seemecnc/Orion_Delta/USER_MANUAL/images/set-zero-point.jpg

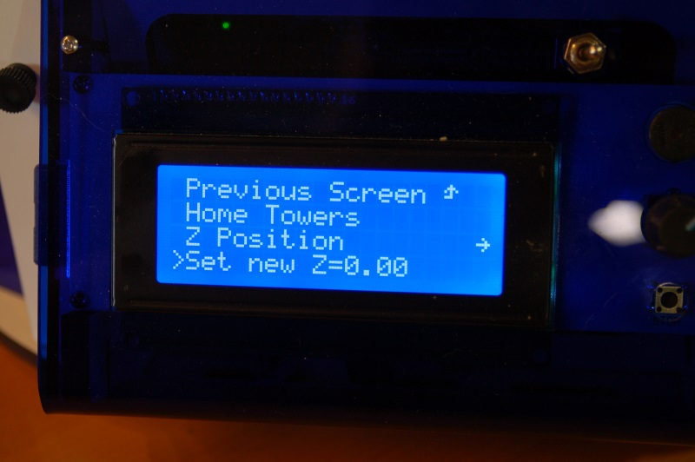
USER_MANUAL/images/set-zero-point.jpg
