seemecnc/Orion_Delta/USER_MANUAL/images/10858079405_2d53c97f4e_c.jpg

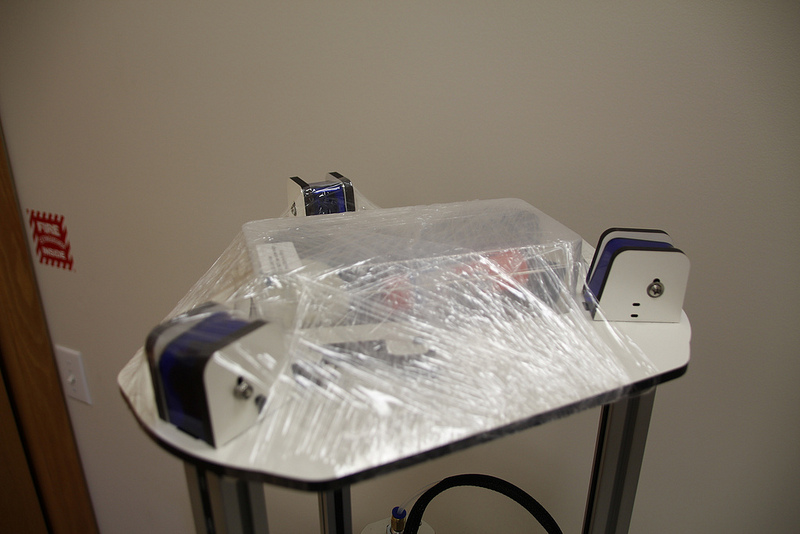
USER_MANUAL/images/10858079405_2d53c97f4e_c.jpg
