seemecnc/Orion_Delta/CAD/IGES/Switch Micro Lever.IGS

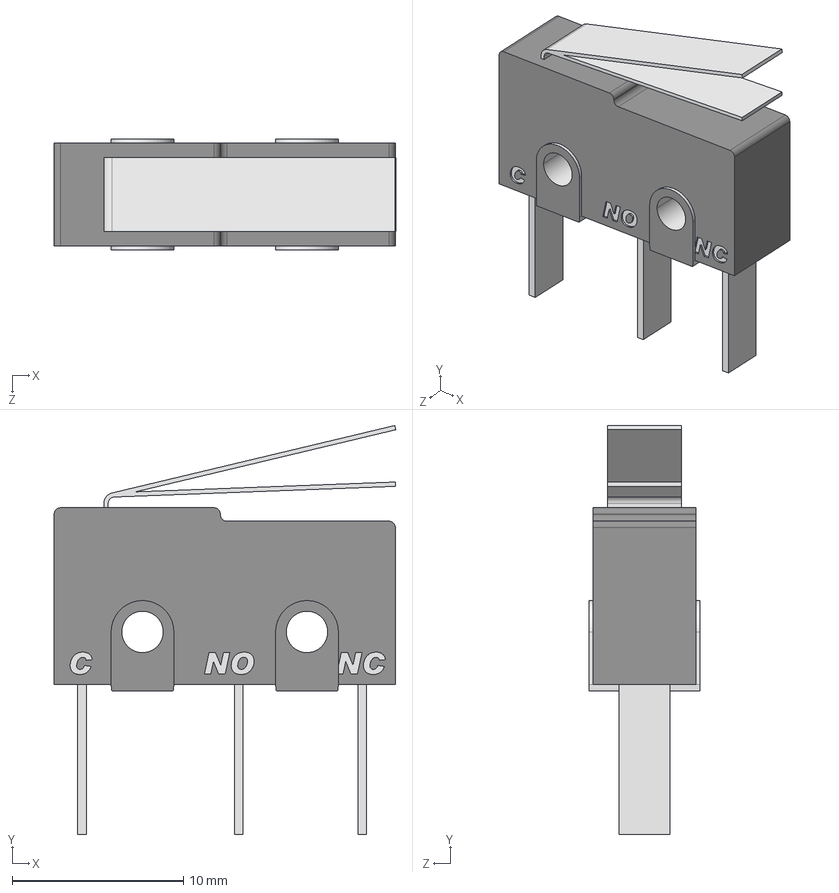
[picture p18: CAD file, 2013-10-02]
CAD/IGES/Switch Micro Lever.IGS
19.9 x 23.9 x 6.48 mm
