seemecnc/Orion_Delta/CAD/IGES/40mmFAN.IGS

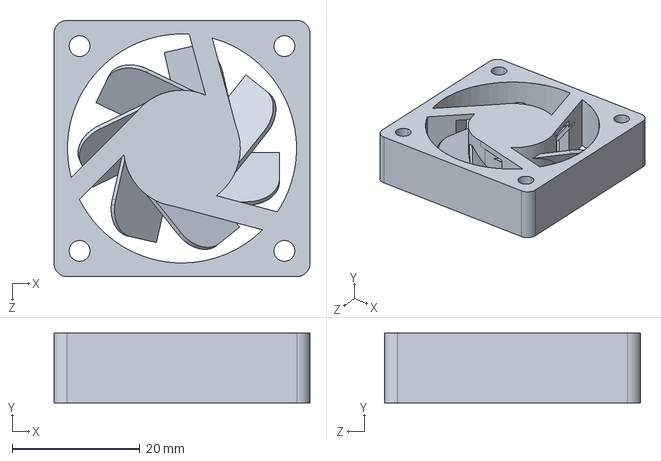
[picture p19: CAD file, 2013-10-02]
CAD/IGES/40mmFAN.IGS
40.0 x 10.9 x 40.0 mm
