seemecnc/Orion_Delta/CAD/IGES/spacer.IGS

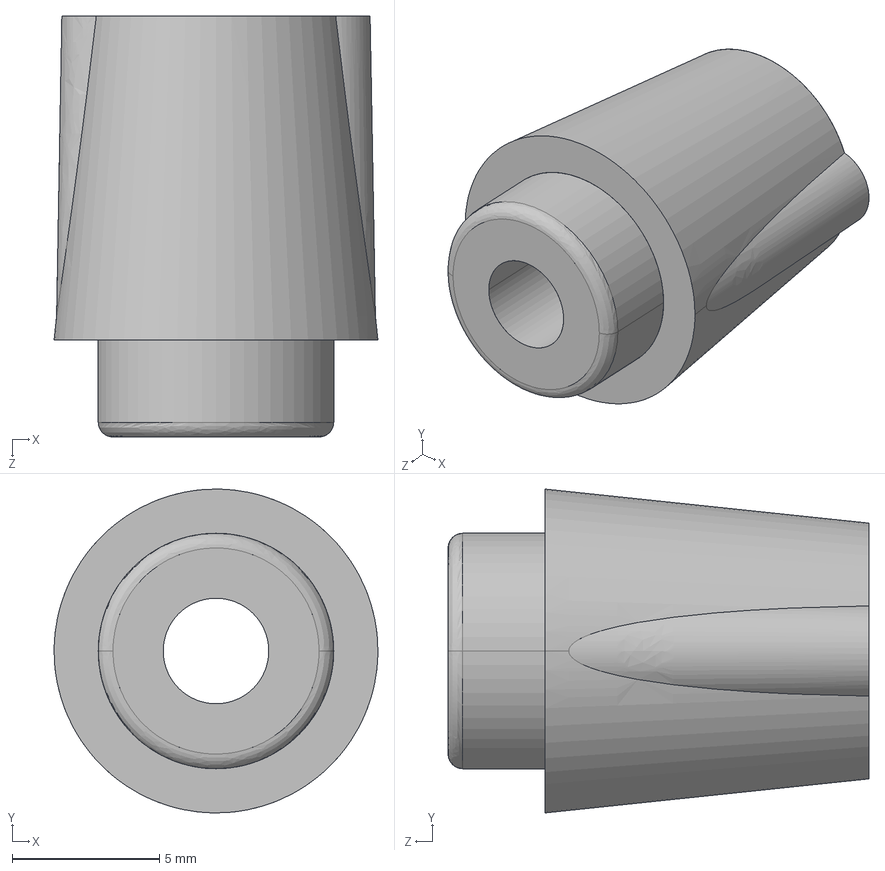
[picture p20: CAD file, 2013-10-02]
CAD/IGES/spacer.IGS
11.0 x 11.0 x 14.3 mm
