seemecnc/Orion_Delta/USER_MANUAL/images/3d-view-keychain.png

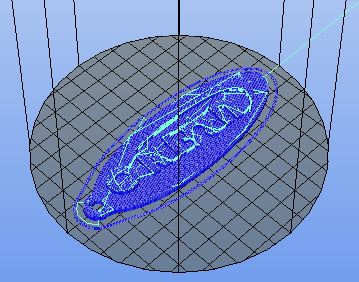
USER_MANUAL/images/3d-view-keychain.png
