seemecnc/Orion_Delta/USER_MANUAL/images/20deg.jpg

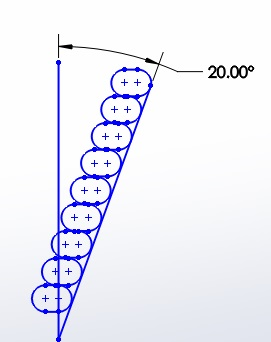
USER_MANUAL/images/20deg.jpg
