seemecnc/Orion_Delta/USER_MANUAL/images/45deg.jpg

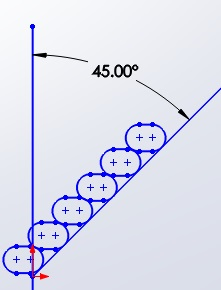
USER_MANUAL/images/45deg.jpg
