seemecnc/Orion_Delta/USER_MANUAL/images/75deg.jpg

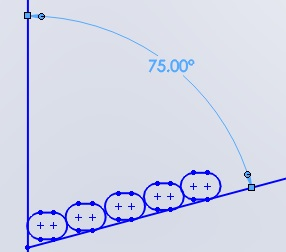
USER_MANUAL/images/75deg.jpg
