seemecnc/Orion_Delta/USER_MANUAL/images/10857993875_b573bbbdb2_c.jpg

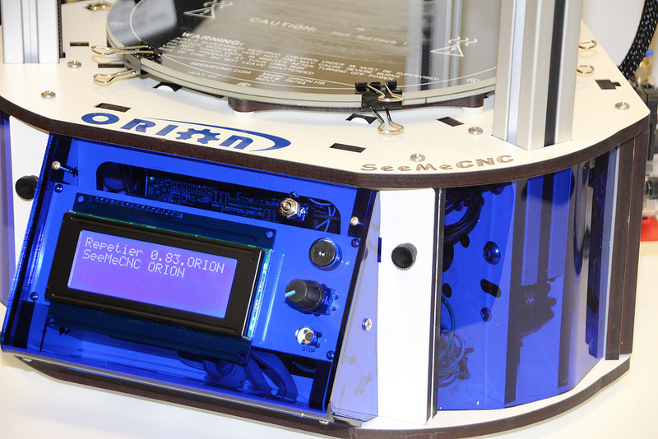
USER_MANUAL/images/10857993875_b573bbbdb2_c.jpg
