seemecnc/Orion_Delta/USER_MANUAL/images/10857997695_c42692fac6_c.jpg

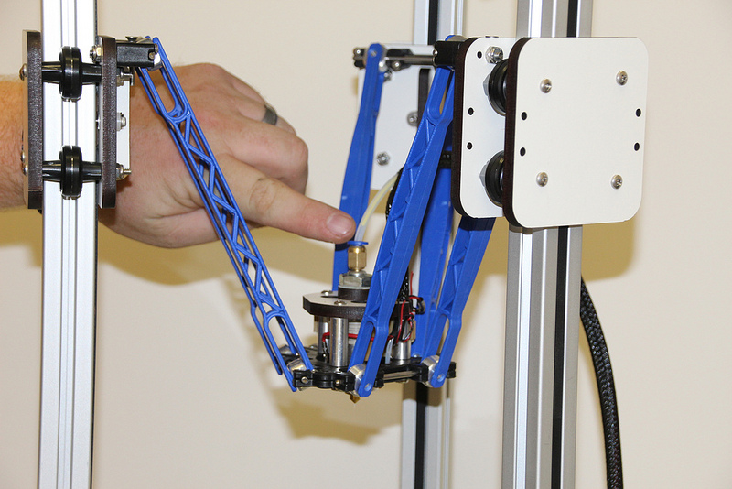
USER_MANUAL/images/10857997695_c42692fac6_c.jpg
