seemecnc/Orion_Delta/USER_MANUAL/images/10857999175_edf28102e8_c.jpg

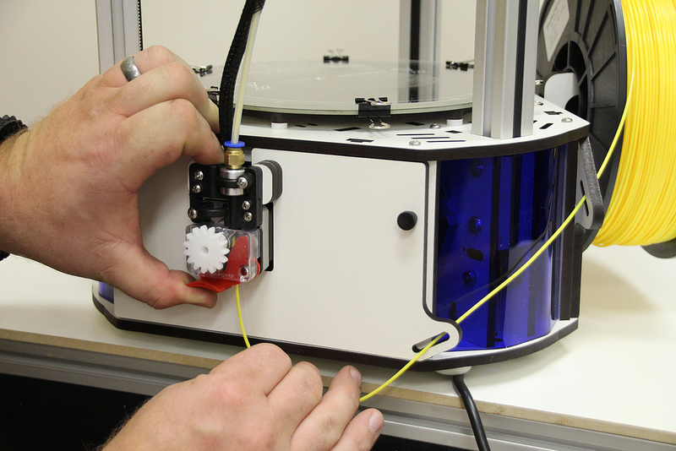
USER_MANUAL/images/10857999175_edf28102e8_c.jpg
