seemecnc/Orion_Delta/USER_MANUAL/images/10858003085_644f556bda_c.jpg

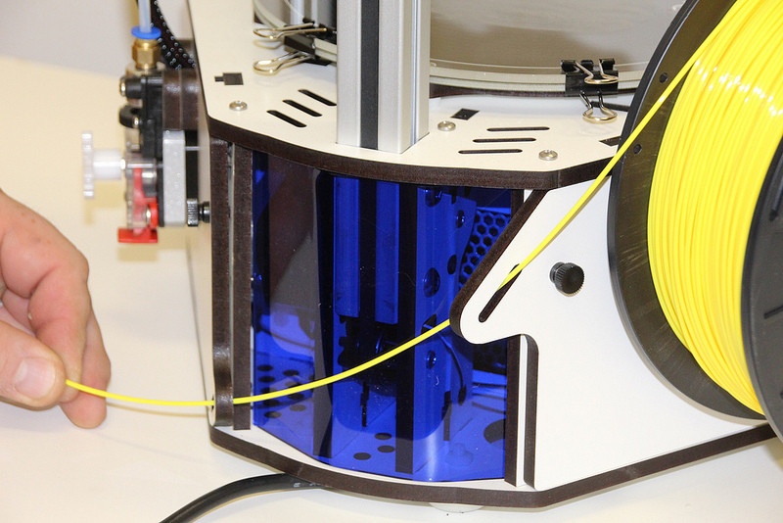
USER_MANUAL/images/10858003085_644f556bda_c.jpg
