seemecnc/Orion_Delta/USER_MANUAL/images/10858004465_a517190b95_c.jpg

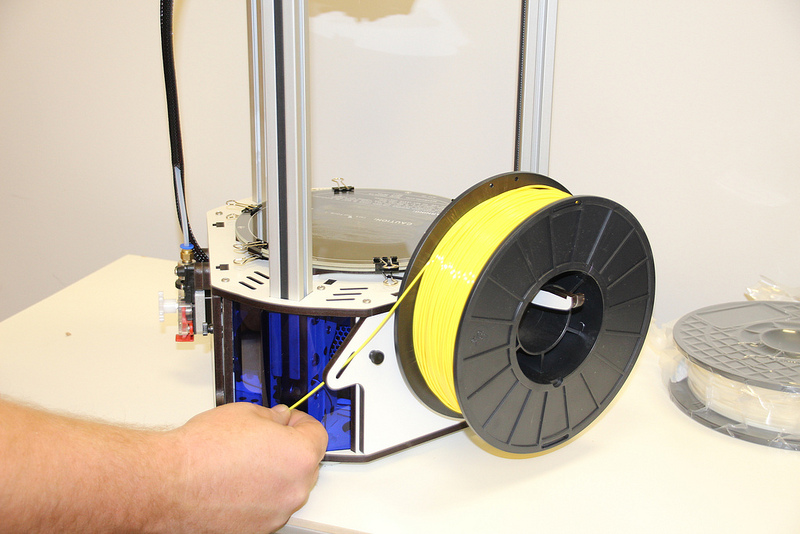
USER_MANUAL/images/10858004465_a517190b95_c.jpg
