seemecnc/Orion_Delta/USER_MANUAL/images/10858016405_97d147c111_c.jpg

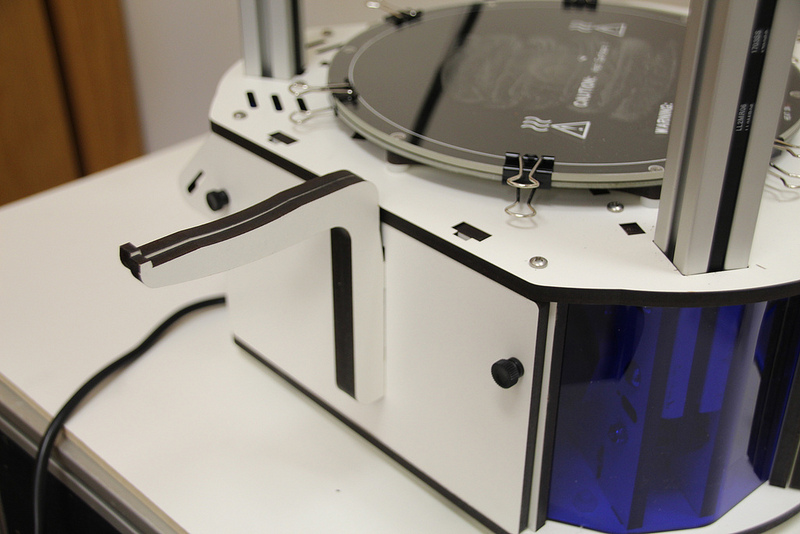
USER_MANUAL/images/10858016405_97d147c111_c.jpg
