seemecnc/Orion_Delta/USER_MANUAL/images/10858027235_418935b61d_c.jpg

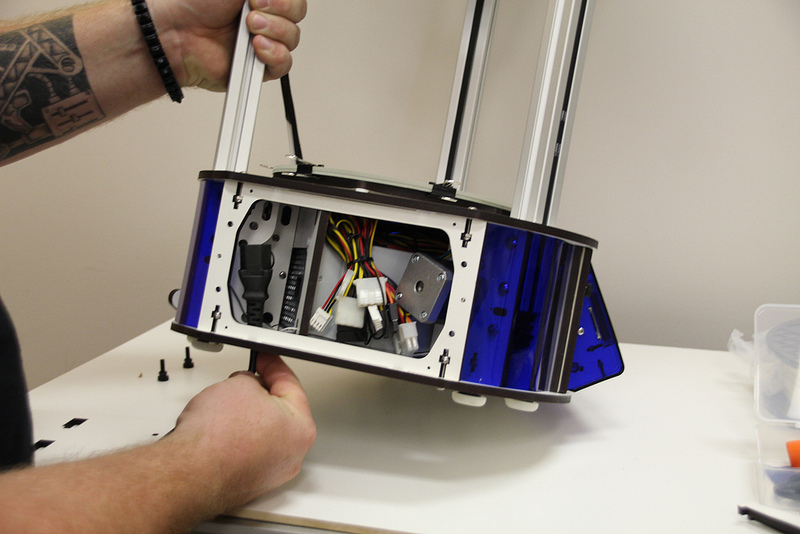
USER_MANUAL/images/10858027235_418935b61d_c.jpg
