seemecnc/Orion_Delta/USER_MANUAL/images/10858029525_48f6b91417_c.jpg

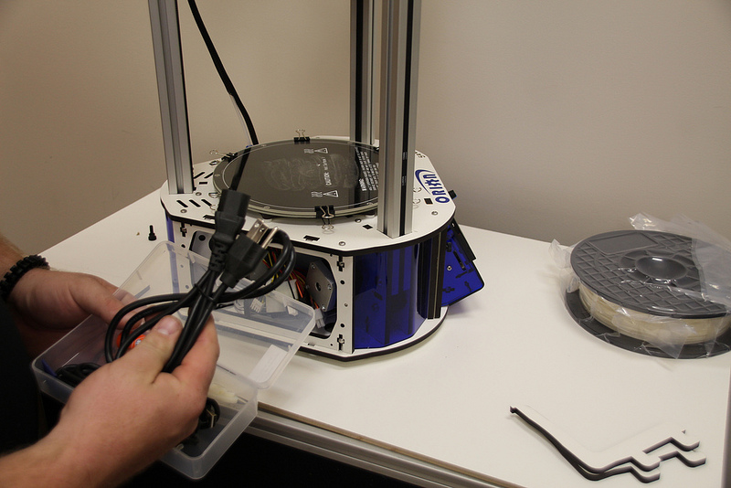
USER_MANUAL/images/10858029525_48f6b91417_c.jpg
