seemecnc/Orion_Delta/USER_MANUAL/images/10858043166_c10c539a0d_c.jpg

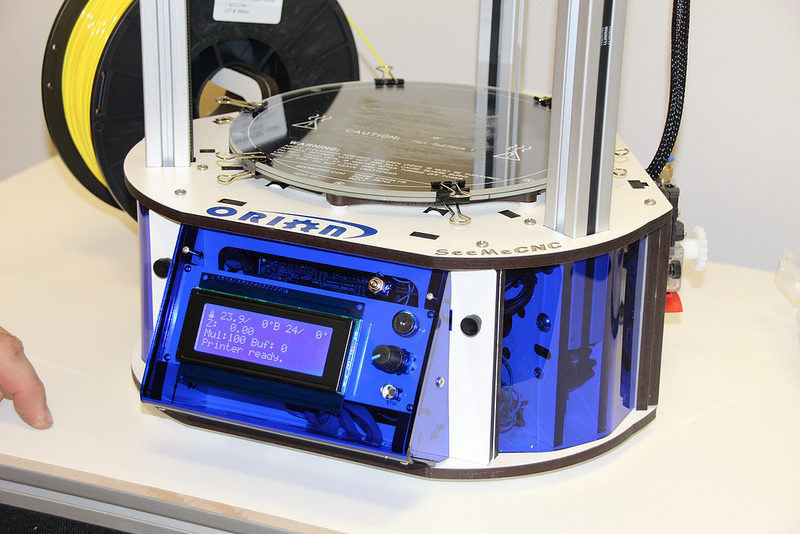
USER_MANUAL/images/10858043166_c10c539a0d_c.jpg
