seemecnc/Orion_Delta/USER_MANUAL/images/10858051416_cd726fda2a_c.jpg

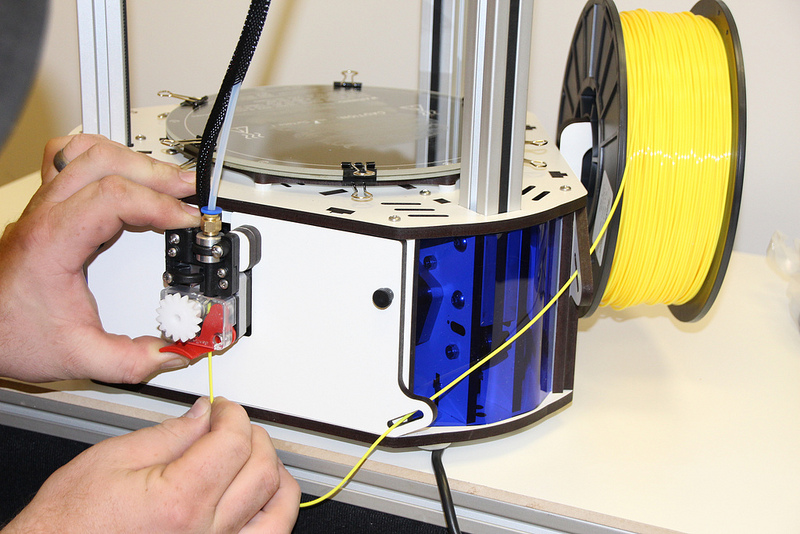
USER_MANUAL/images/10858051416_cd726fda2a_c.jpg
