seemecnc/Orion_Delta/USER_MANUAL/images/10858056896_ca6db3baf7_c.jpg

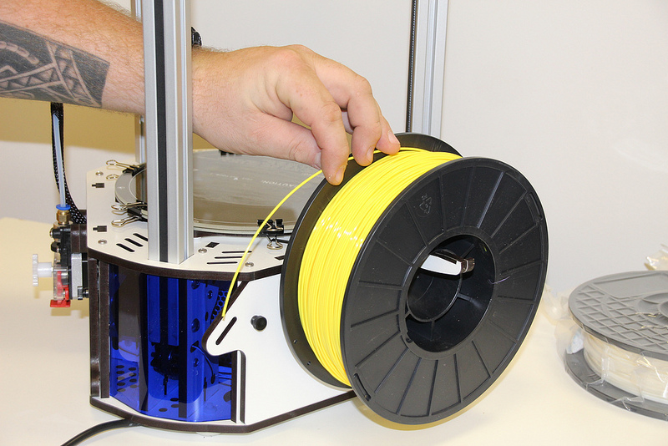
USER_MANUAL/images/10858056896_ca6db3baf7_c.jpg
