seemecnc/Orion_Delta/USER_MANUAL/images/10858063376_e0e1a32779_c.jpg

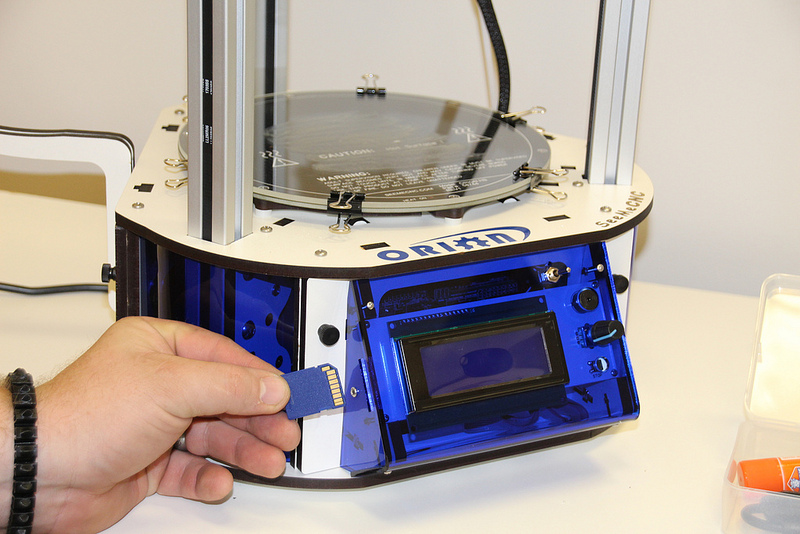
USER_MANUAL/images/10858063376_e0e1a32779_c.jpg
