seemecnc/Orion_Delta/USER_MANUAL/images/10858071566_8f59dc56c1_c.jpg

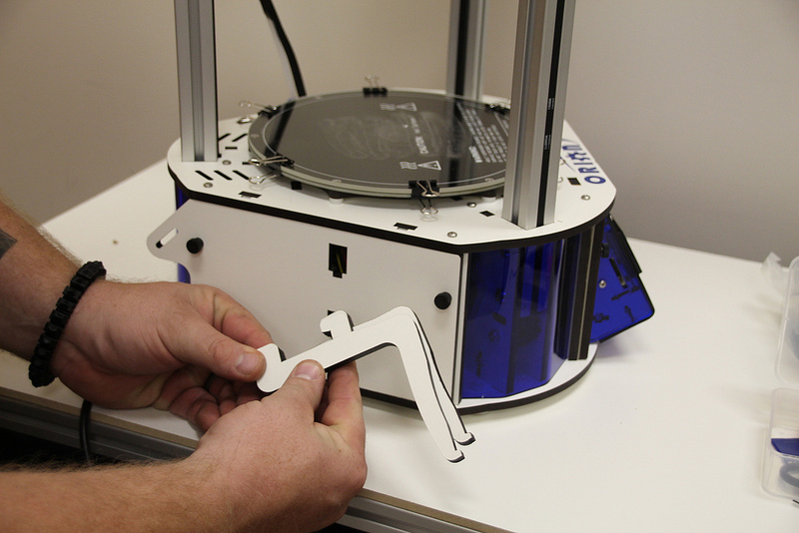
USER_MANUAL/images/10858071566_8f59dc56c1_c.jpg
