seemecnc/Orion_Delta/USER_MANUAL/images/10858087996_081414d4be_c.jpg

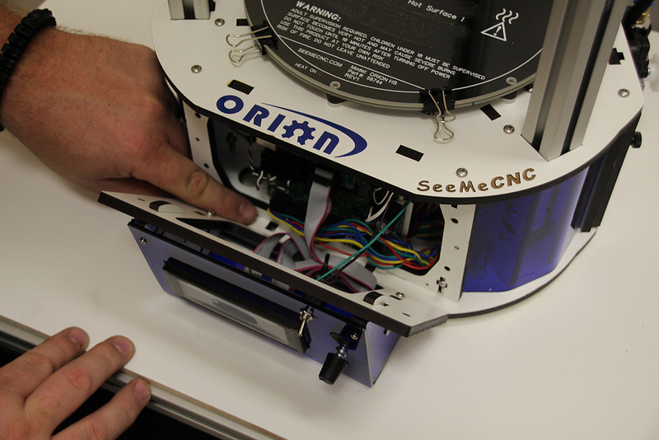
USER_MANUAL/images/10858087996_081414d4be_c.jpg
