seemecnc/Orion_Delta/USER_MANUAL/images/10858104786_4468d310ae_c.jpg

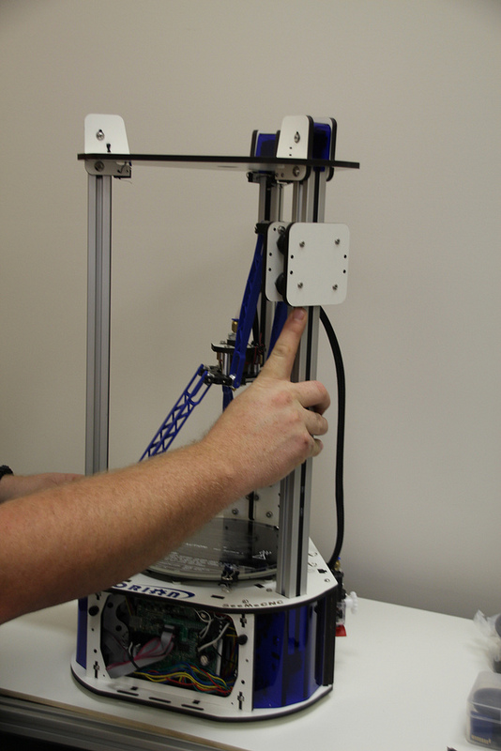
USER_MANUAL/images/10858104786_4468d310ae_c.jpg
