seemecnc/Orion_Delta/USER_MANUAL/images/10858115596_f1e3a82ac3_c.jpg

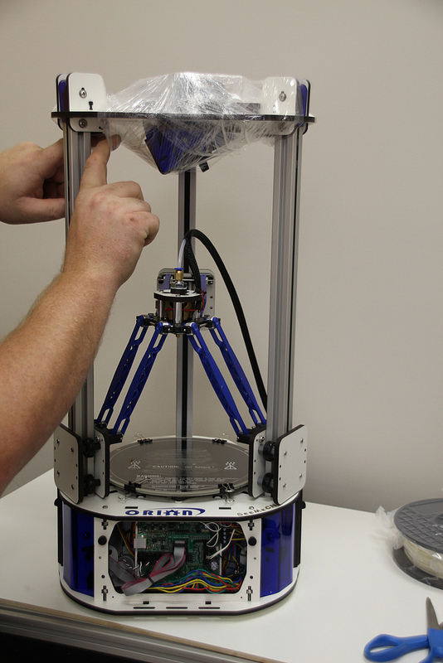
USER_MANUAL/images/10858115596_f1e3a82ac3_c.jpg
