seemecnc/Orion_Delta/USER_MANUAL/images/10858133396_417945009c_c.jpg

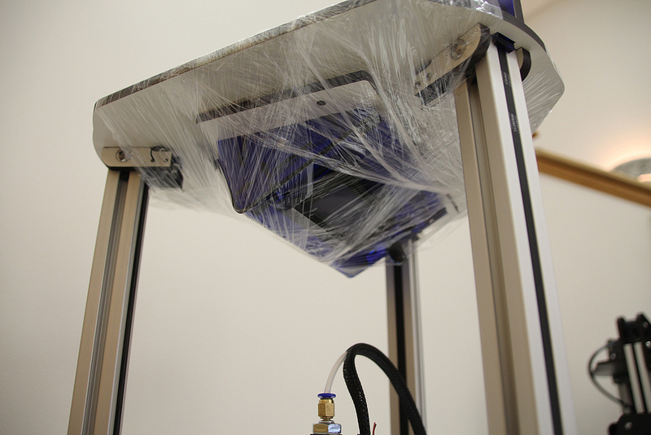
USER_MANUAL/images/10858133396_417945009c_c.jpg
