seemecnc/Orion_Delta/USER_MANUAL/images/10858134636_70626f2765_c.jpg

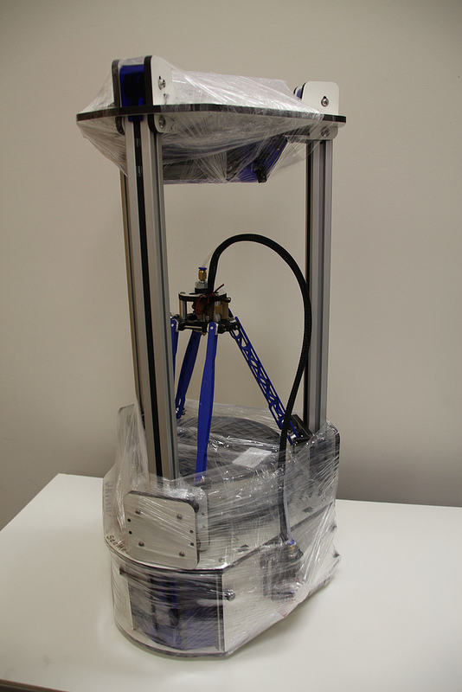
USER_MANUAL/images/10858134636_70626f2765_c.jpg
