seemecnc/Orion_Delta/USER_MANUAL/images/10858135606_6d0c017a09_c.jpg

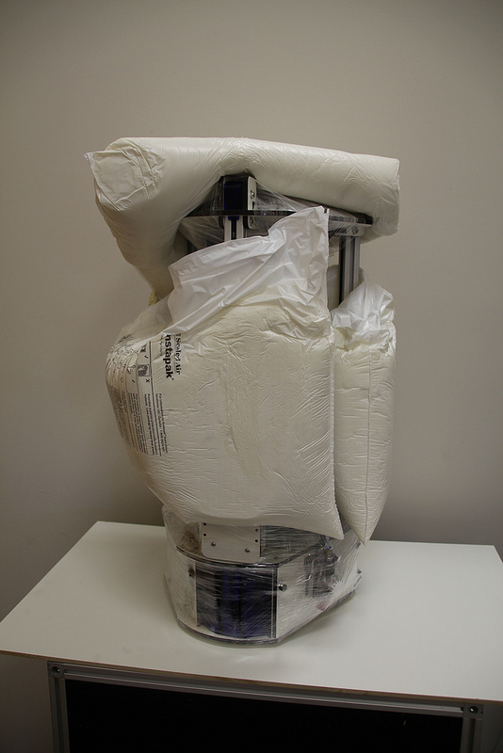
USER_MANUAL/images/10858135606_6d0c017a09_c.jpg
