seemecnc/Orion_Delta/USER_MANUAL/images/10858138586_e7d71295ff_c.jpg

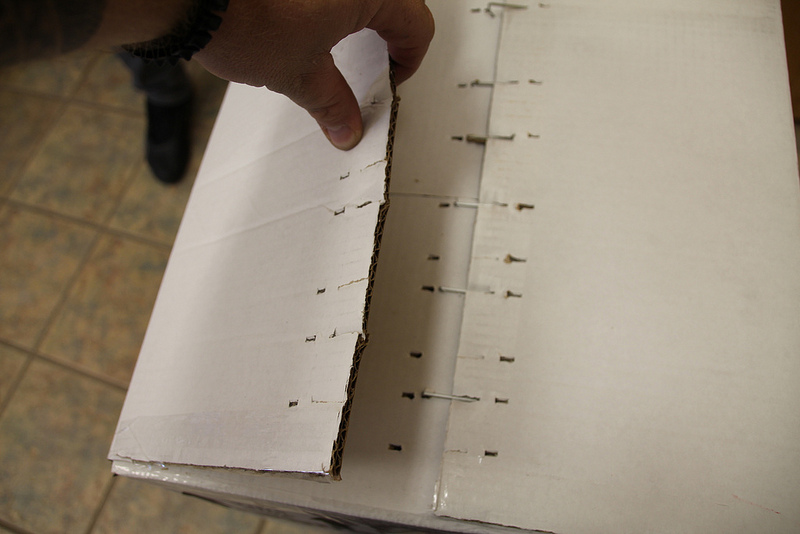
USER_MANUAL/images/10858138586_e7d71295ff_c.jpg
