seemecnc/Orion_Delta/USER_MANUAL/images/10858149814_d947ce7413_c.jpg

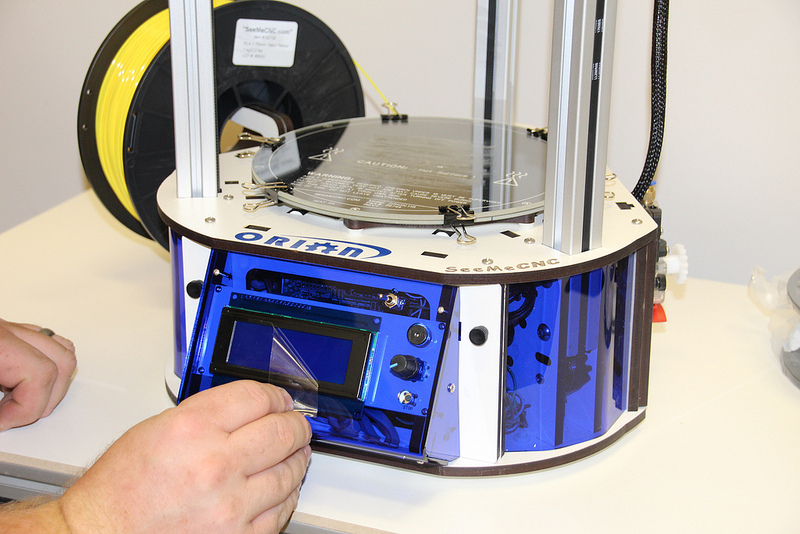
USER_MANUAL/images/10858149814_d947ce7413_c.jpg
