seemecnc/Orion_Delta/USER_MANUAL/images/10858156424_11ed93d5b6_c.jpg

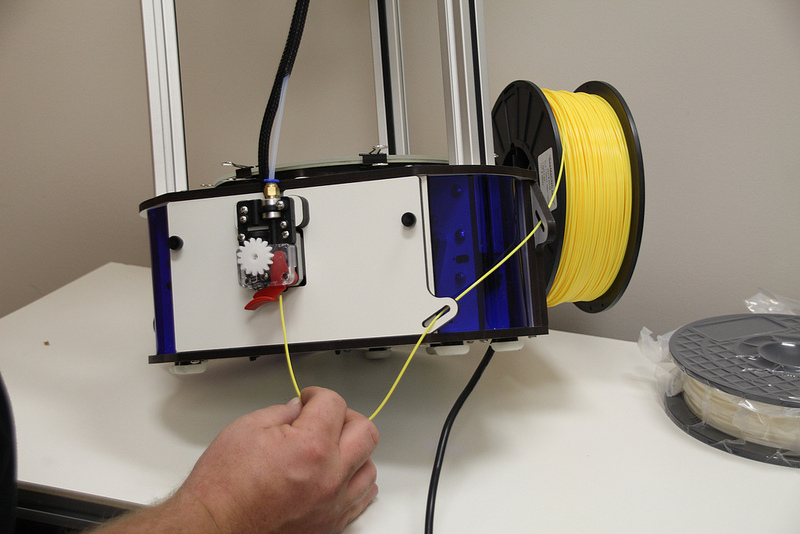
USER_MANUAL/images/10858156424_11ed93d5b6_c.jpg
