seemecnc/Orion_Delta/USER_MANUAL/images/10858165754_4ae52a8649_c.jpg

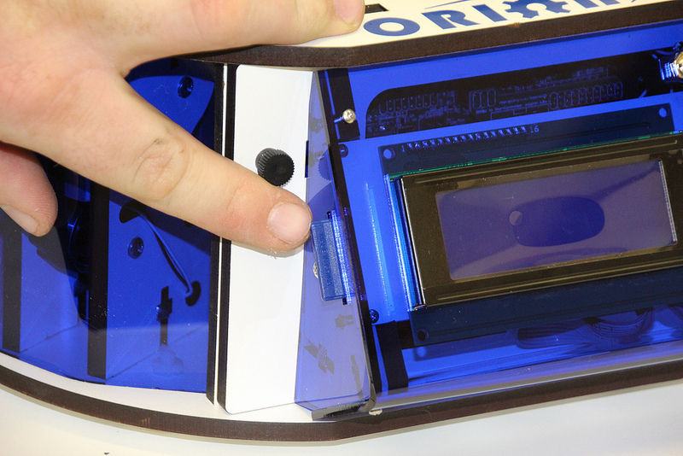
USER_MANUAL/images/10858165754_4ae52a8649_c.jpg
