seemecnc/Orion_Delta/USER_MANUAL/images/10858187334_f6d8ebac16_c.jpg

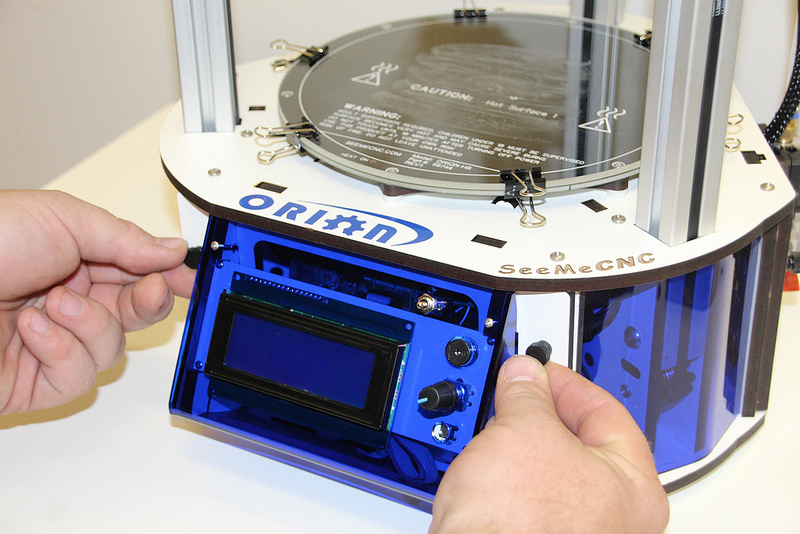
USER_MANUAL/images/10858187334_f6d8ebac16_c.jpg
