seemecnc/Orion_Delta/USER_MANUAL/images/10858193964_cc0fbacdeb_c.jpg

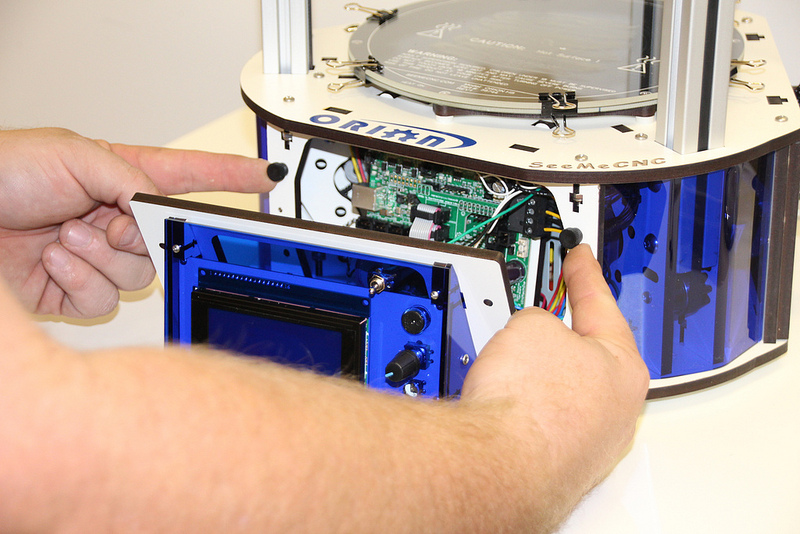
USER_MANUAL/images/10858193964_cc0fbacdeb_c.jpg
