seemecnc/Orion_Delta/USER_MANUAL/images/10858195264_8df696b53b_c.jpg

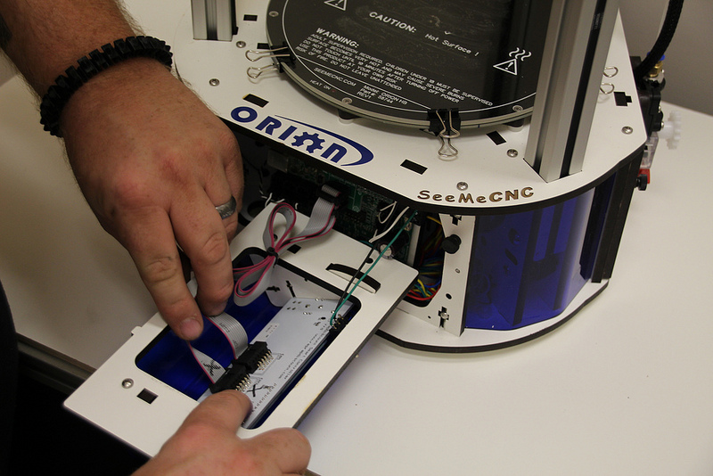
USER_MANUAL/images/10858195264_8df696b53b_c.jpg
