seemecnc/Orion_Delta/USER_MANUAL/images/10858196814_af65e72ff8_c.jpg

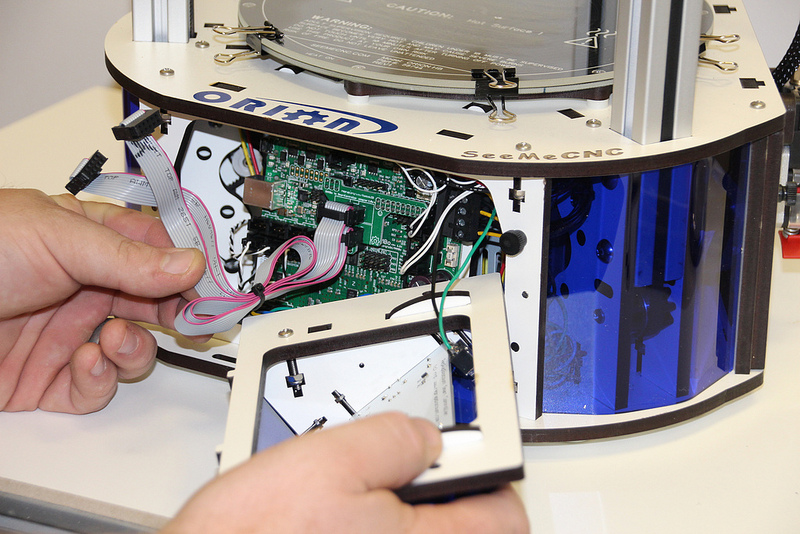
USER_MANUAL/images/10858196814_af65e72ff8_c.jpg
