seemecnc/Orion_Delta/USER_MANUAL/images/10858198144_2c69749b12_c.jpg

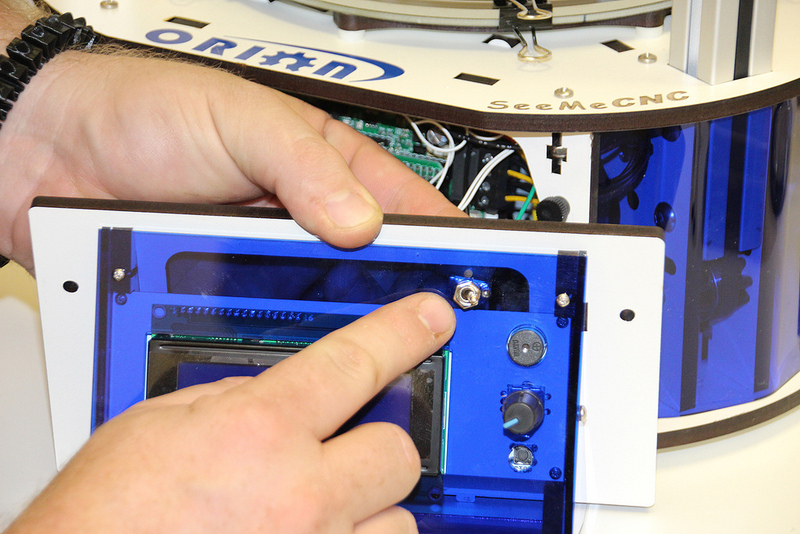
USER_MANUAL/images/10858198144_2c69749b12_c.jpg
