seemecnc/Orion_Delta/USER_MANUAL/images/10858201544_ca3241cb73_c.jpg

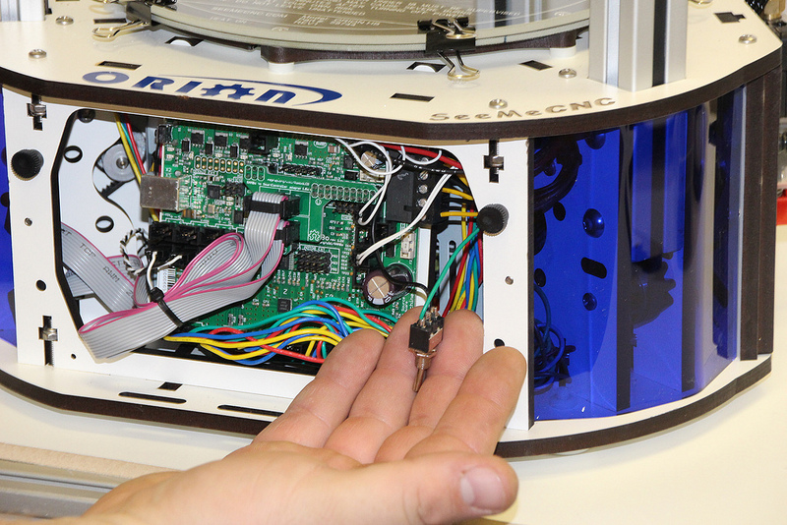
USER_MANUAL/images/10858201544_ca3241cb73_c.jpg
