seemecnc/Orion_Delta/USER_MANUAL/images/10858215504_7f9ed28df2_c.jpg

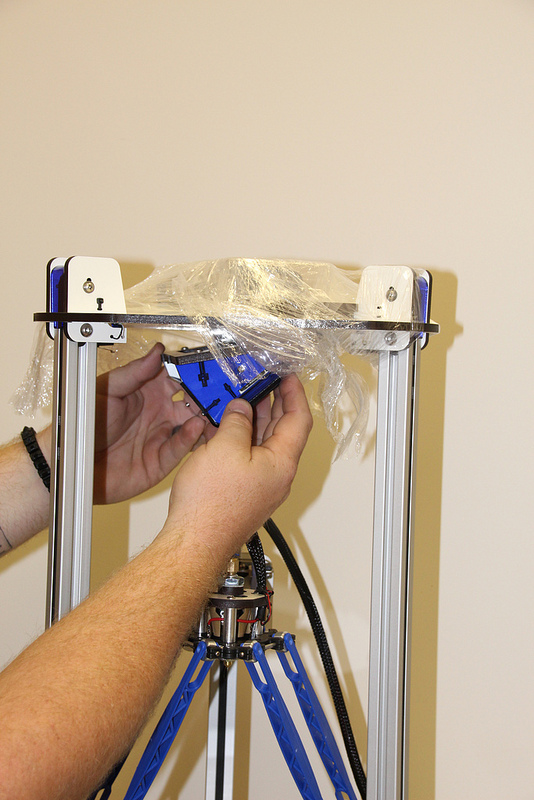
USER_MANUAL/images/10858215504_7f9ed28df2_c.jpg
