seemecnc/Orion_Delta/USER_MANUAL/images/10858355013_c423ee9d34_c.jpg

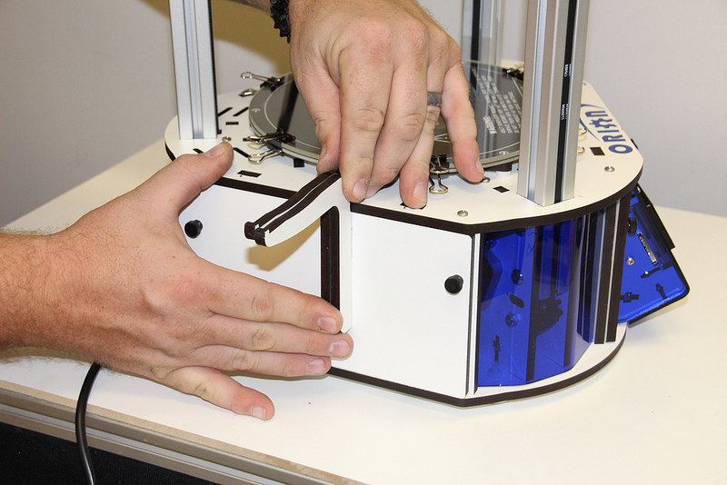
USER_MANUAL/images/10858355013_c423ee9d34_c.jpg
