seemecnc/Orion_Delta/USER_MANUAL/images/10858356373_2051489b07_c.jpg

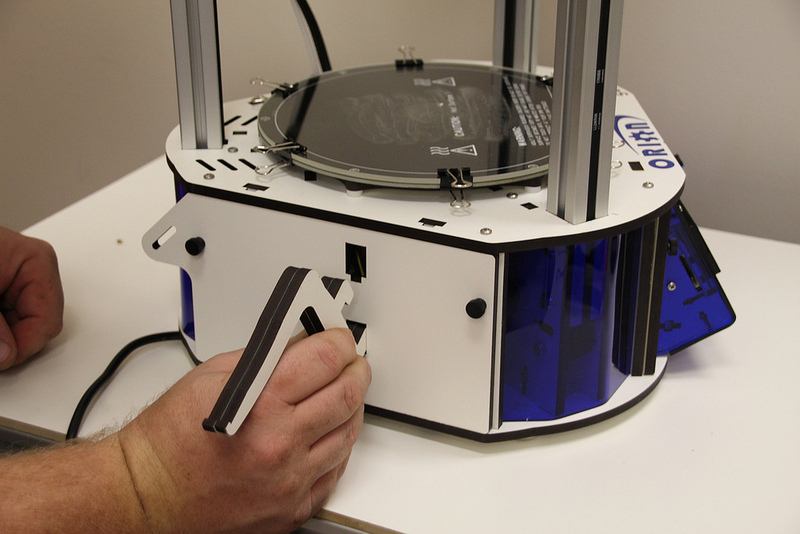
USER_MANUAL/images/10858356373_2051489b07_c.jpg
