seemecnc/Orion_Delta/USER_MANUAL/images/10858360663_d777211012_c.jpg

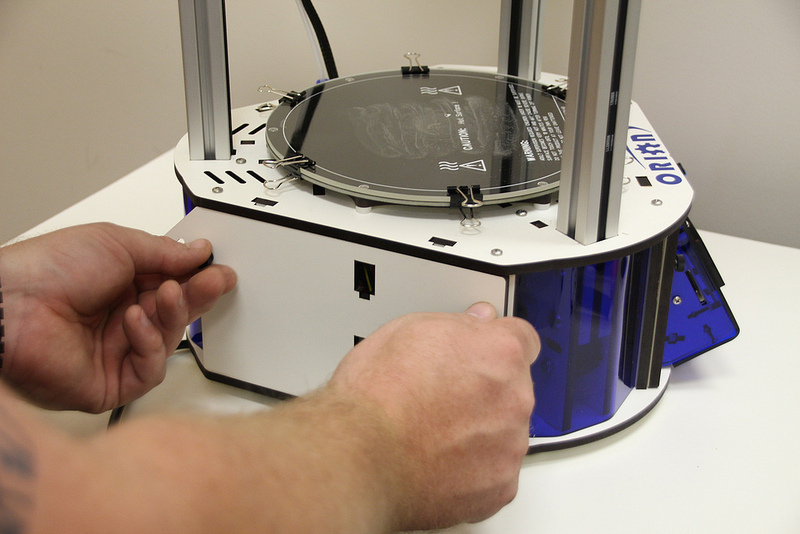
USER_MANUAL/images/10858360663_d777211012_c.jpg
