seemecnc/Orion_Delta/USER_MANUAL/images/10858363363_4431cff72f_c.jpg

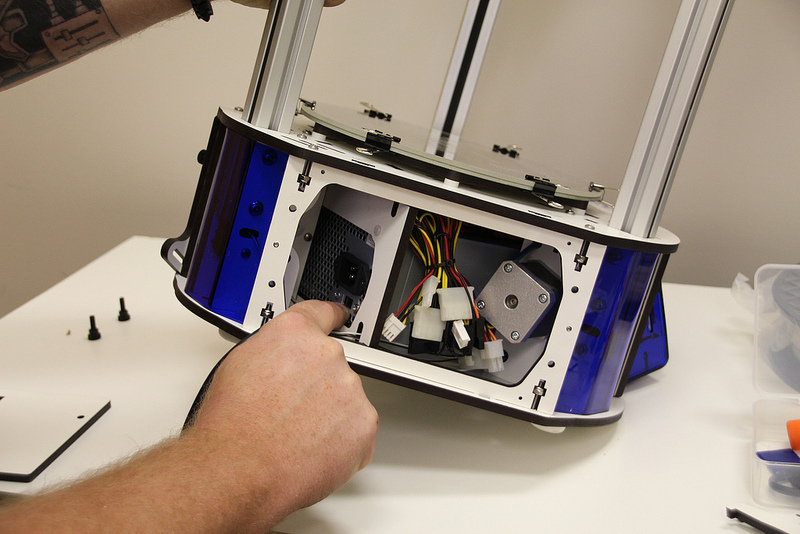
USER_MANUAL/images/10858363363_4431cff72f_c.jpg
