seemecnc/Orion_Delta/USER_MANUAL/images/10858369133_35604c40fe_c.jpg

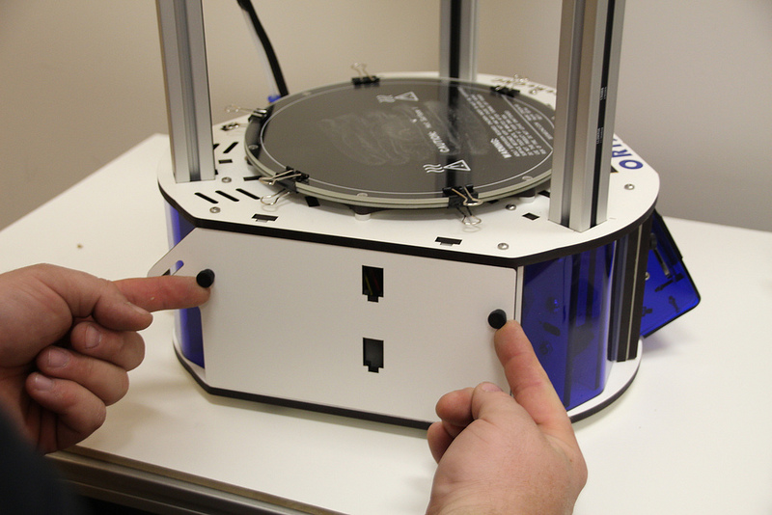
USER_MANUAL/images/10858369133_35604c40fe_c.jpg
