seemecnc/Orion_Delta/USER_MANUAL/images/10858371613_db3799a69a_c.jpg

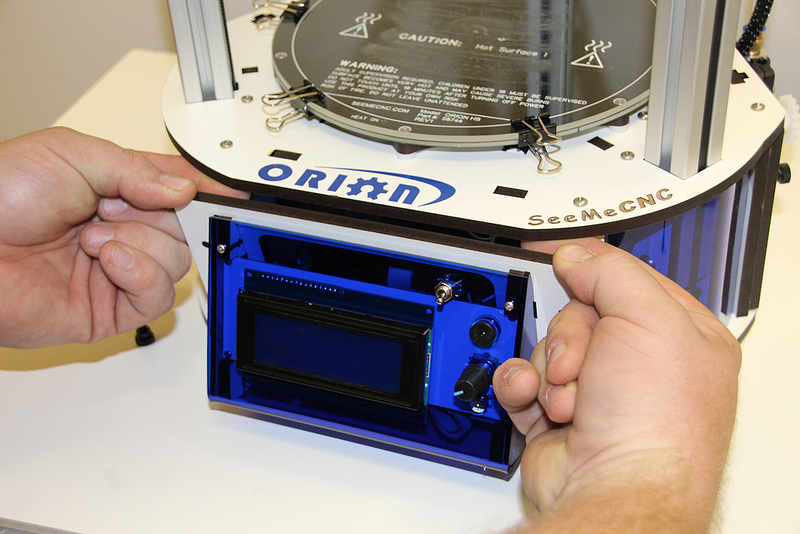
USER_MANUAL/images/10858371613_db3799a69a_c.jpg
