seemecnc/Orion_Delta/USER_MANUAL/images/10858372973_1e9f0c7b8a_c.jpg

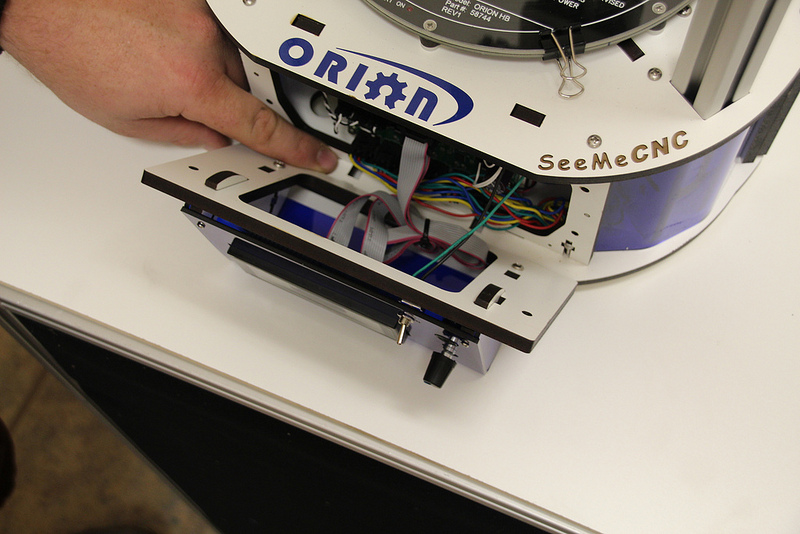
USER_MANUAL/images/10858372973_1e9f0c7b8a_c.jpg
