seemecnc/Orion_Delta/USER_MANUAL/images/10858383403_f076f69c96_c.jpg

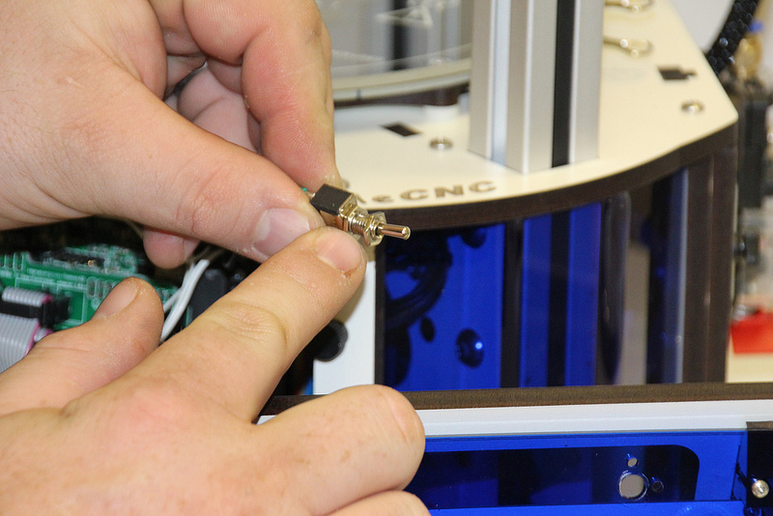
USER_MANUAL/images/10858383403_f076f69c96_c.jpg
