seemecnc/Orion_Delta/USER_MANUAL/images/10858387633_c5c9b00cb3_c.jpg

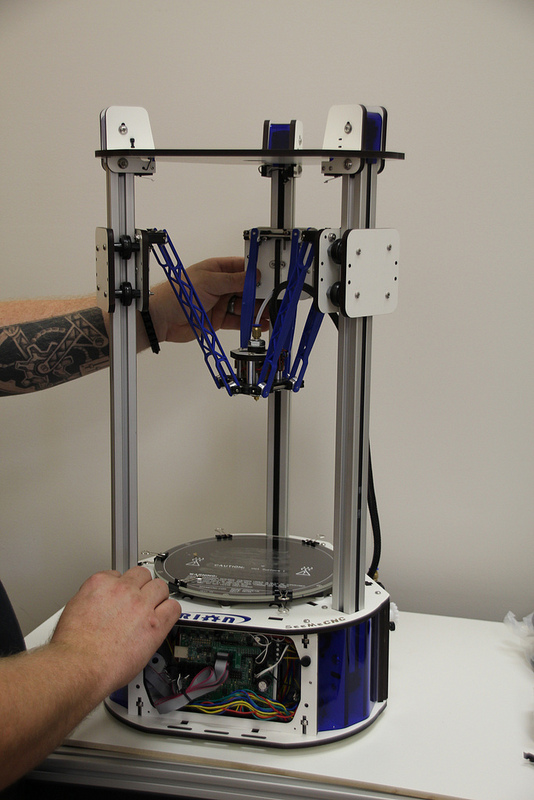
USER_MANUAL/images/10858387633_c5c9b00cb3_c.jpg
