seemecnc/Orion_Delta/USER_MANUAL/images/10858390063_a34ffba0bb_c.jpg

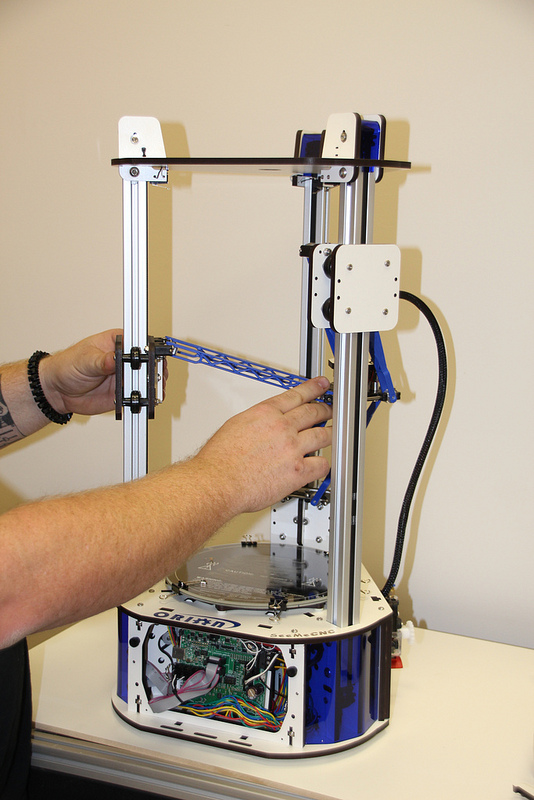
USER_MANUAL/images/10858390063_a34ffba0bb_c.jpg
