seemecnc/Orion_Delta/USER_MANUAL/images/10858397873_ab5069cfe1_c.jpg

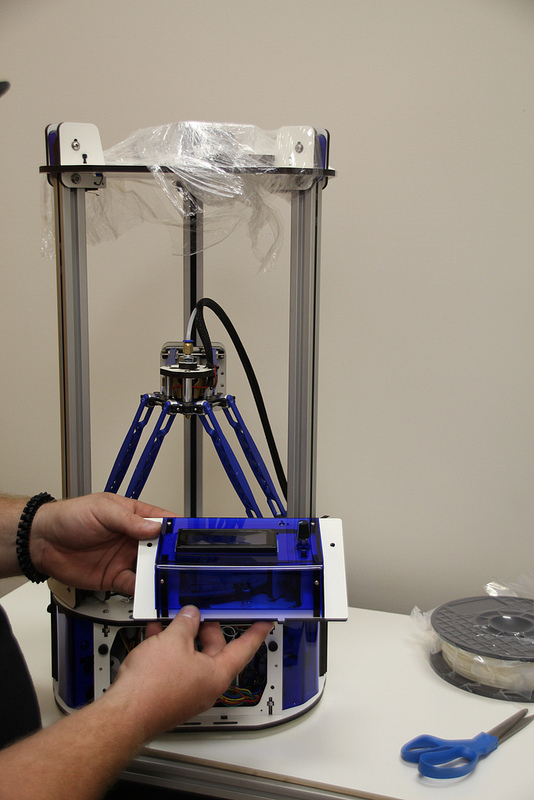
USER_MANUAL/images/10858397873_ab5069cfe1_c.jpg
