seemecnc/Orion_Delta/USER_MANUAL/images/10858415303_14522921b9_c.jpg

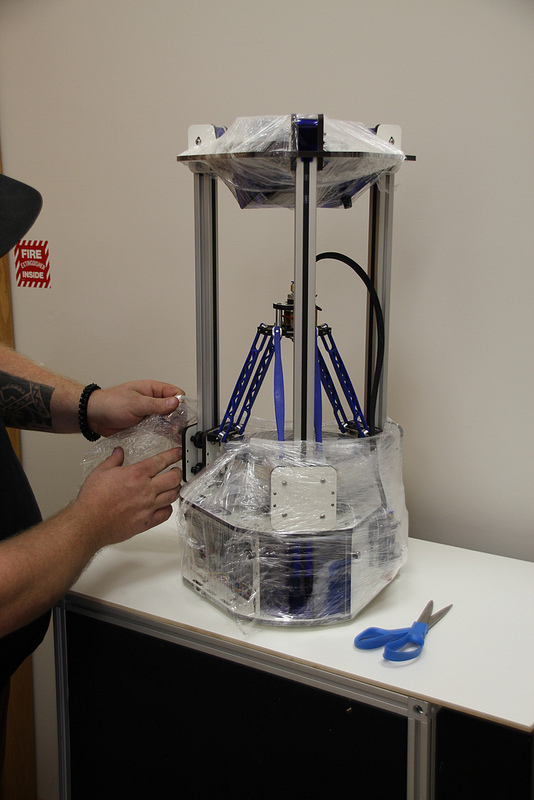
USER_MANUAL/images/10858415303_14522921b9_c.jpg
