seemecnc/Orion_Delta/USER_MANUAL/images/10858422893_585b8ddb39_c.jpg

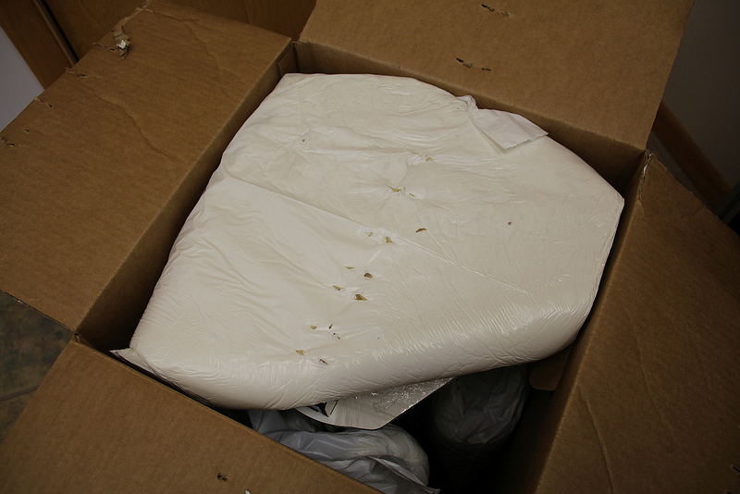
USER_MANUAL/images/10858422893_585b8ddb39_c.jpg
