seemecnc/Orion_Delta/USER_MANUAL/images/10858424663_5d82bfff20_c.jpg

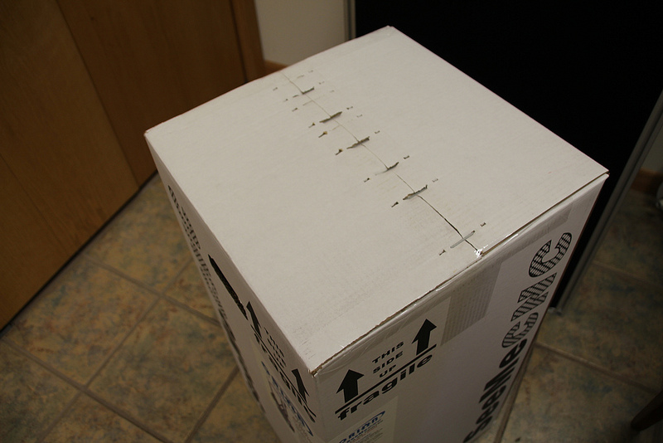
USER_MANUAL/images/10858424663_5d82bfff20_c.jpg
