seemecnc/Orion_Delta/USER_MANUAL/images/10858427153_edaa3dbe8b_c.jpg

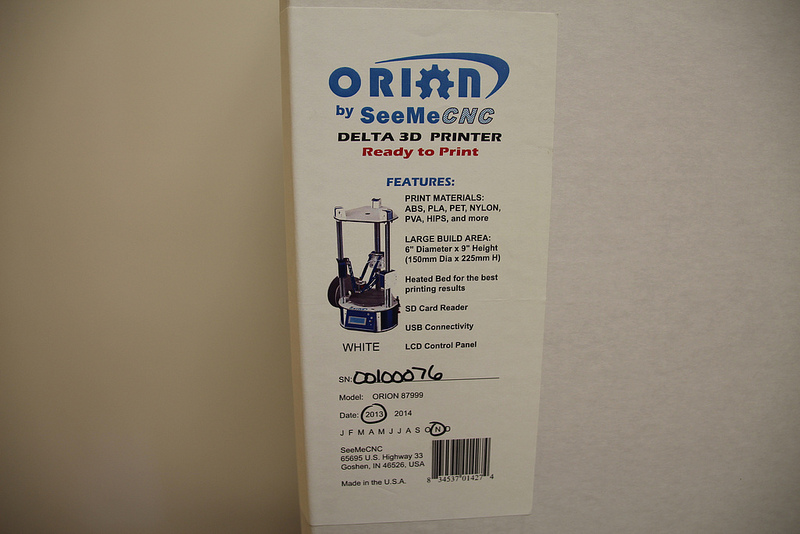
USER_MANUAL/images/10858427153_edaa3dbe8b_c.jpg
