seemecnc/Orion_Delta/USER_MANUAL/images/abs-preheat-demo.jpg

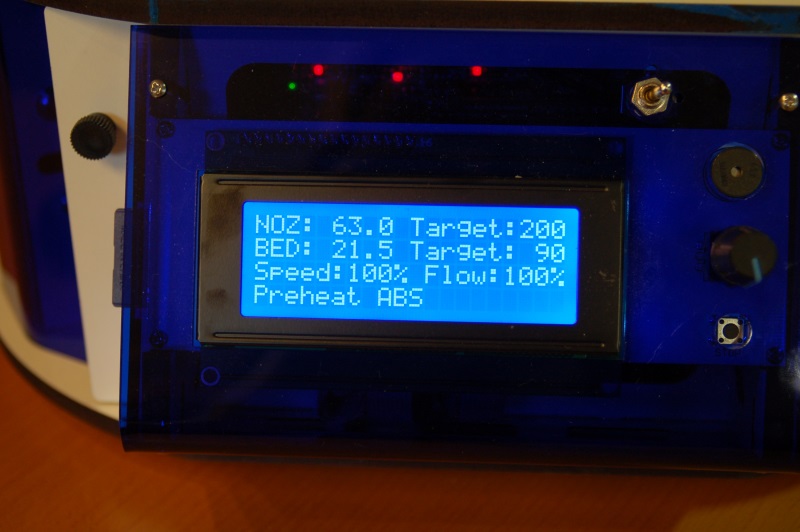
USER_MANUAL/images/abs-preheat-demo.jpg
