seemecnc/Orion_Delta/USER_MANUAL/images/adjust-temps.jpg

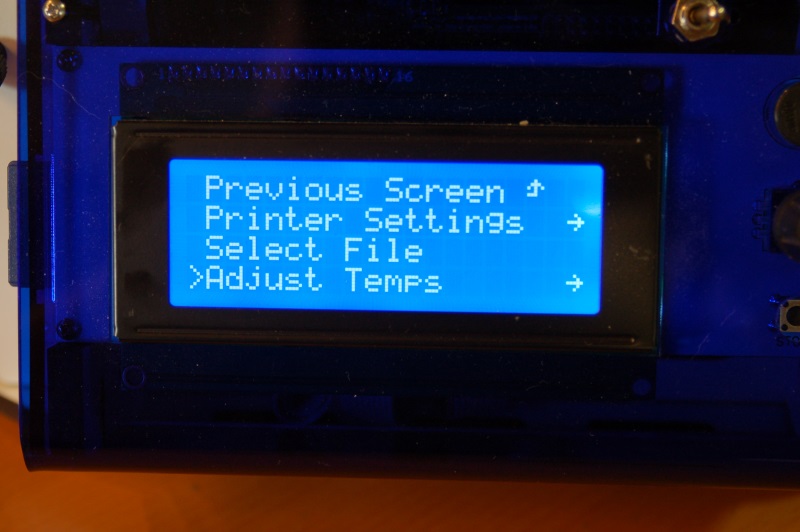
USER_MANUAL/images/adjust-temps.jpg
