seemecnc/Orion_Delta/USER_MANUAL/images/advanced-settings.jpg

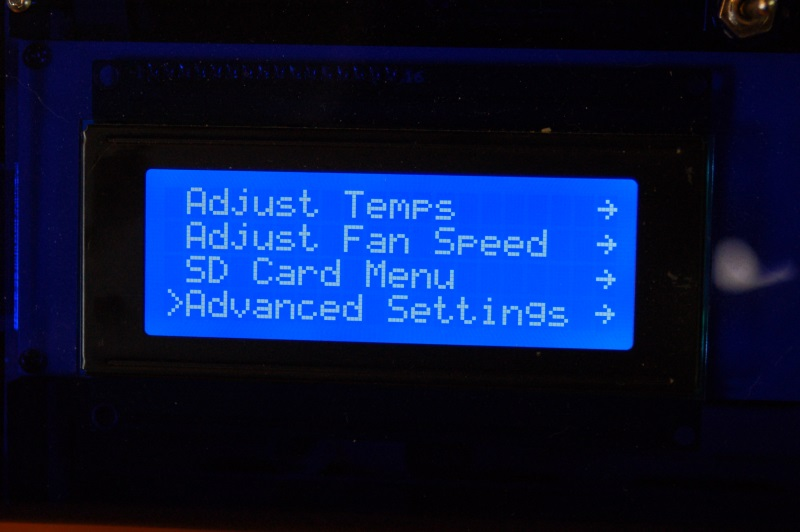
USER_MANUAL/images/advanced-settings.jpg
