seemecnc/Orion_Delta/USER_MANUAL/images/annotated-screen.jpg

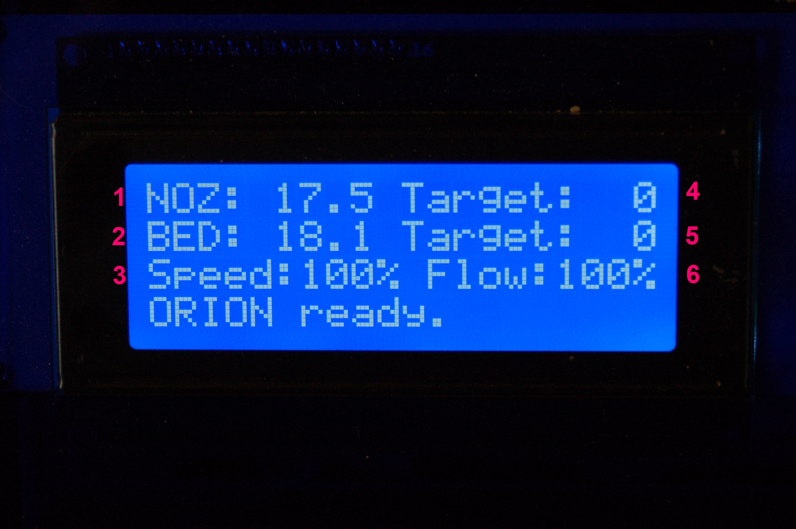
USER_MANUAL/images/annotated-screen.jpg
