seemecnc/Orion_Delta/USER_MANUAL/images/cal-dir.jpg

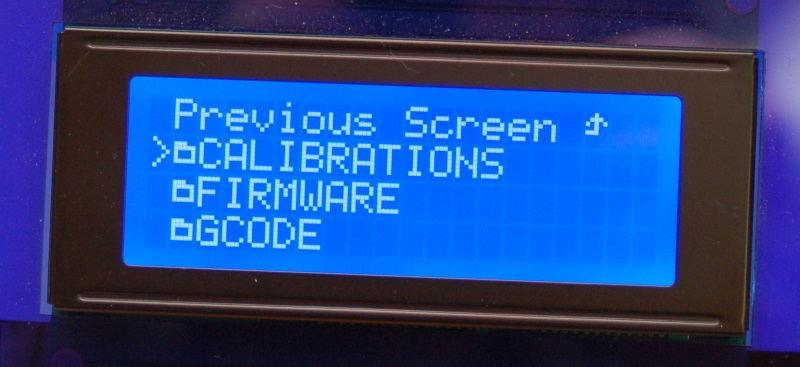
USER_MANUAL/images/cal-dir.jpg
