seemecnc/Orion_Delta/USER_MANUAL/images/cal-selected.jpg

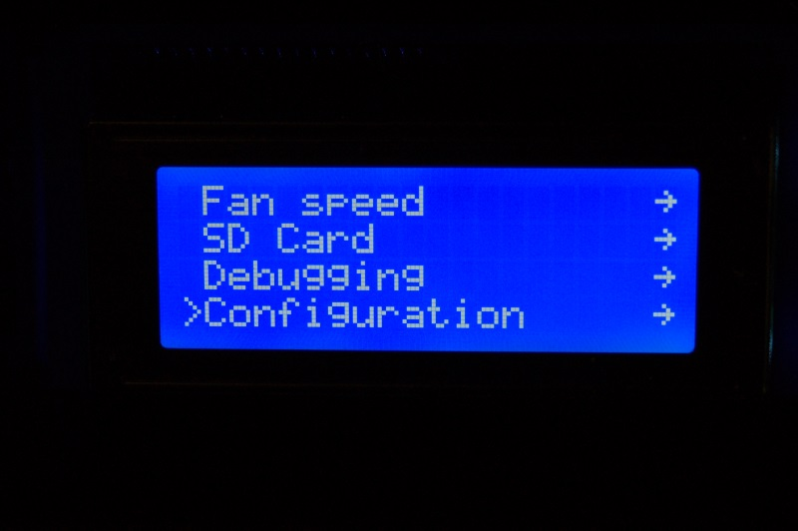
USER_MANUAL/images/cal-selected.jpg
