seemecnc/Orion_Delta/USER_MANUAL/images/cal-z-height.jpg

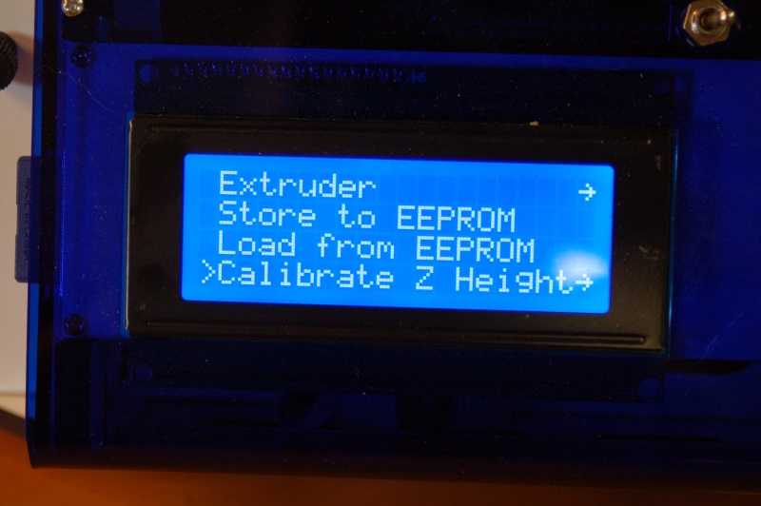
USER_MANUAL/images/cal-z-height.jpg
