seemecnc/Orion_Delta/USER_MANUAL/images/card-directory.jpg

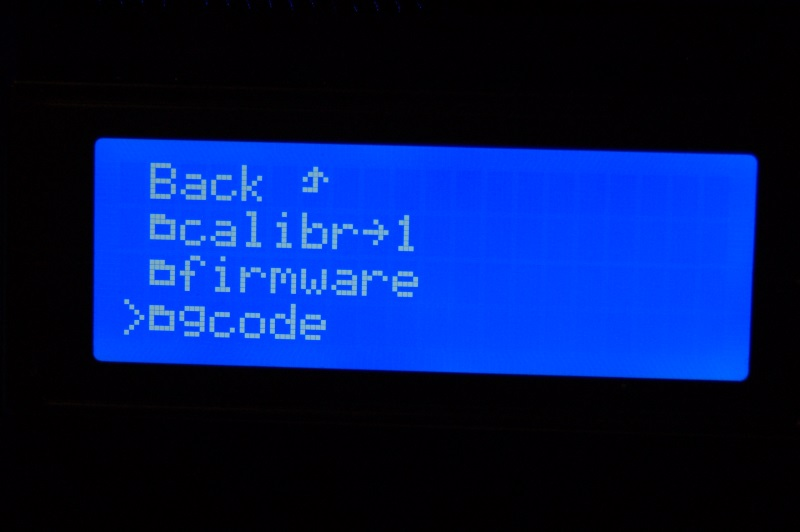
USER_MANUAL/images/card-directory.jpg
