seemecnc/Orion_Delta/USER_MANUAL/images/cut-objects.png

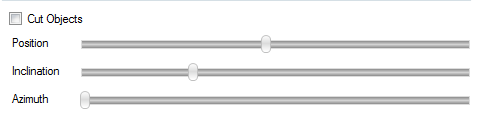
USER_MANUAL/images/cut-objects.png
