seemecnc/Orion_Delta/USER_MANUAL/images/delta-cal.jpg

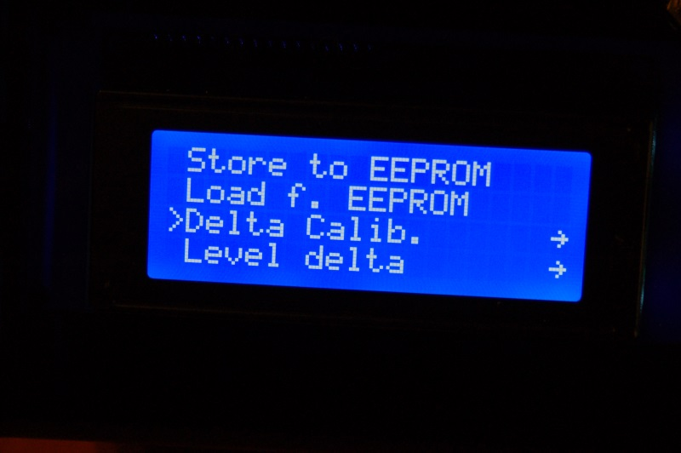
USER_MANUAL/images/delta-cal.jpg
