seemecnc/Orion_Delta/USER_MANUAL/images/disable-stepper-new.jpg

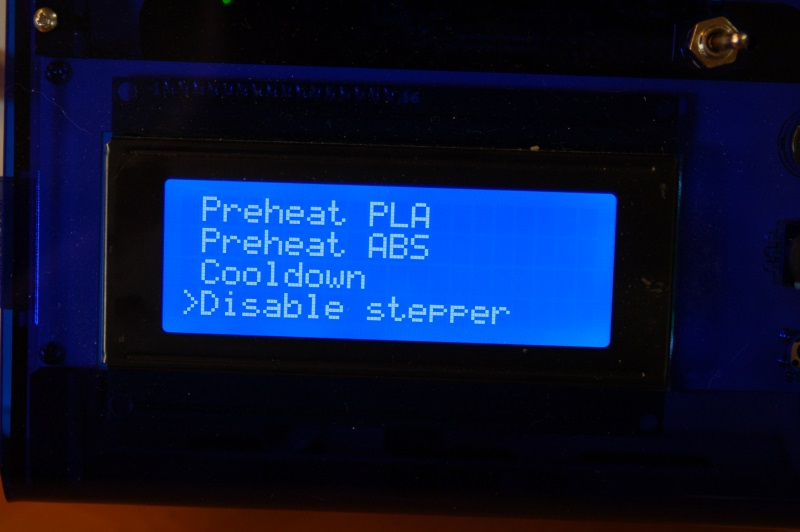
USER_MANUAL/images/disable-stepper-new.jpg
