seemecnc/Orion_Delta/USER_MANUAL/images/disable-stepper.jpg

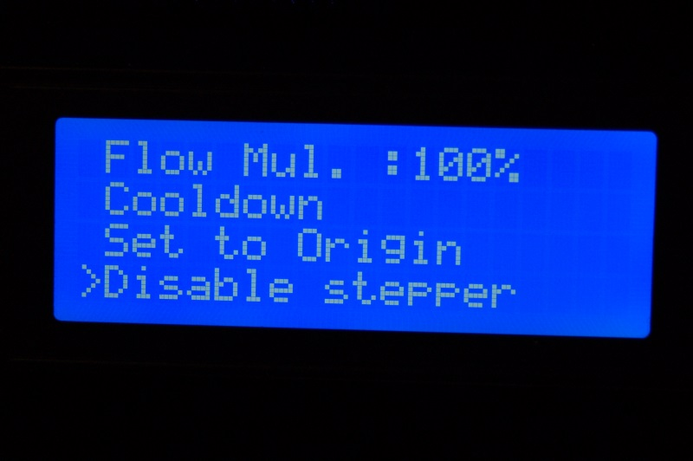
USER_MANUAL/images/disable-stepper.jpg
