seemecnc/Orion_Delta/USER_MANUAL/images/end-stop-tape.jpg

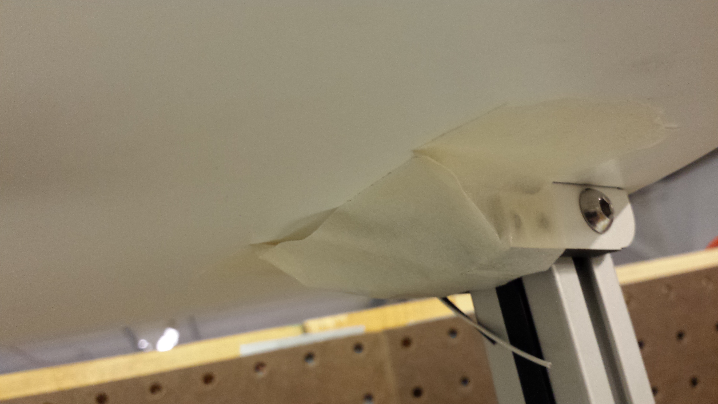
USER_MANUAL/images/end-stop-tape.jpg
