seemecnc/Orion_Delta/USER_MANUAL/images/extr-temp.jpg

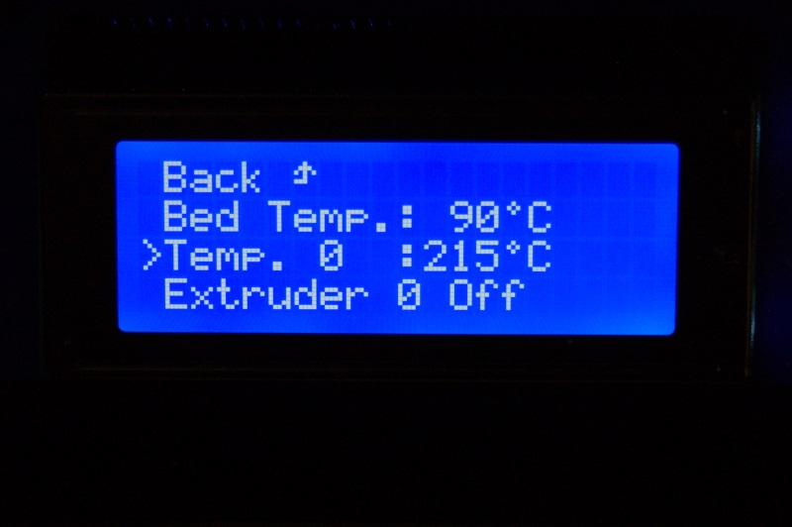
USER_MANUAL/images/extr-temp.jpg
