seemecnc/Orion_Delta/USER_MANUAL/images/extruder-panel.png

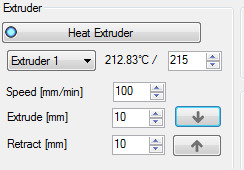
USER_MANUAL/images/extruder-panel.png
