seemecnc/Orion_Delta/USER_MANUAL/images/filament-hang.jpg

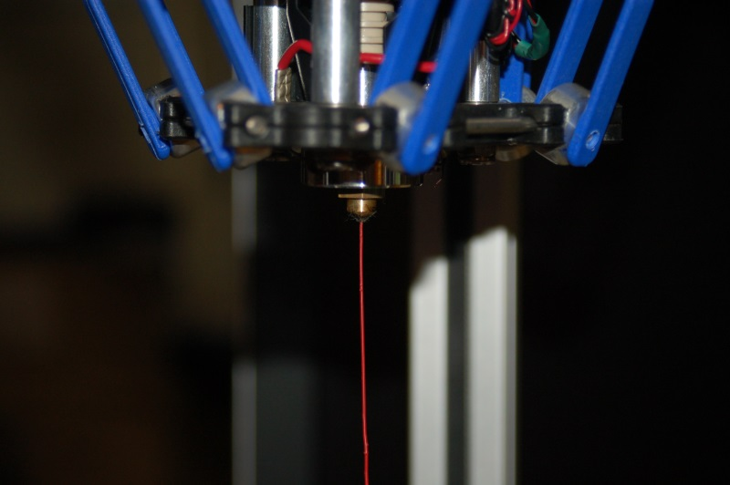
USER_MANUAL/images/filament-hang.jpg
