seemecnc/Orion_Delta/USER_MANUAL/images/five-ignites.png

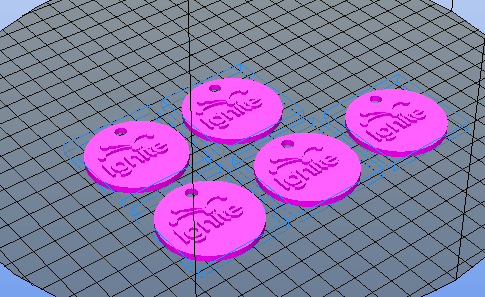
USER_MANUAL/images/five-ignites.png
