seemecnc/Orion_Delta/USER_MANUAL/images/g-code-editor.png

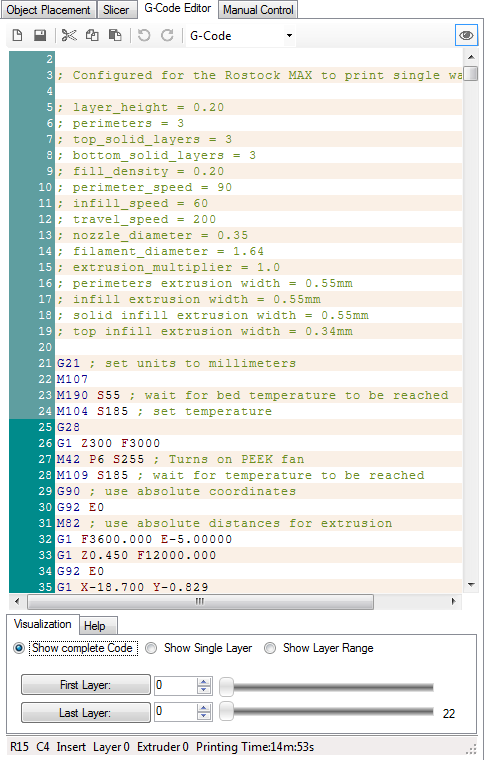
USER_MANUAL/images/g-code-editor.png
