seemecnc/Orion_Delta/USER_MANUAL/images/g-code-panel.png

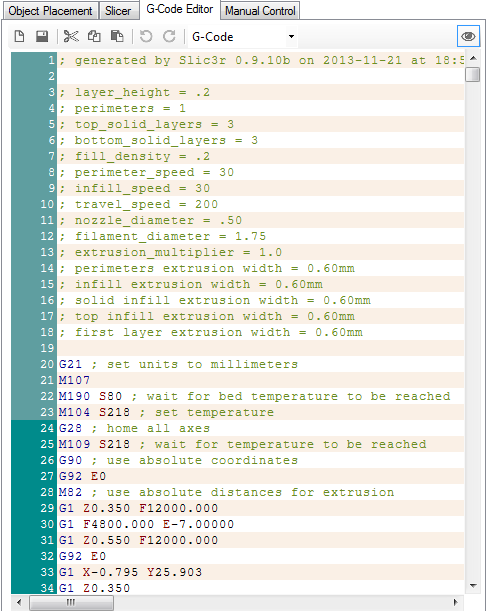
USER_MANUAL/images/g-code-panel.png
