seemecnc/Orion_Delta/USER_MANUAL/images/gcode-dir.jpg

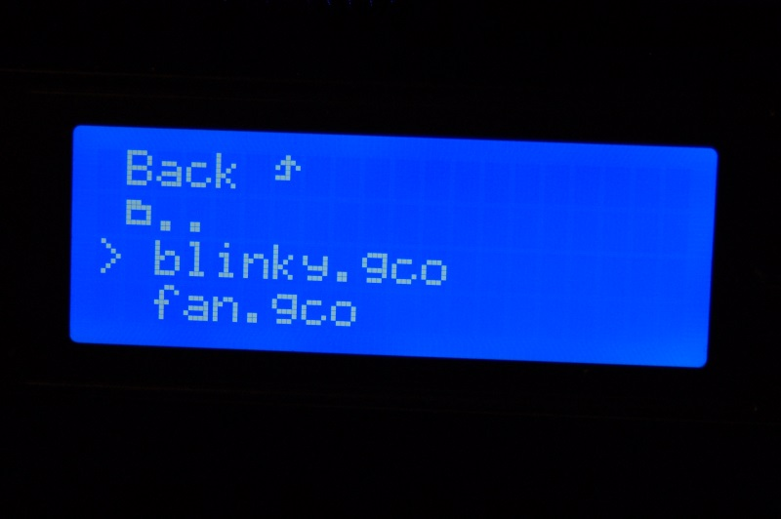
USER_MANUAL/images/gcode-dir.jpg
