seemecnc/Orion_Delta/USER_MANUAL/images/gcode-directory.jpg

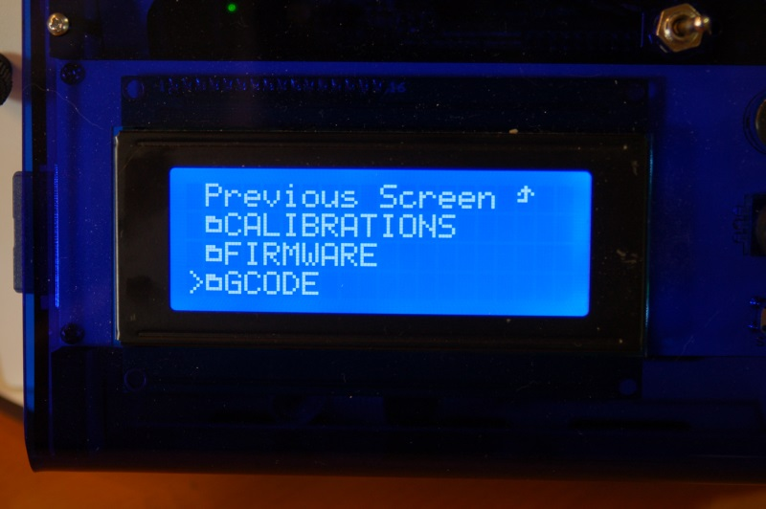
USER_MANUAL/images/gcode-directory.jpg
