seemecnc/Orion_Delta/USER_MANUAL/images/gcode-files.jpg

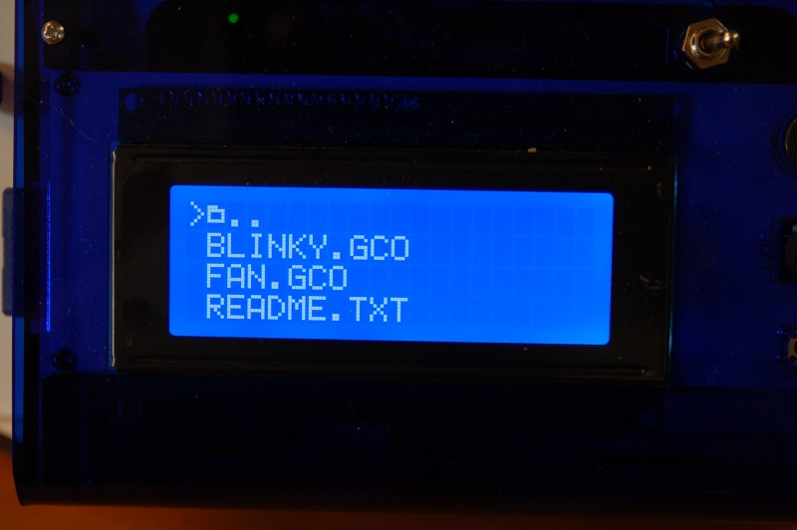
USER_MANUAL/images/gcode-files.jpg
