seemecnc/Orion_Delta/USER_MANUAL/images/heating-up.jpg

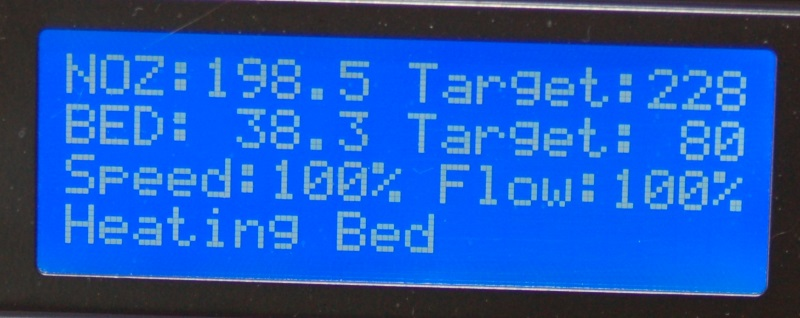
USER_MANUAL/images/heating-up.jpg
