seemecnc/Orion_Delta/USER_MANUAL/images/help-info.png

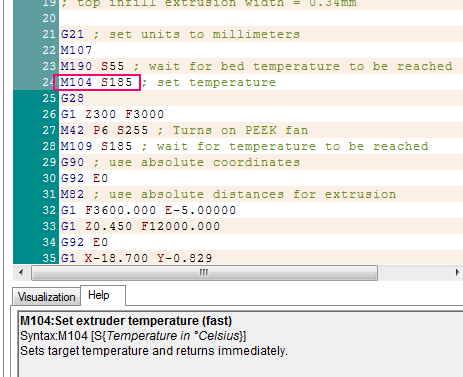
USER_MANUAL/images/help-info.png
