seemecnc/Orion_Delta/USER_MANUAL/images/home-all-sel2.jpg

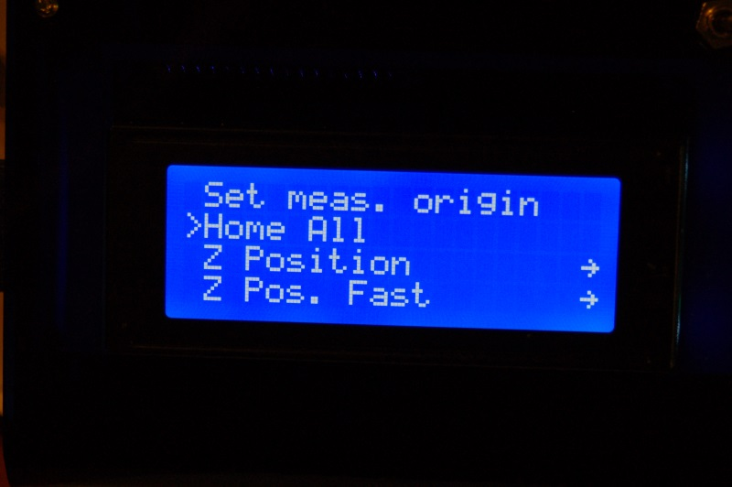
USER_MANUAL/images/home-all-sel2.jpg
