seemecnc/Orion_Delta/USER_MANUAL/images/home-all-selected.jpg

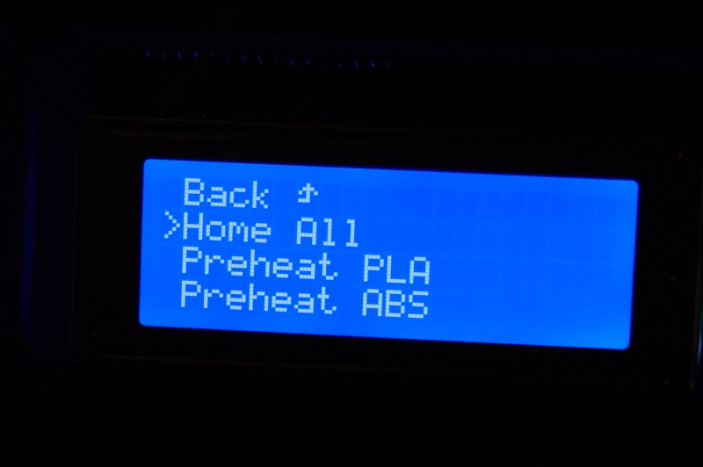
USER_MANUAL/images/home-all-selected.jpg
