seemecnc/Orion_Delta/USER_MANUAL/images/home-screen.jpg

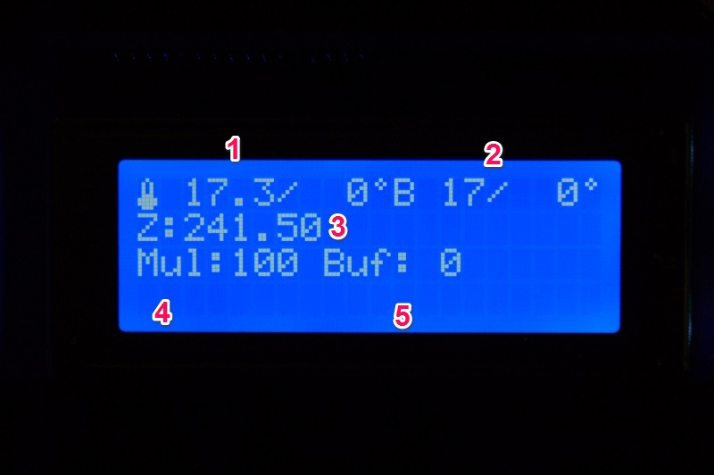
USER_MANUAL/images/home-screen.jpg
