seemecnc/Orion_Delta/USER_MANUAL/images/home-towers.jpg

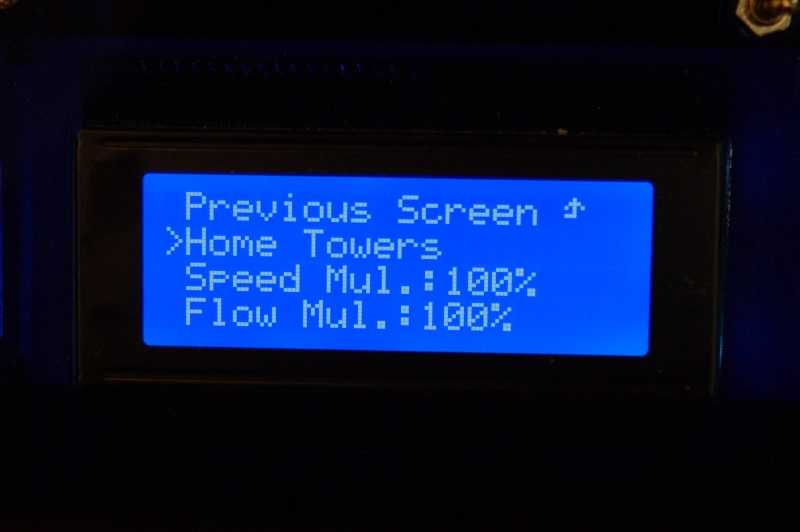
USER_MANUAL/images/home-towers.jpg
