seemecnc/Orion_Delta/USER_MANUAL/images/ignite-placement.png

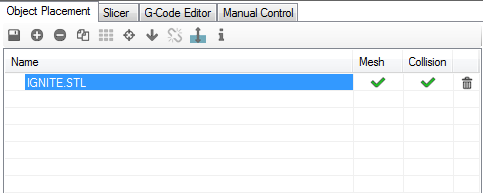
USER_MANUAL/images/ignite-placement.png
