seemecnc/Orion_Delta/USER_MANUAL/images/IMAG0268.jpg

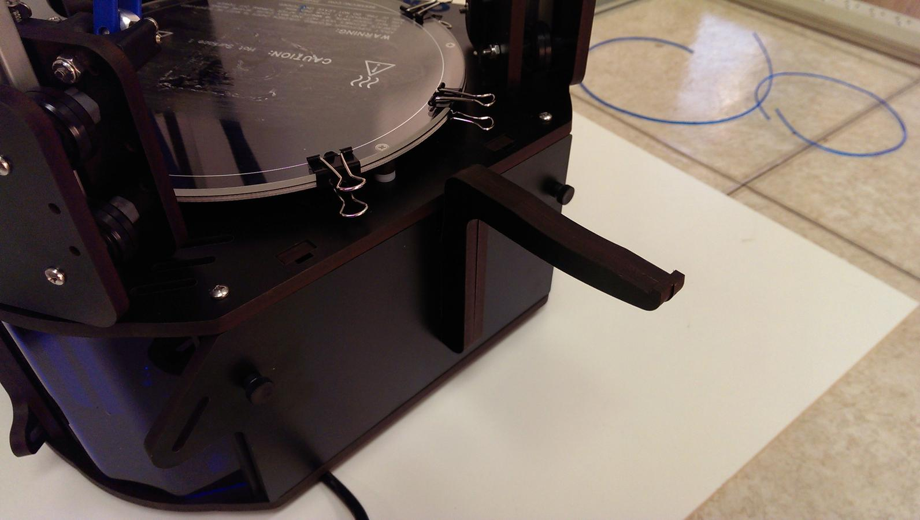
USER_MANUAL/images/IMAG0268.jpg
