seemecnc/Orion_Delta/USER_MANUAL/images/IMAG0270.jpg

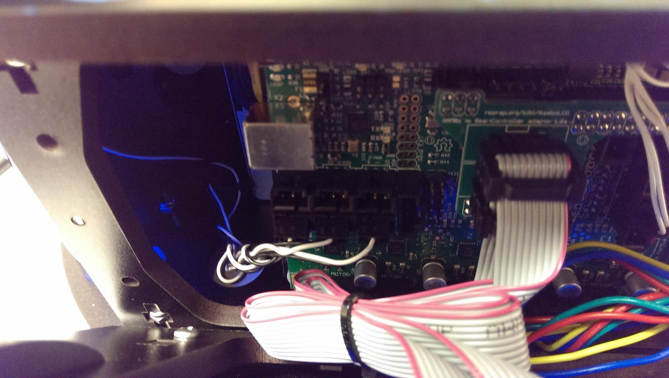
USER_MANUAL/images/IMAG0270.jpg
