seemecnc/Orion_Delta/USER_MANUAL/images/IMAG0271.jpg

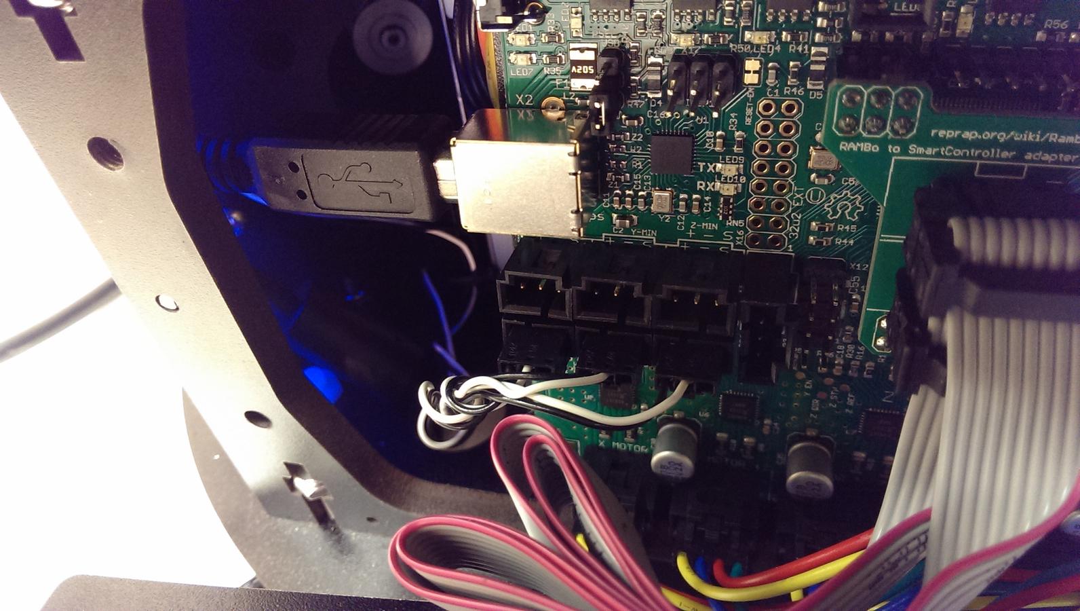
USER_MANUAL/images/IMAG0271.jpg
