seemecnc/Orion_Delta/USER_MANUAL/images/infill-example.jpg

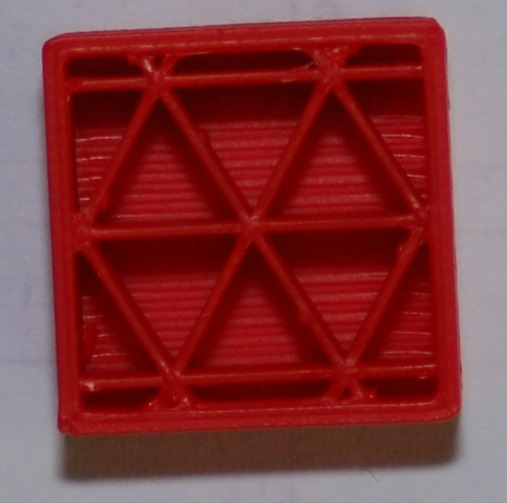
USER_MANUAL/images/infill-example.jpg
