seemecnc/Orion_Delta/USER_MANUAL/images/layer-height-examples.jpg

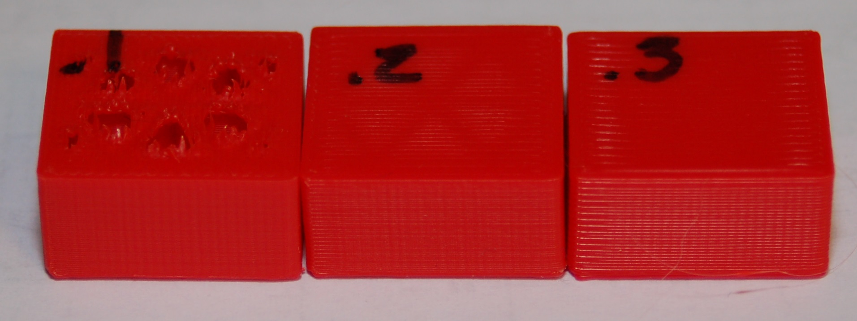
USER_MANUAL/images/layer-height-examples.jpg
