seemecnc/Orion_Delta/USER_MANUAL/images/lcd cable detail.jpg

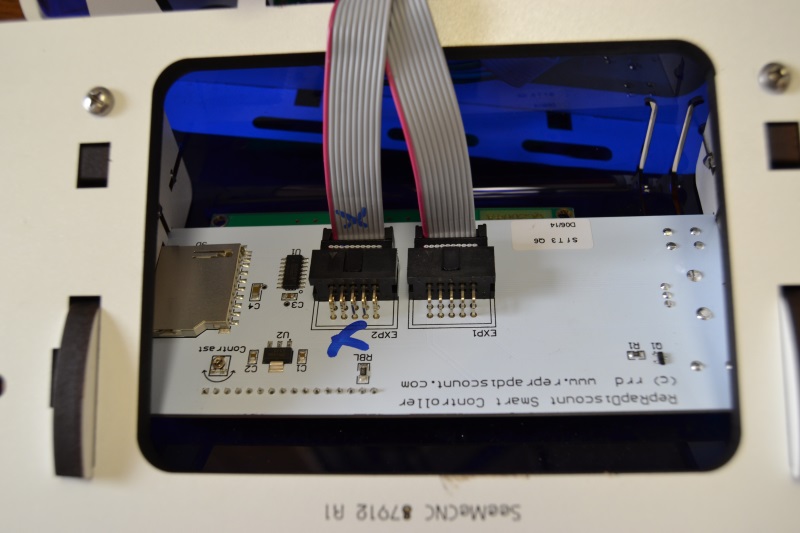
USER_MANUAL/images/lcd cable detail.jpg
