seemecnc/Orion_Delta/USER_MANUAL/images/lcd cable install.jpg

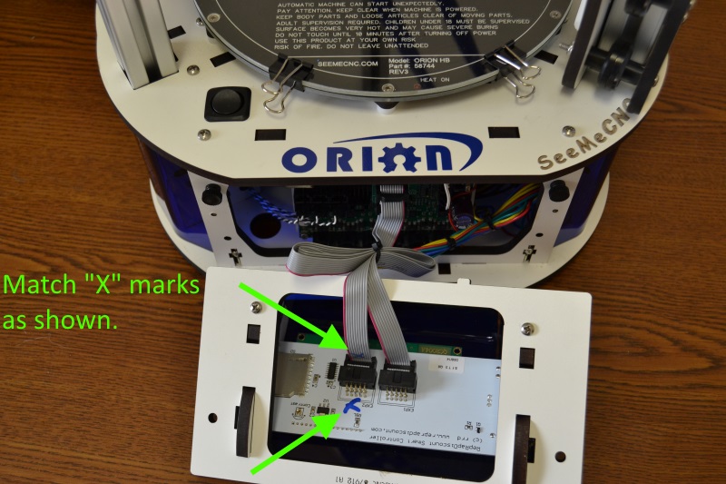
USER_MANUAL/images/lcd cable install.jpg
