seemecnc/Orion_Delta/USER_MANUAL/images/lcd cables.jpg

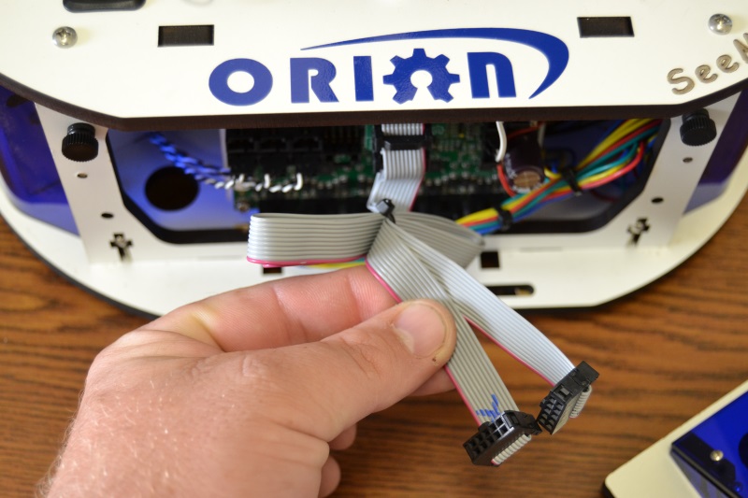
USER_MANUAL/images/lcd cables.jpg
