seemecnc/Orion_Delta/USER_MANUAL/images/lcd-menu.jpg

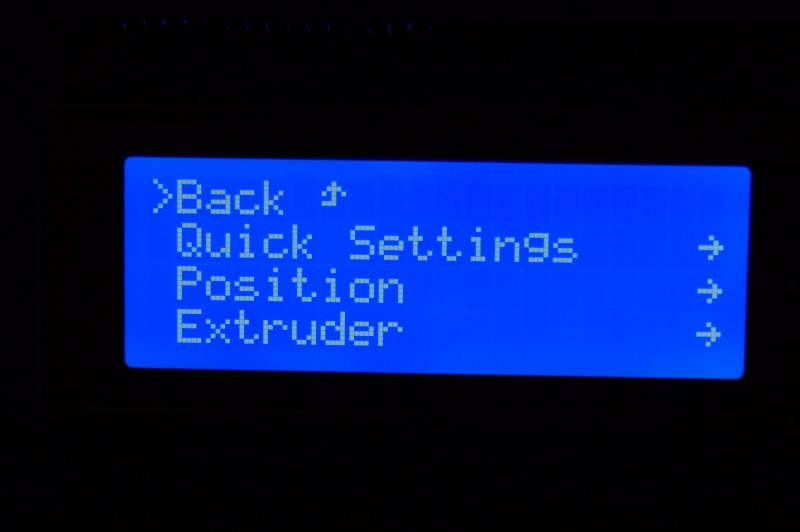
USER_MANUAL/images/lcd-menu.jpg
