seemecnc/Orion_Delta/USER_MANUAL/images/little red cube.jpg

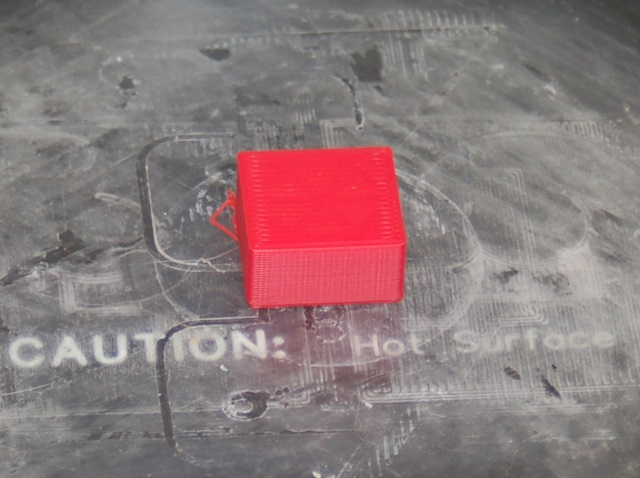
USER_MANUAL/images/little red cube.jpg
