seemecnc/Orion_Delta/USER_MANUAL/images/manual-panel-1.png

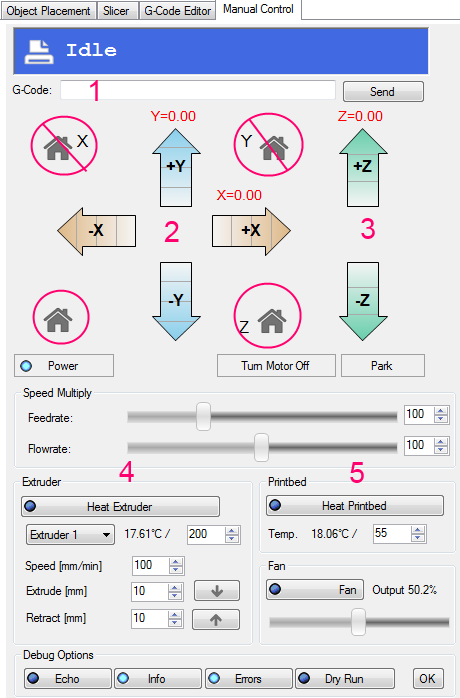
USER_MANUAL/images/manual-panel-1.png
