seemecnc/Orion_Delta/USER_MANUAL/images/mc21.jpg

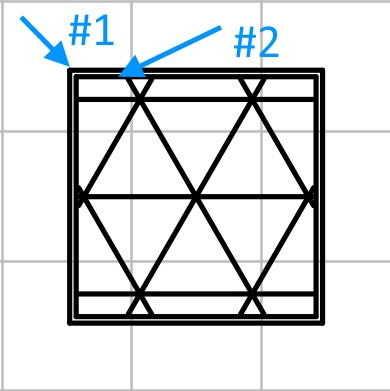
USER_MANUAL/images/mc21.jpg
