seemecnc/Orion_Delta/USER_MANUAL/images/mc-1.jpg

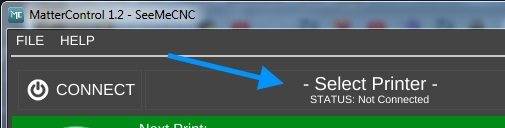
USER_MANUAL/images/mc-1.jpg
