seemecnc/Orion_Delta/USER_MANUAL/images/mc-2.jpg

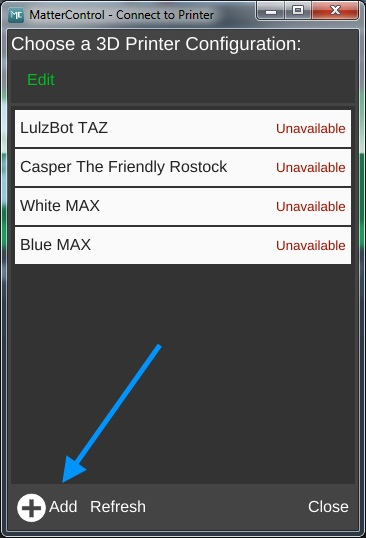
USER_MANUAL/images/mc-2.jpg
