seemecnc/Orion_Delta/USER_MANUAL/images/mc-3.jpg

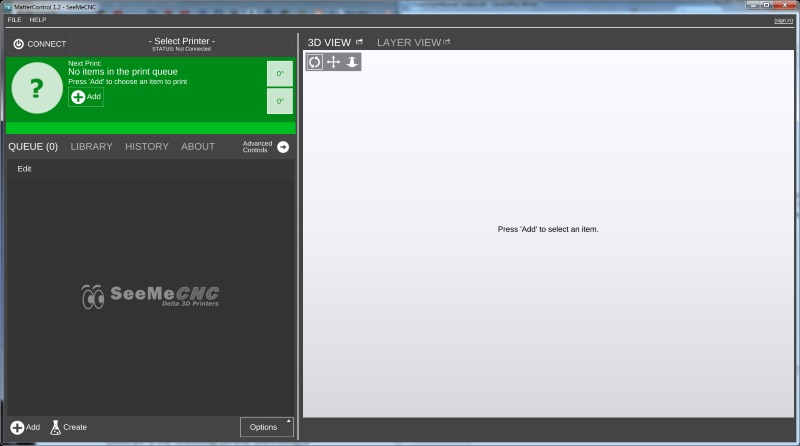
USER_MANUAL/images/mc-3.jpg
