seemecnc/Orion_Delta/USER_MANUAL/images/mc-4.jpg

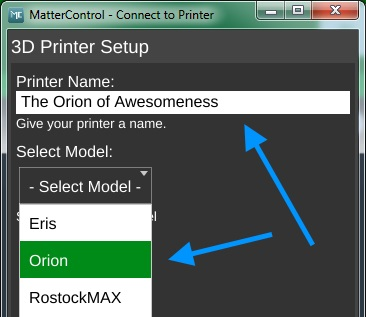
USER_MANUAL/images/mc-4.jpg
