seemecnc/Orion_Delta/USER_MANUAL/images/mc-5.jpg

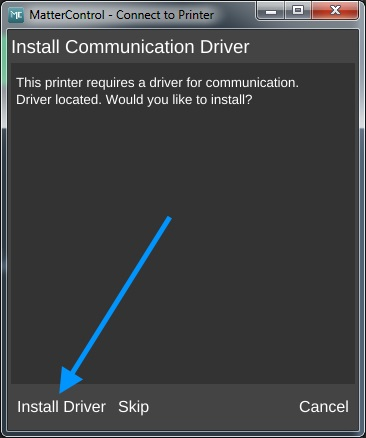
USER_MANUAL/images/mc-5.jpg
