seemecnc/Orion_Delta/USER_MANUAL/images/mc-6.jpg

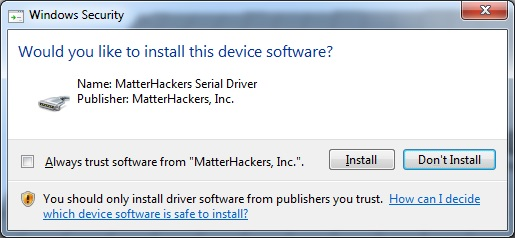
USER_MANUAL/images/mc-6.jpg
