seemecnc/Orion_Delta/USER_MANUAL/images/mc-7.jpg

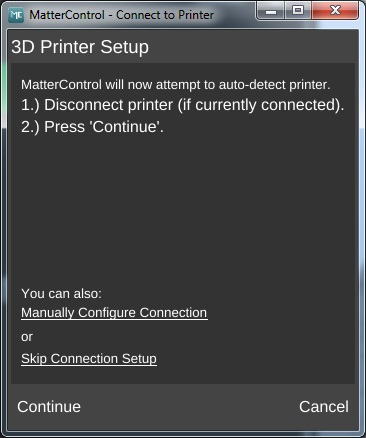
USER_MANUAL/images/mc-7.jpg
