seemecnc/Orion_Delta/USER_MANUAL/images/mc-9.jpg

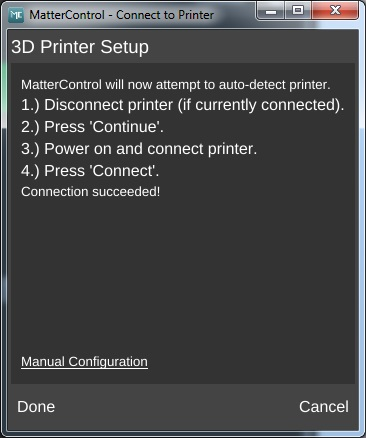
USER_MANUAL/images/mc-9.jpg
