seemecnc/Orion_Delta/USER_MANUAL/images/mc-10.jpg

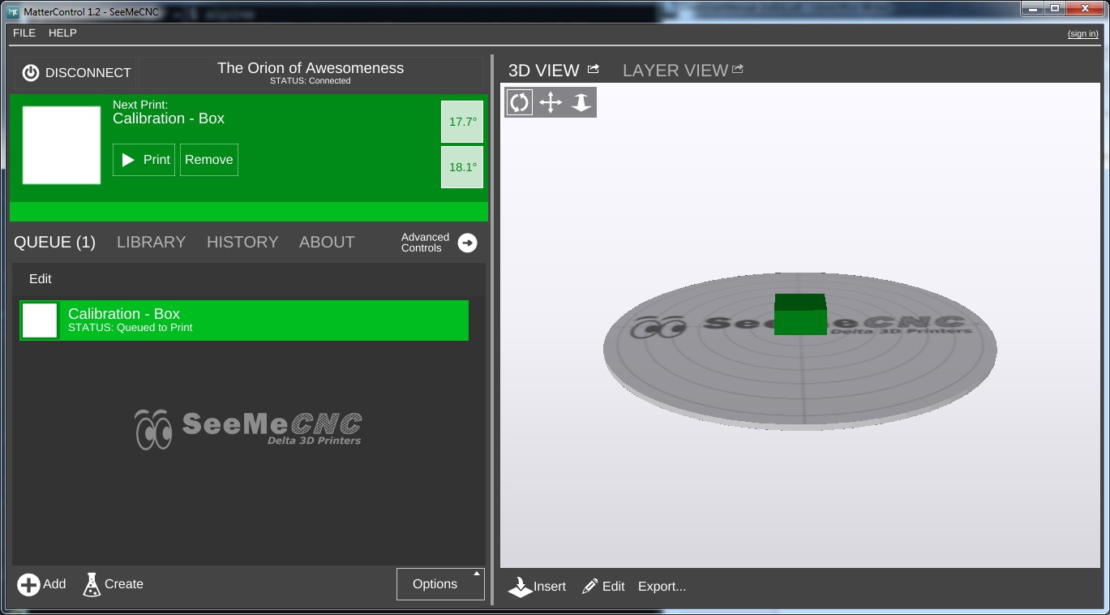
USER_MANUAL/images/mc-10.jpg
