seemecnc/Orion_Delta/USER_MANUAL/images/mc-11.jpg

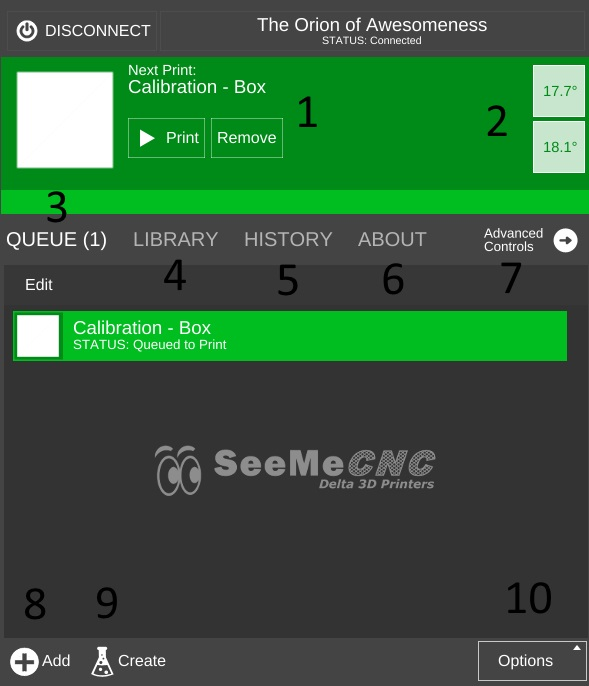
USER_MANUAL/images/mc-11.jpg
