seemecnc/Orion_Delta/USER_MANUAL/images/mc-12.jpg

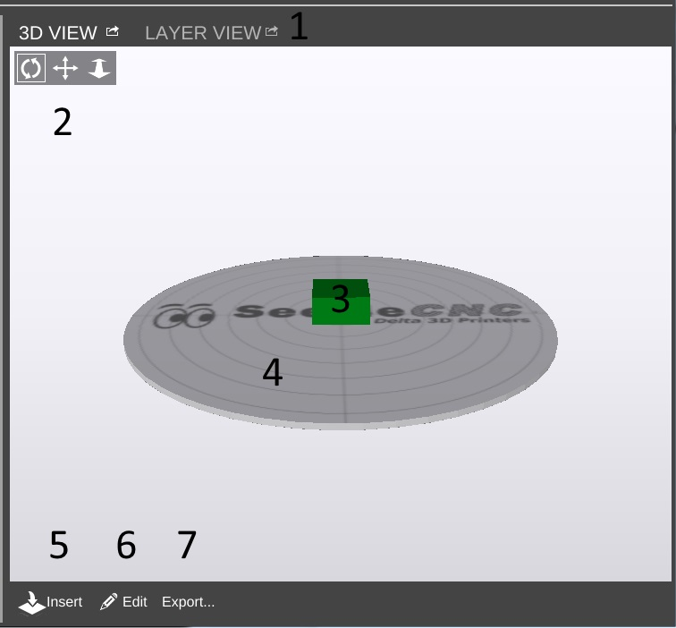
USER_MANUAL/images/mc-12.jpg
