seemecnc/Orion_Delta/USER_MANUAL/images/mc-13.jpg

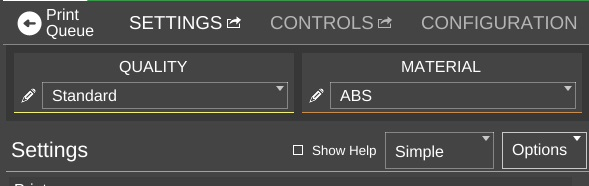
USER_MANUAL/images/mc-13.jpg
