seemecnc/Orion_Delta/USER_MANUAL/images/mc-14.jpg

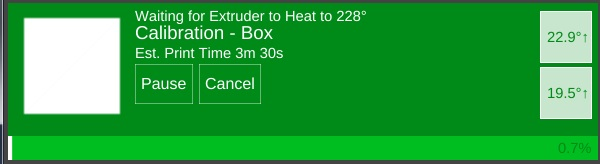
USER_MANUAL/images/mc-14.jpg
