seemecnc/Orion_Delta/USER_MANUAL/images/mc-15.jpg

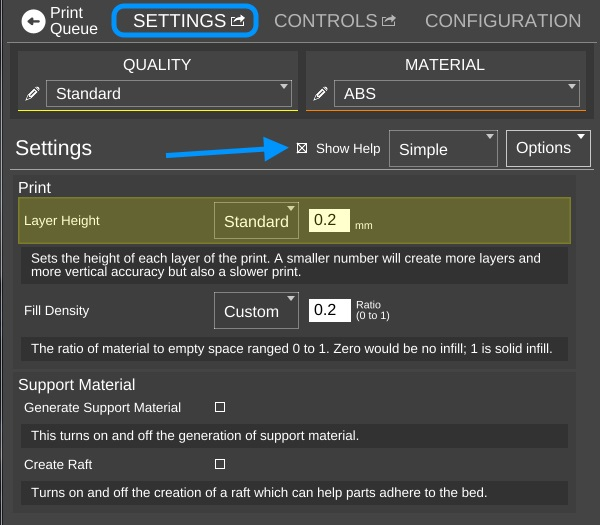
USER_MANUAL/images/mc-15.jpg
