seemecnc/Orion_Delta/USER_MANUAL/images/mc-16.jpg

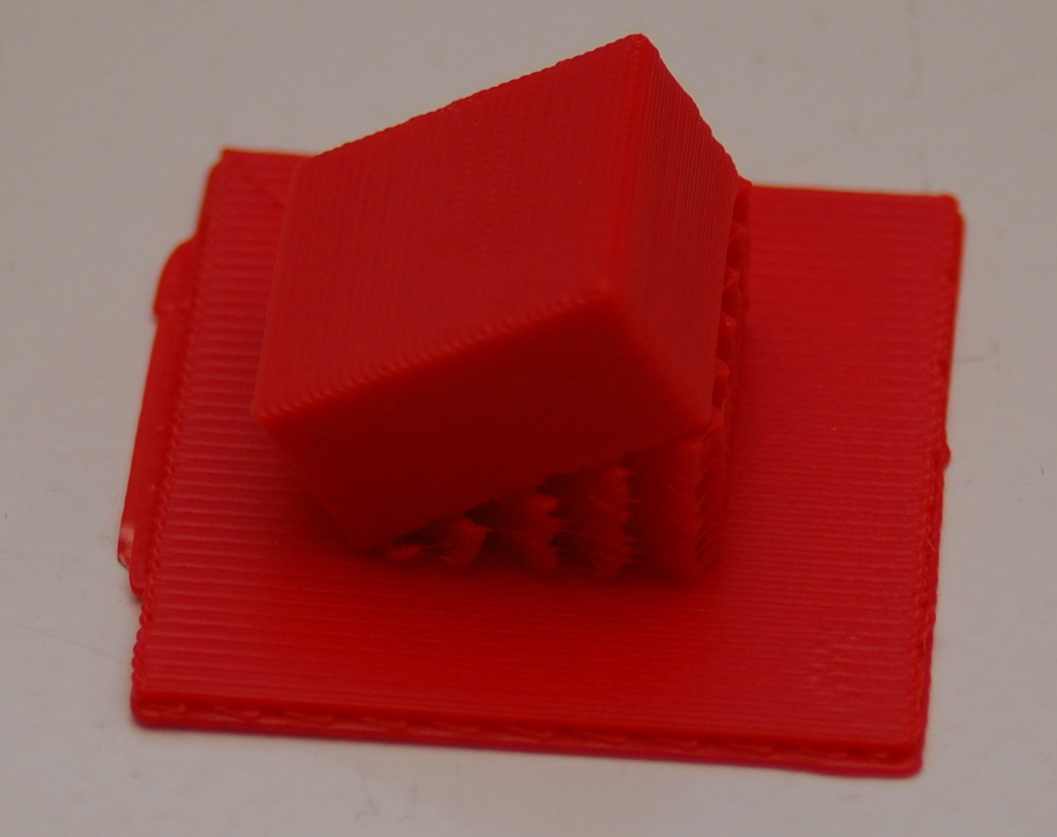
USER_MANUAL/images/mc-16.jpg
