seemecnc/Orion_Delta/USER_MANUAL/images/mc-17.jpg

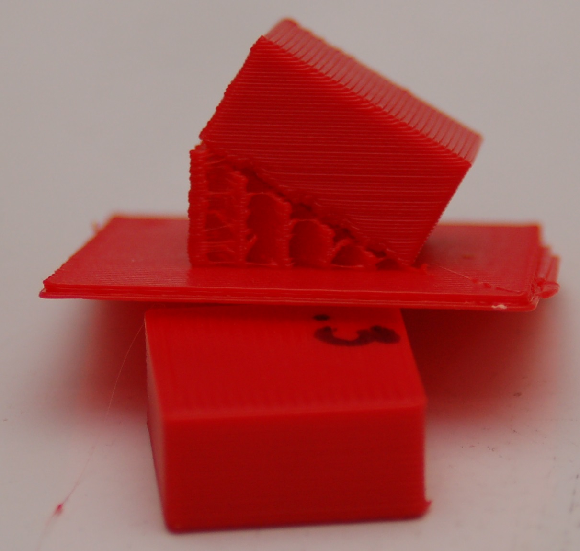
USER_MANUAL/images/mc-17.jpg
