seemecnc/Orion_Delta/USER_MANUAL/images/mc-18.jpg

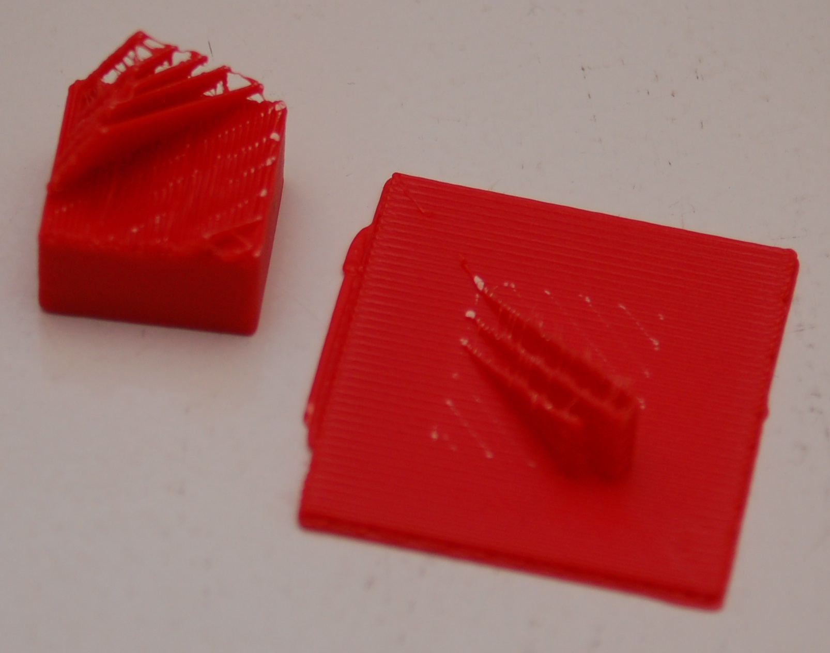
USER_MANUAL/images/mc-18.jpg
