seemecnc/Orion_Delta/USER_MANUAL/images/mc-19.jpg

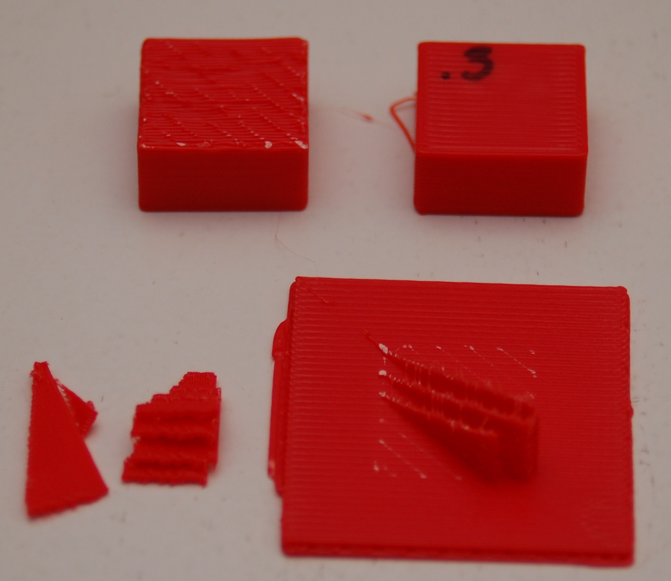
USER_MANUAL/images/mc-19.jpg
