seemecnc/Orion_Delta/USER_MANUAL/images/mc-20.jpg

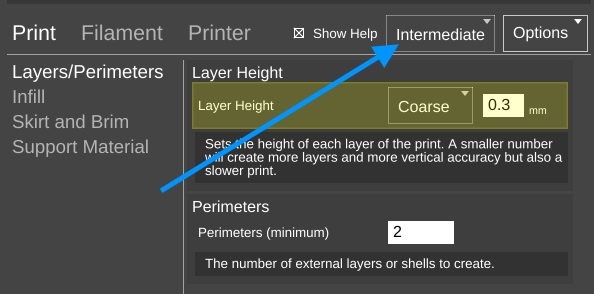
USER_MANUAL/images/mc-20.jpg
