seemecnc/Orion_Delta/USER_MANUAL/images/mc-21.jpg

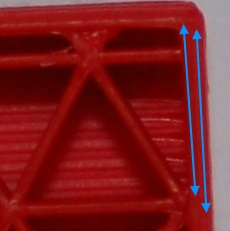
USER_MANUAL/images/mc-21.jpg
