seemecnc/Orion_Delta/USER_MANUAL/images/mc-22.jpg

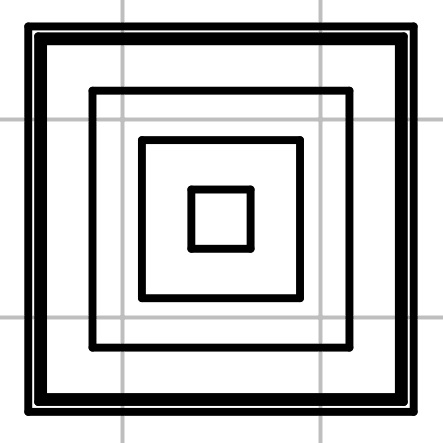
USER_MANUAL/images/mc-22.jpg
