seemecnc/Orion_Delta/USER_MANUAL/images/mc-23.jpg

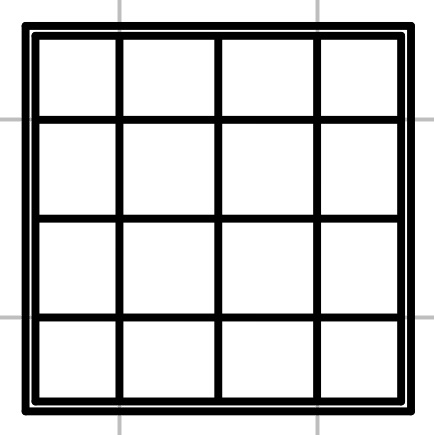
USER_MANUAL/images/mc-23.jpg
