seemecnc/Orion_Delta/USER_MANUAL/images/mc-24.jpg

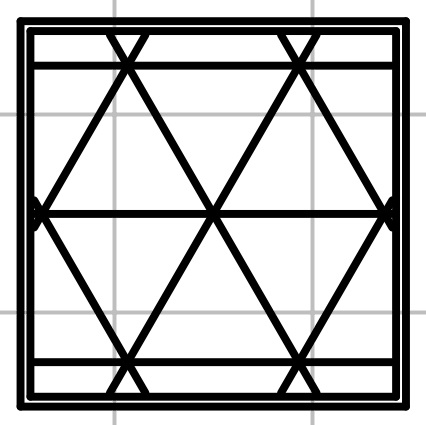
USER_MANUAL/images/mc-24.jpg
