seemecnc/Orion_Delta/USER_MANUAL/images/mc-25.jpg

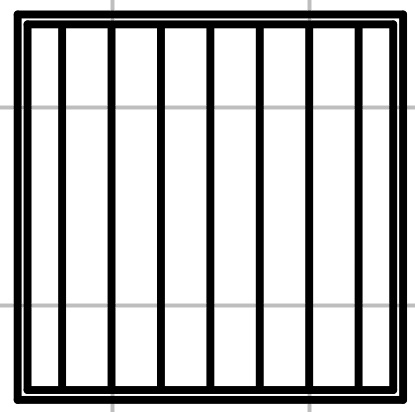
USER_MANUAL/images/mc-25.jpg
