seemecnc/Orion_Delta/USER_MANUAL/images/mc-26.jpg

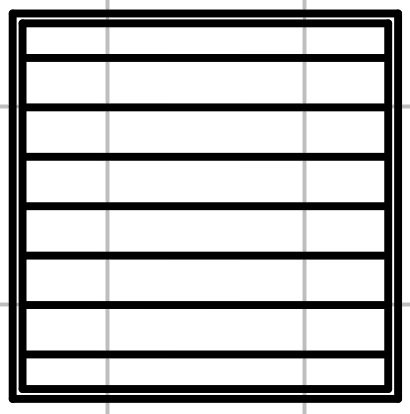
USER_MANUAL/images/mc-26.jpg
