seemecnc/Orion_Delta/USER_MANUAL/images/mc-27.jpg

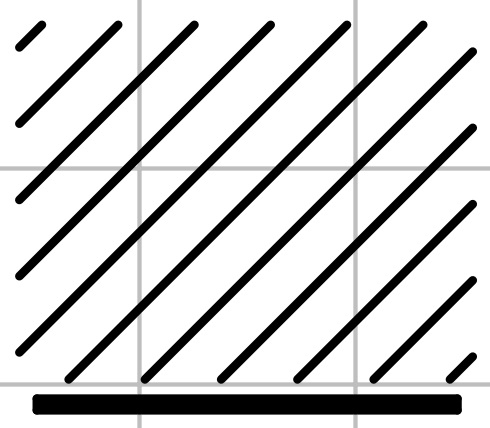
USER_MANUAL/images/mc-27.jpg
