seemecnc/Orion_Delta/USER_MANUAL/images/mc-28.jpg

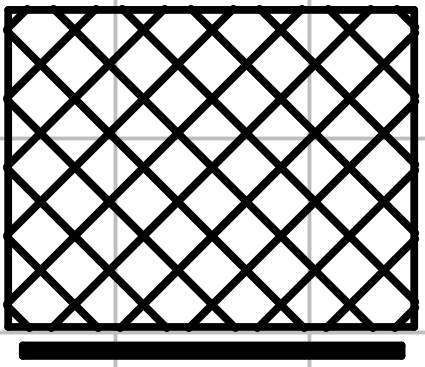
USER_MANUAL/images/mc-28.jpg
