seemecnc/Orion_Delta/USER_MANUAL/images/mc-30.jpg

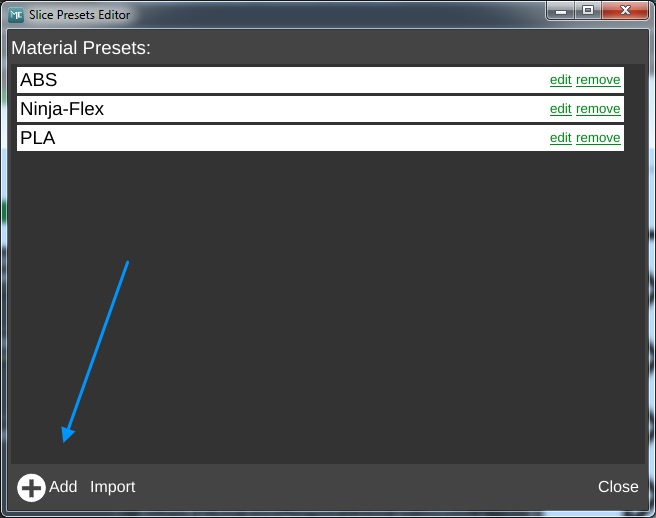
USER_MANUAL/images/mc-30.jpg
