seemecnc/Orion_Delta/USER_MANUAL/images/mc-31.jpg

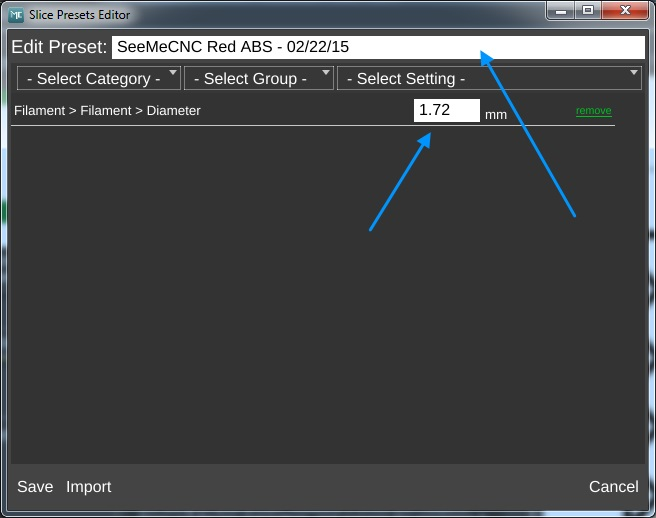
USER_MANUAL/images/mc-31.jpg
