seemecnc/Orion_Delta/USER_MANUAL/images/mc-32.jpg

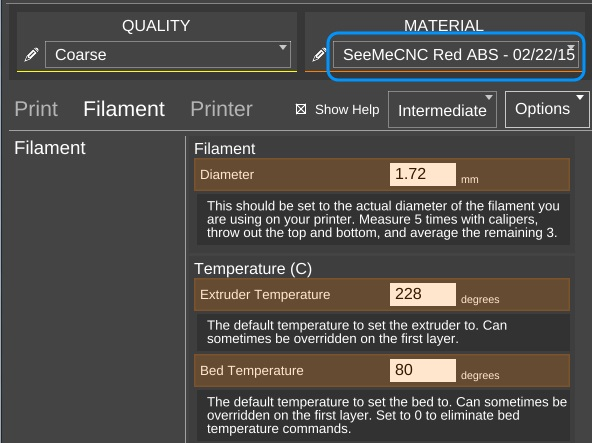
USER_MANUAL/images/mc-32.jpg
