seemecnc/Orion_Delta/USER_MANUAL/images/mc-34.jpg

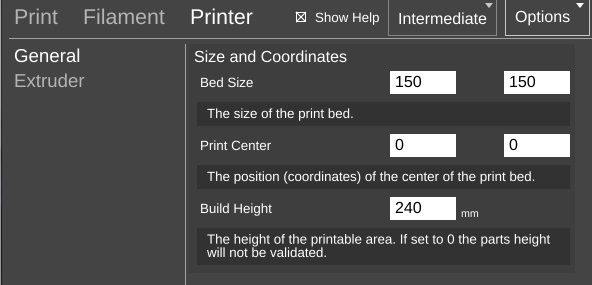
USER_MANUAL/images/mc-34.jpg
