seemecnc/Orion_Delta/USER_MANUAL/images/mc-36.jpg

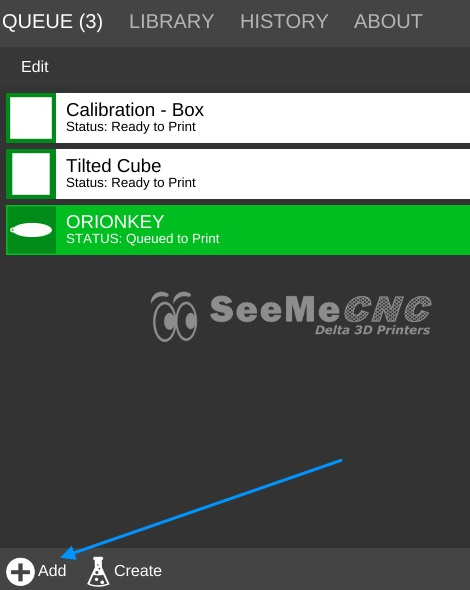
USER_MANUAL/images/mc-36.jpg
