seemecnc/Orion_Delta/USER_MANUAL/images/mc-37.jpg

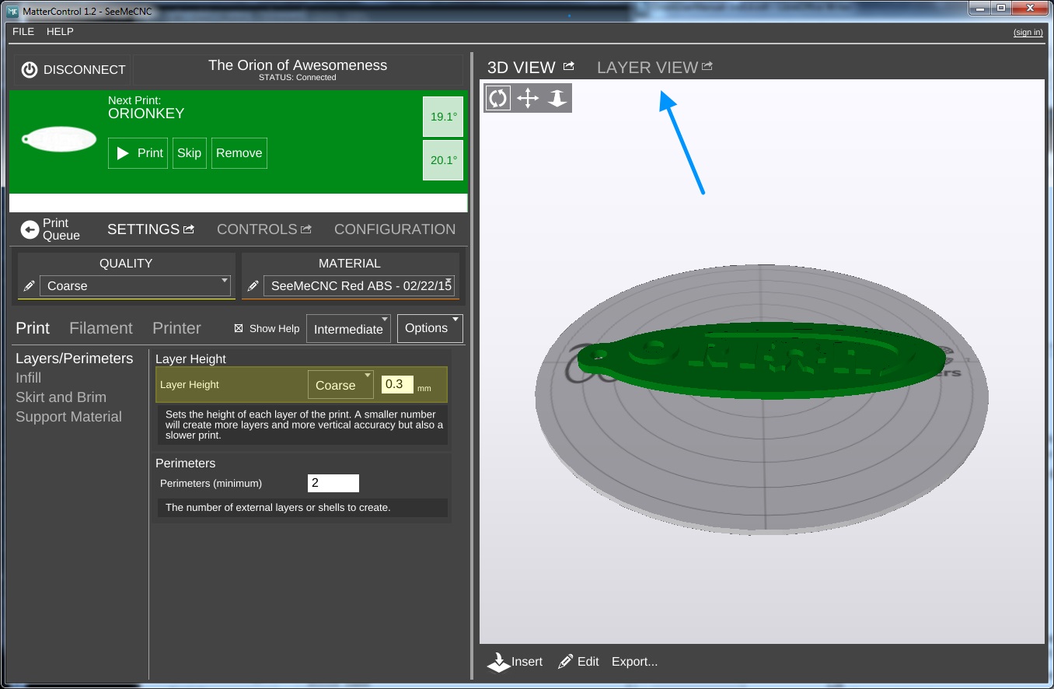
USER_MANUAL/images/mc-37.jpg
