seemecnc/Orion_Delta/USER_MANUAL/images/mc-38.jpg

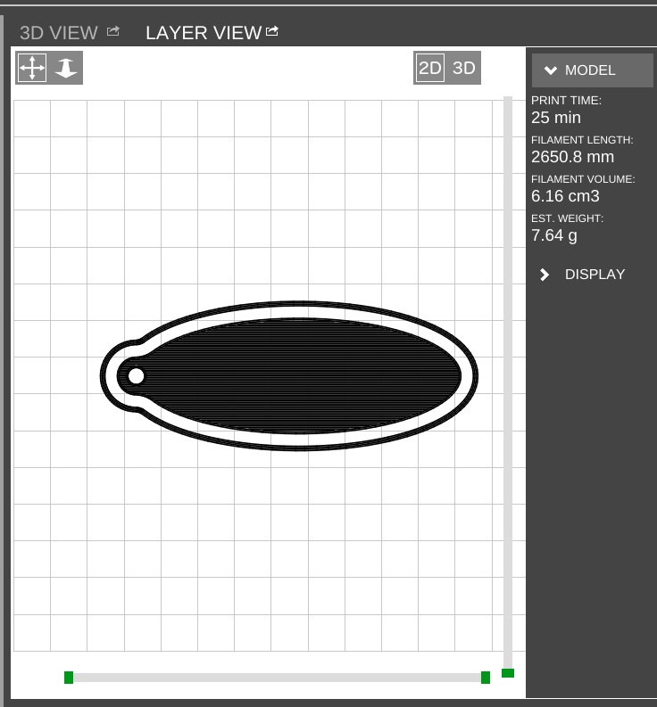
USER_MANUAL/images/mc-38.jpg
