seemecnc/Orion_Delta/USER_MANUAL/images/mc-40.jpg

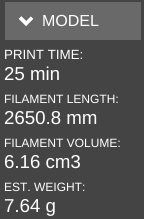
USER_MANUAL/images/mc-40.jpg
