seemecnc/Orion_Delta/USER_MANUAL/images/mc-41.jpg

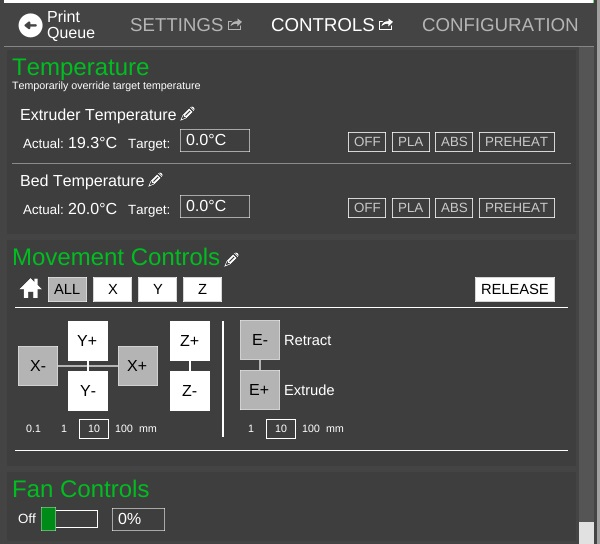
USER_MANUAL/images/mc-41.jpg
