seemecnc/Orion_Delta/USER_MANUAL/images/mc-42.jpg

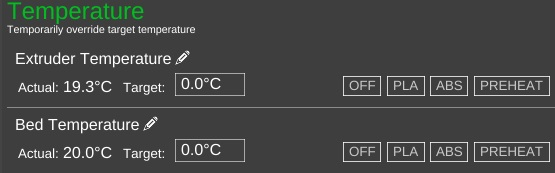
USER_MANUAL/images/mc-42.jpg
