seemecnc/Orion_Delta/USER_MANUAL/images/mc-43.jpg

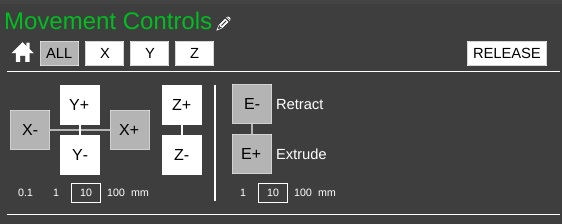
USER_MANUAL/images/mc-43.jpg
