seemecnc/Orion_Delta/USER_MANUAL/images/mc-45.jpg

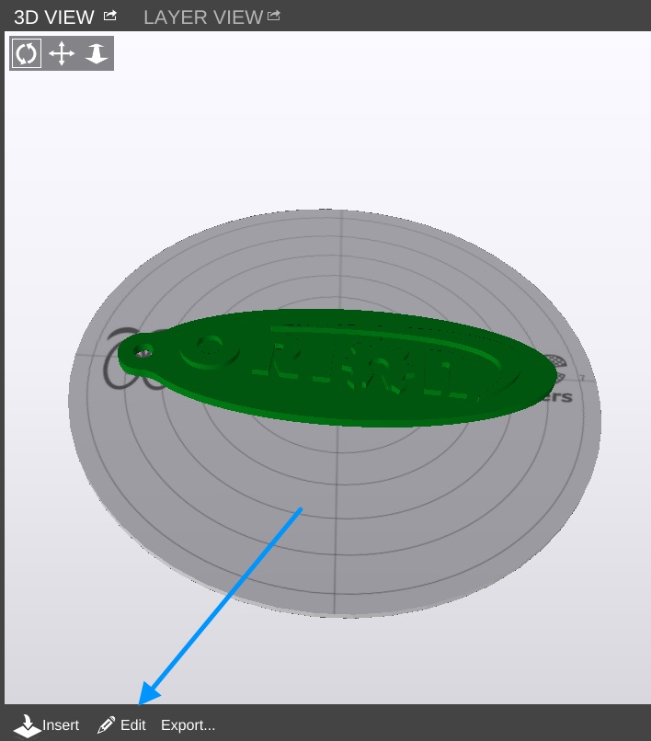
USER_MANUAL/images/mc-45.jpg
