seemecnc/Orion_Delta/USER_MANUAL/images/mc-46.jpg

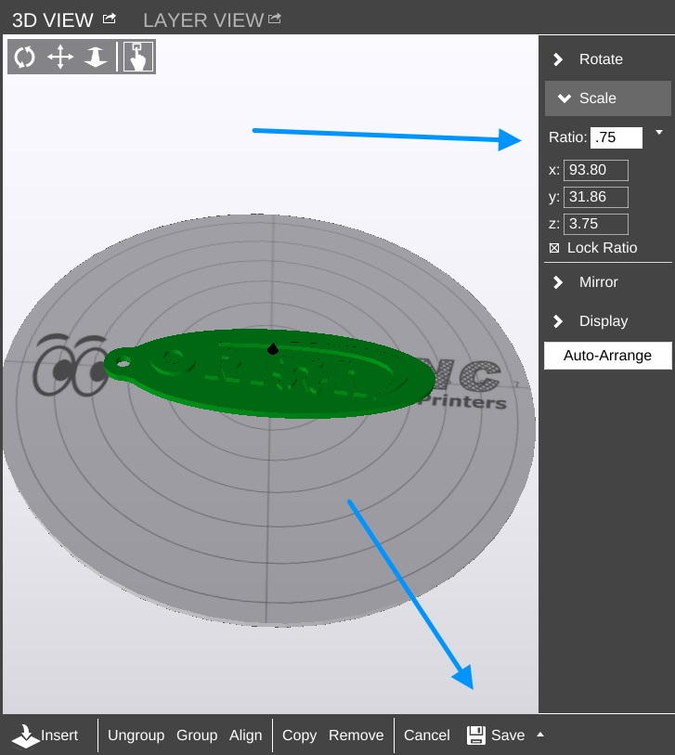
USER_MANUAL/images/mc-46.jpg
