seemecnc/Orion_Delta/USER_MANUAL/images/mc-47.jpg

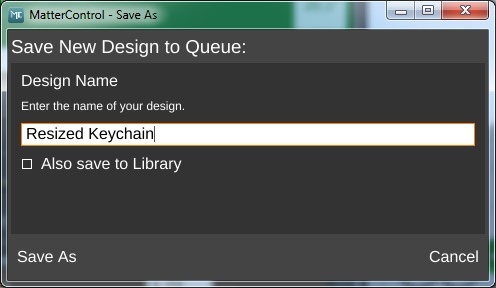
USER_MANUAL/images/mc-47.jpg
