seemecnc/Orion_Delta/USER_MANUAL/images/mc-49.jpg

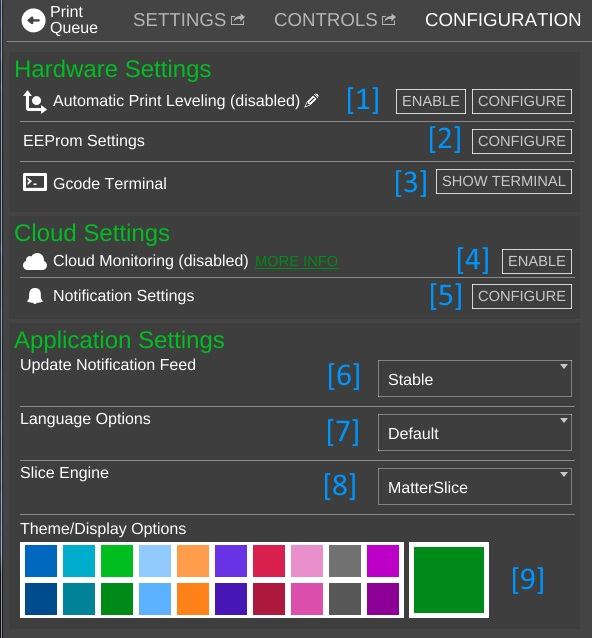
USER_MANUAL/images/mc-49.jpg
