seemecnc/Orion_Delta/USER_MANUAL/images/mc-52.jpg

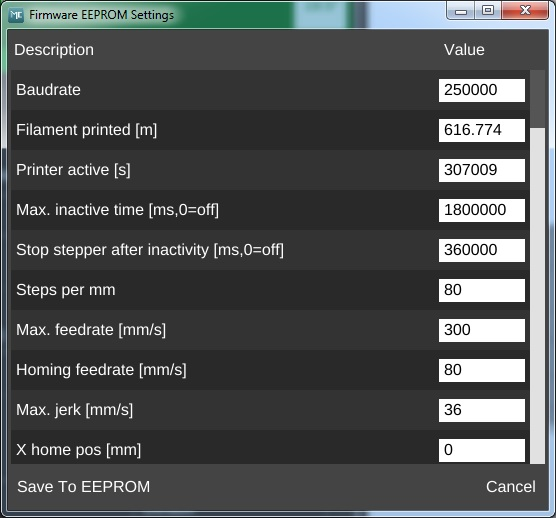
USER_MANUAL/images/mc-52.jpg
