seemecnc/Orion_Delta/USER_MANUAL/images/mc-54.jpg

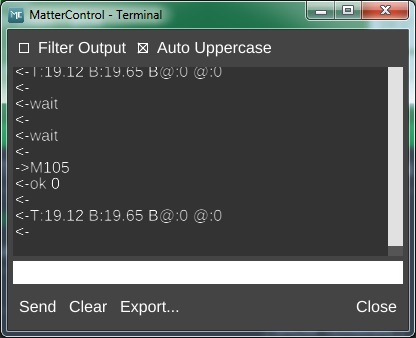
USER_MANUAL/images/mc-54.jpg
