seemecnc/Orion_Delta/USER_MANUAL/images/mc-57.jpg

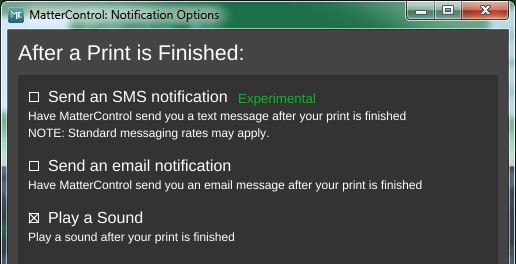
USER_MANUAL/images/mc-57.jpg
