seemecnc/Orion_Delta/USER_MANUAL/images/mc-62.jpg

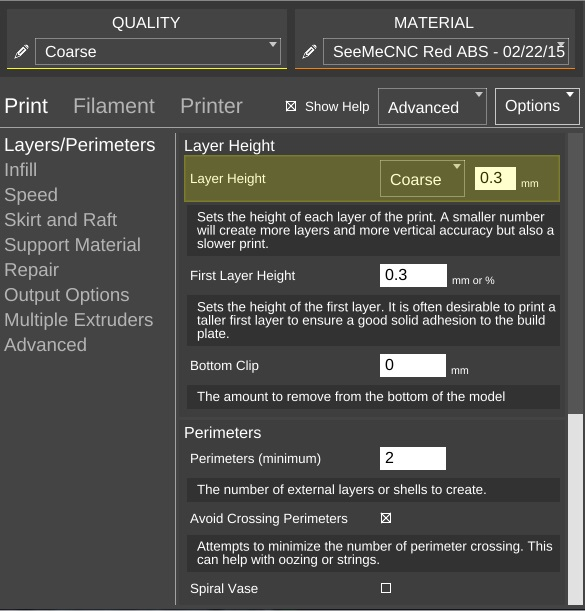
USER_MANUAL/images/mc-62.jpg
