seemecnc/Orion_Delta/USER_MANUAL/images/mc-72.jpg

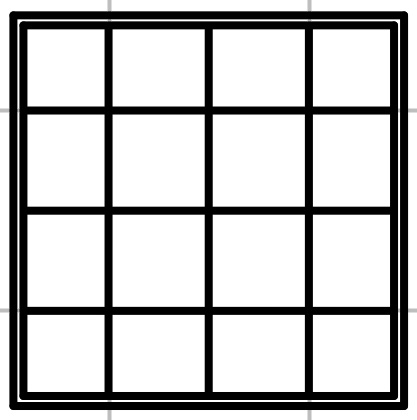
USER_MANUAL/images/mc-72.jpg
