seemecnc/Orion_Delta/USER_MANUAL/images/mc-73.jpg

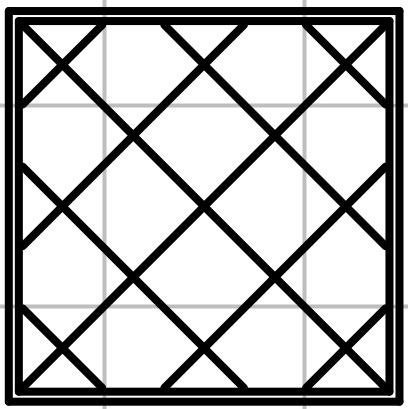
USER_MANUAL/images/mc-73.jpg
