seemecnc/Orion_Delta/USER_MANUAL/images/mc-74.jpg

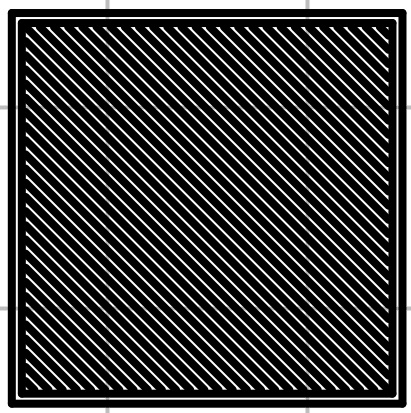
USER_MANUAL/images/mc-74.jpg
