seemecnc/Orion_Delta/USER_MANUAL/images/mc-79.jpg

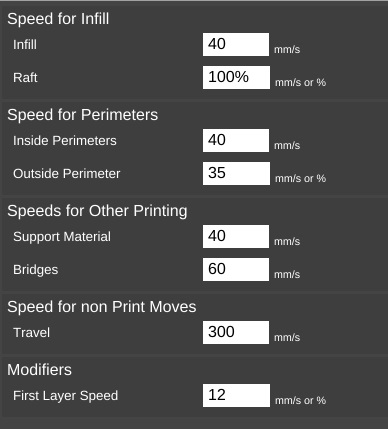
USER_MANUAL/images/mc-79.jpg
