seemecnc/Orion_Delta/USER_MANUAL/images/mc-80.jpg

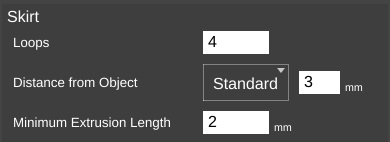
USER_MANUAL/images/mc-80.jpg
