seemecnc/Orion_Delta/USER_MANUAL/images/mc-81.jpg

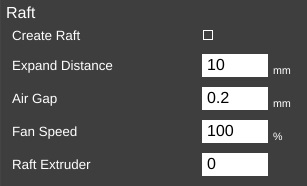
USER_MANUAL/images/mc-81.jpg
