seemecnc/Orion_Delta/USER_MANUAL/images/mc-82.jpg

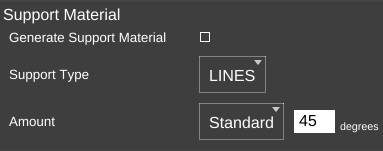
USER_MANUAL/images/mc-82.jpg
