seemecnc/Orion_Delta/USER_MANUAL/images/mc-83.jpg

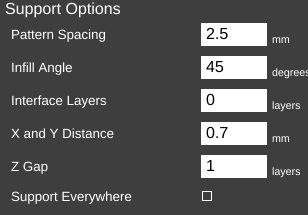
USER_MANUAL/images/mc-83.jpg
