seemecnc/Orion_Delta/USER_MANUAL/images/mc-92.jpg

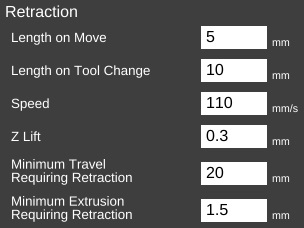
USER_MANUAL/images/mc-92.jpg
