seemecnc/Orion_Delta/USER_MANUAL/images/mc-94.jpg

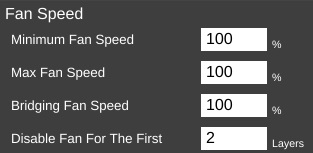
USER_MANUAL/images/mc-94.jpg
