seemecnc/Orion_Delta/USER_MANUAL/images/mc-96.jpg

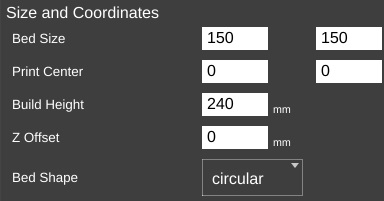
USER_MANUAL/images/mc-96.jpg
