seemecnc/Orion_Delta/USER_MANUAL/images/mc-97.jpg

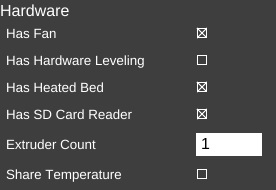
USER_MANUAL/images/mc-97.jpg
