seemecnc/Orion_Delta/USER_MANUAL/images/mc-99.jpg

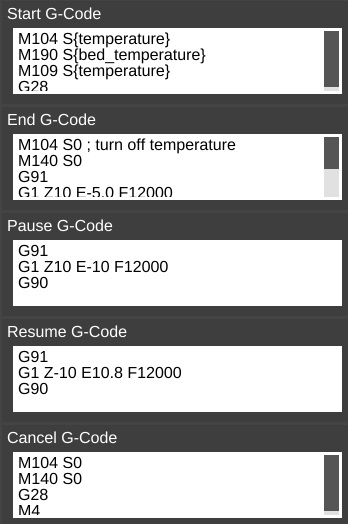
USER_MANUAL/images/mc-99.jpg
