seemecnc/Orion_Delta/USER_MANUAL/images/mc-102.jpg

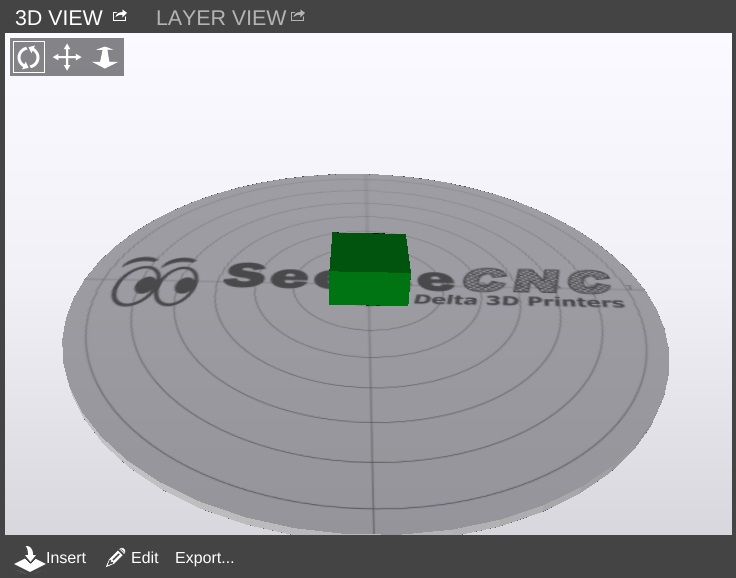
USER_MANUAL/images/mc-102.jpg
