seemecnc/Orion_Delta/USER_MANUAL/images/mc-105.jpg

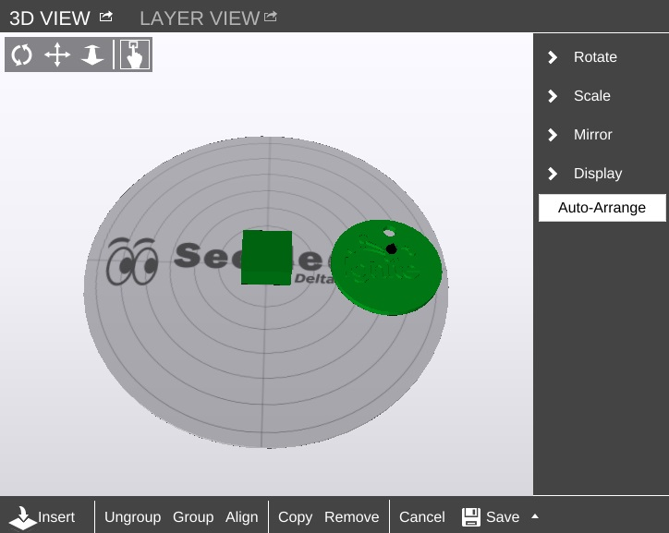
USER_MANUAL/images/mc-105.jpg
