seemecnc/Orion_Delta/USER_MANUAL/images/mc-106.jpg

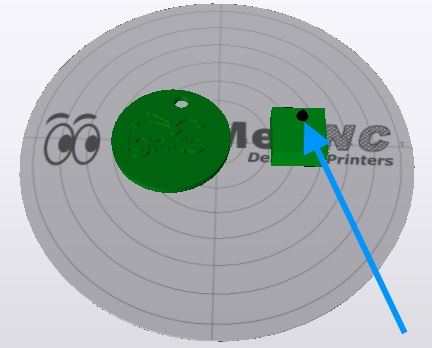
USER_MANUAL/images/mc-106.jpg
