seemecnc/Orion_Delta/USER_MANUAL/images/mc-108.jpg

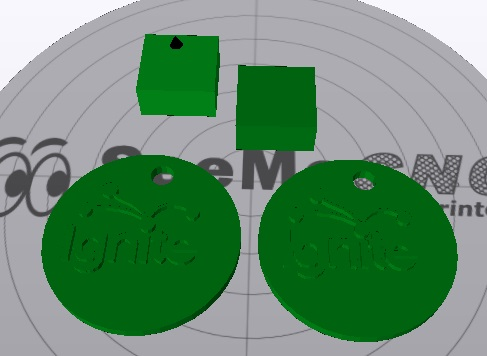
USER_MANUAL/images/mc-108.jpg
