seemecnc/Orion_Delta/USER_MANUAL/images/mc-109.jpg

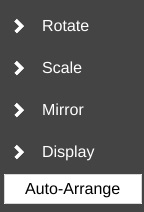
USER_MANUAL/images/mc-109.jpg
