seemecnc/Orion_Delta/USER_MANUAL/images/mc-110.jpg

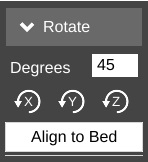
USER_MANUAL/images/mc-110.jpg
