seemecnc/Orion_Delta/USER_MANUAL/images/mc-111.jpg

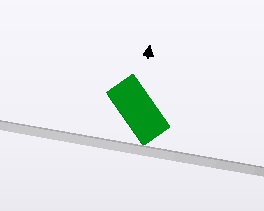
USER_MANUAL/images/mc-111.jpg
