seemecnc/Orion_Delta/USER_MANUAL/images/mc-112.jpg

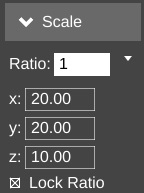
USER_MANUAL/images/mc-112.jpg
