seemecnc/Orion_Delta/USER_MANUAL/images/mc-114.jpg

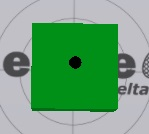
USER_MANUAL/images/mc-114.jpg
