seemecnc/Orion_Delta/USER_MANUAL/images/mc-116.jpg

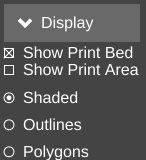
USER_MANUAL/images/mc-116.jpg
