seemecnc/Orion_Delta/USER_MANUAL/images/mc-117.jpg

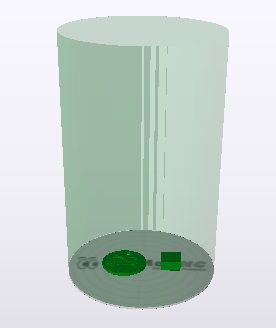
USER_MANUAL/images/mc-117.jpg
