seemecnc/Orion_Delta/USER_MANUAL/images/mc-118.jpg

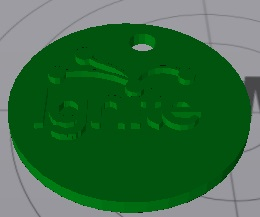
USER_MANUAL/images/mc-118.jpg
