seemecnc/Orion_Delta/USER_MANUAL/images/mc-119.jpg

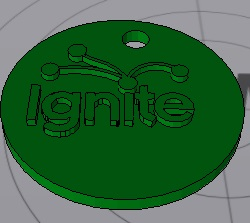
USER_MANUAL/images/mc-119.jpg
