seemecnc/Orion_Delta/USER_MANUAL/images/mc-120.jpg

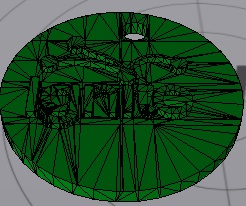
USER_MANUAL/images/mc-120.jpg
