seemecnc/Orion_Delta/USER_MANUAL/images/mc-121.jpg

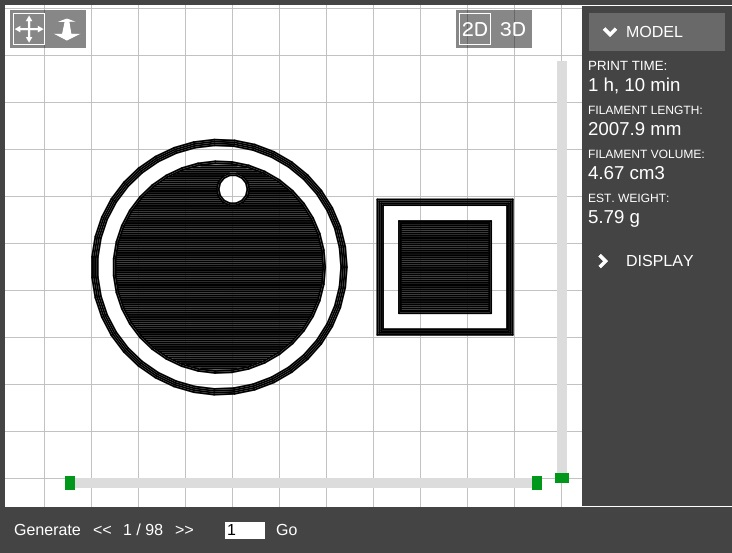
USER_MANUAL/images/mc-121.jpg
