seemecnc/Orion_Delta/USER_MANUAL/images/mc-122.jpg

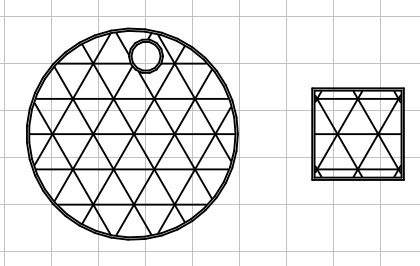
USER_MANUAL/images/mc-122.jpg
