seemecnc/Orion_Delta/USER_MANUAL/images/mc-123.jpg

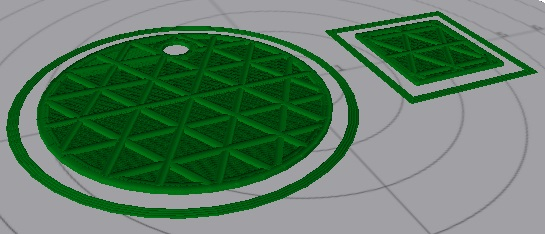
USER_MANUAL/images/mc-123.jpg
