seemecnc/Orion_Delta/USER_MANUAL/images/mc-124.jpg

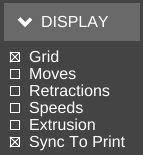
USER_MANUAL/images/mc-124.jpg
