seemecnc/Orion_Delta/USER_MANUAL/images/mc-125.jpg

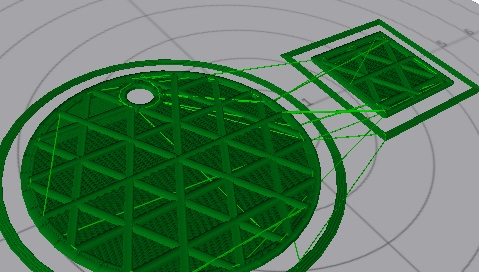
USER_MANUAL/images/mc-125.jpg
