seemecnc/Orion_Delta/USER_MANUAL/images/mc-126.jpg

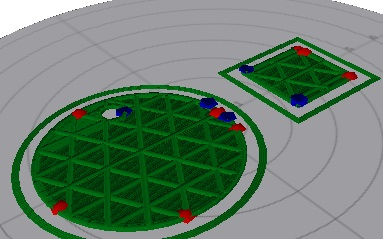
USER_MANUAL/images/mc-126.jpg
