seemecnc/Orion_Delta/USER_MANUAL/images/mc-127.jpg

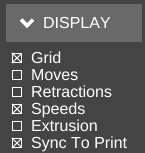
USER_MANUAL/images/mc-127.jpg
