seemecnc/Orion_Delta/USER_MANUAL/images/mc-128.jpg

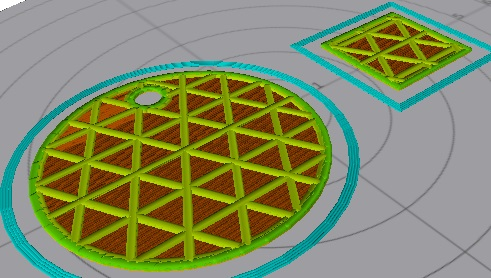
USER_MANUAL/images/mc-128.jpg
