seemecnc/Orion_Delta/USER_MANUAL/images/mc-129.jpg

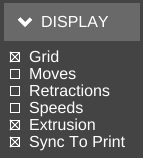
USER_MANUAL/images/mc-129.jpg
