seemecnc/Orion_Delta/USER_MANUAL/images/object-placement-panel.png

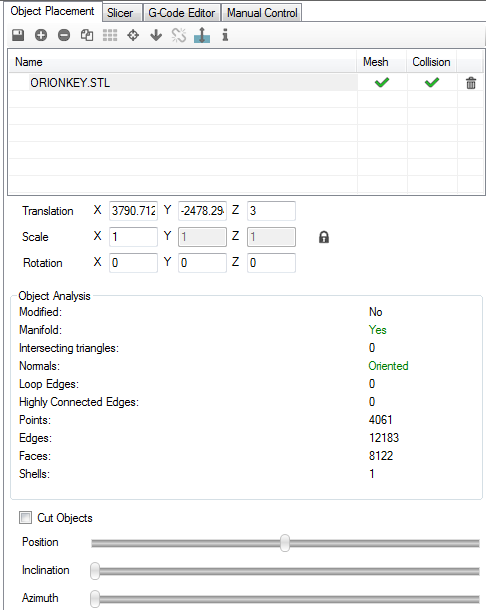
USER_MANUAL/images/object-placement-panel.png
