seemecnc/Orion_Delta/USER_MANUAL/images/on-printer-settings.jpg

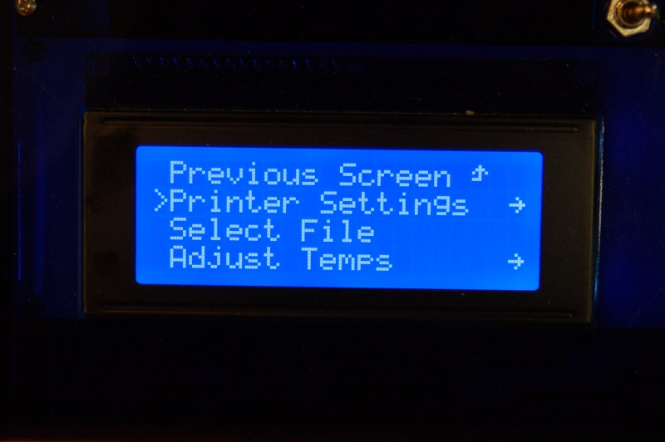
USER_MANUAL/images/on-printer-settings.jpg
