seemecnc/Orion_Delta/USER_MANUAL/images/oops2.jpg

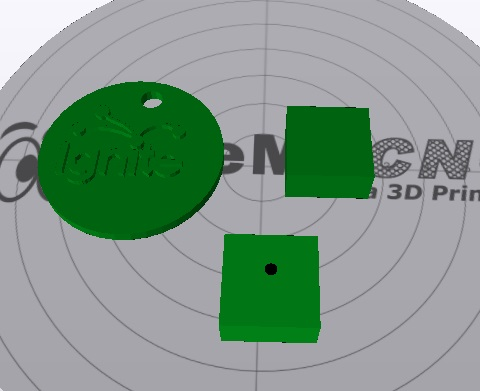
USER_MANUAL/images/oops2.jpg
