seemecnc/Orion_Delta/USER_MANUAL/images/oops3.jpg

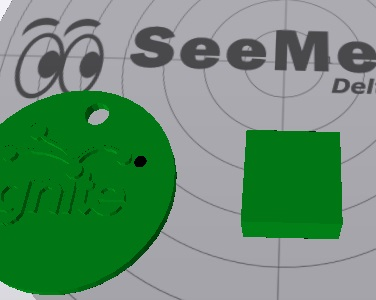
USER_MANUAL/images/oops3.jpg
