seemecnc/Orion_Delta/USER_MANUAL/images/oops.jpg

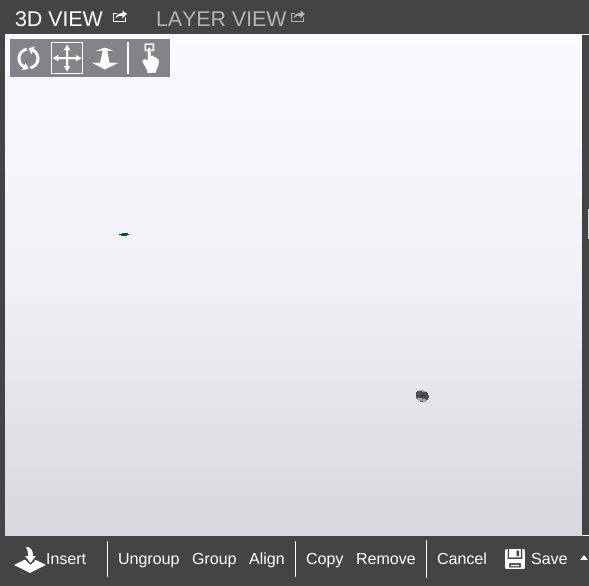
USER_MANUAL/images/oops.jpg
