seemecnc/Orion_Delta/USER_MANUAL/images/orion-heating.jpg

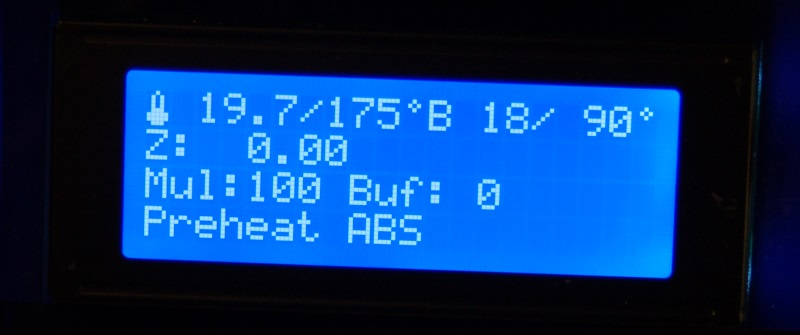
USER_MANUAL/images/orion-heating.jpg
