seemecnc/Orion_Delta/USER_MANUAL/images/orion-idle.jpg

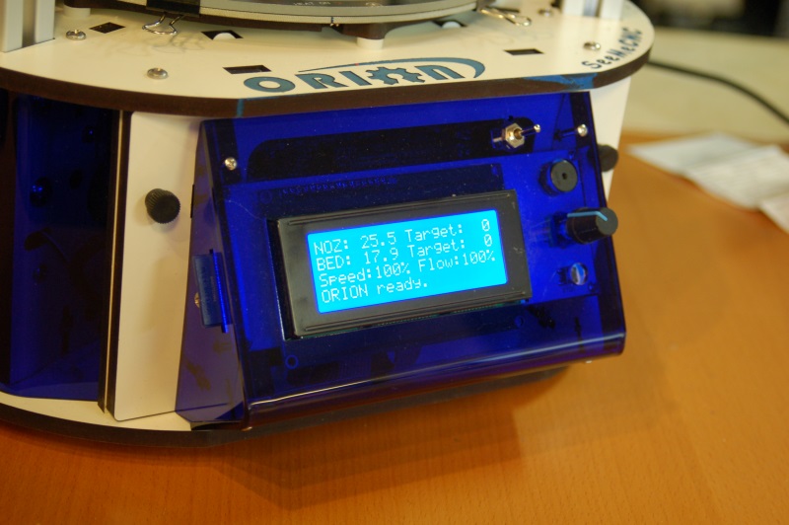
USER_MANUAL/images/orion-idle.jpg
