seemecnc/Orion_Delta/USER_MANUAL/images/orion-keychain.jpg

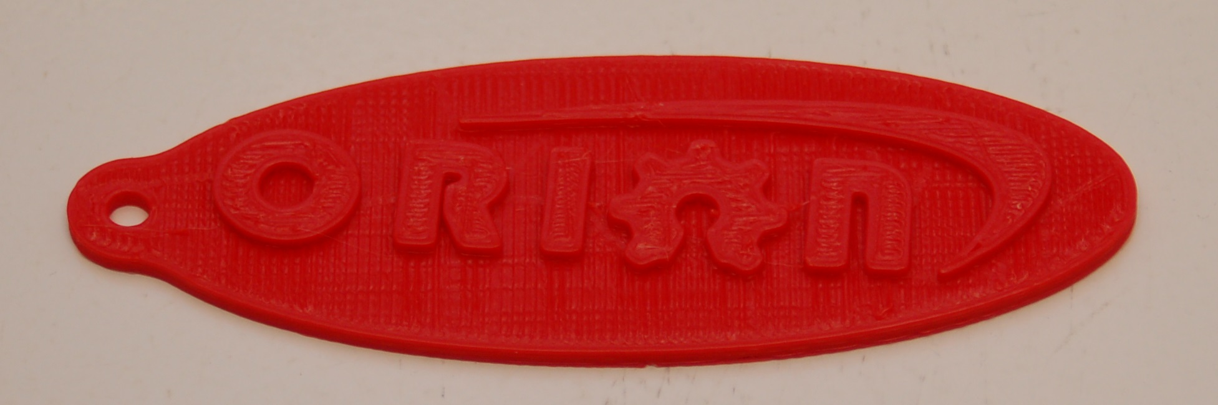
USER_MANUAL/images/orion-keychain.jpg
