seemecnc/Orion_Delta/USER_MANUAL/images/orion-signon.jpg

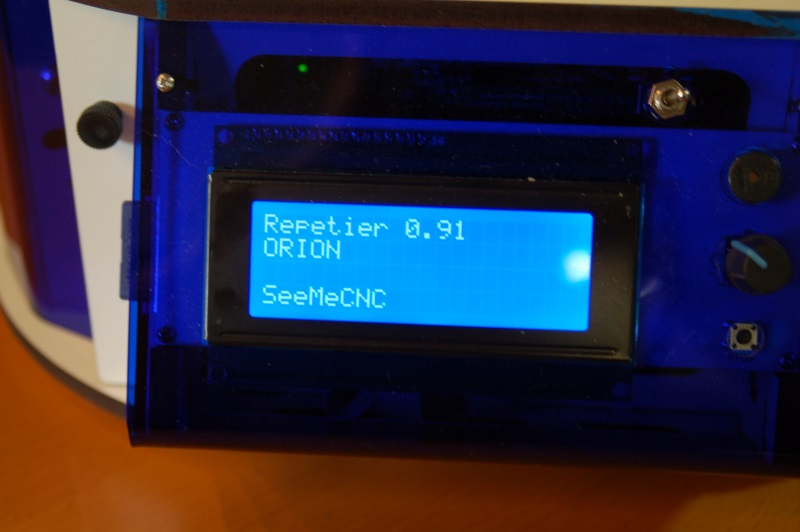
USER_MANUAL/images/orion-signon.jpg
