seemecnc/Orion_Delta/USER_MANUAL/images/part-loaded.png

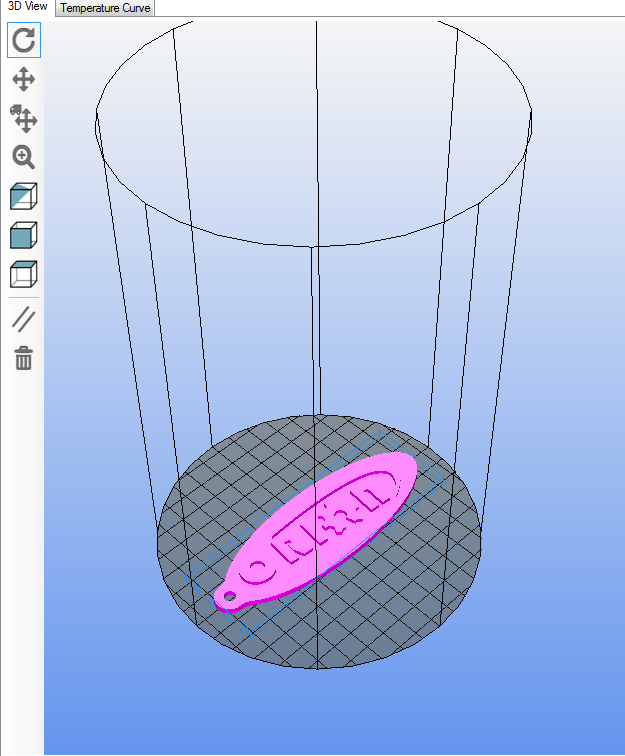
USER_MANUAL/images/part-loaded.png
