seemecnc/Orion_Delta/USER_MANUAL/images/print-file.jpg

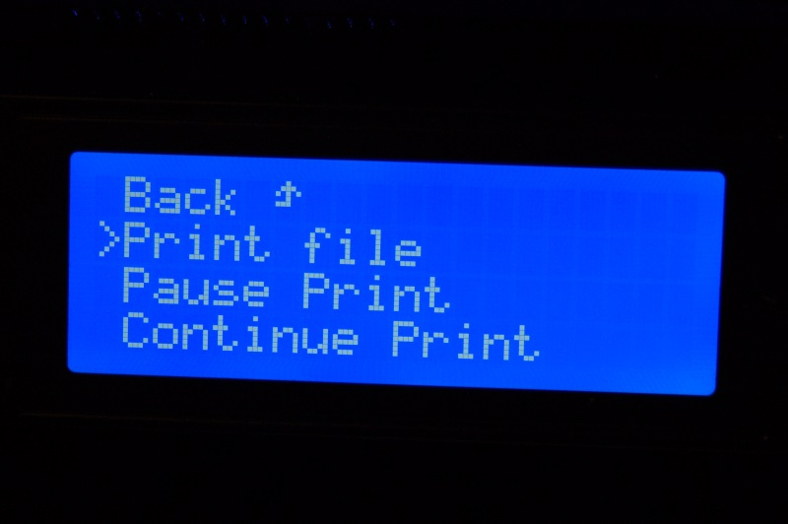
USER_MANUAL/images/print-file.jpg
