seemecnc/Orion_Delta/USER_MANUAL/images/print-stats.jpg

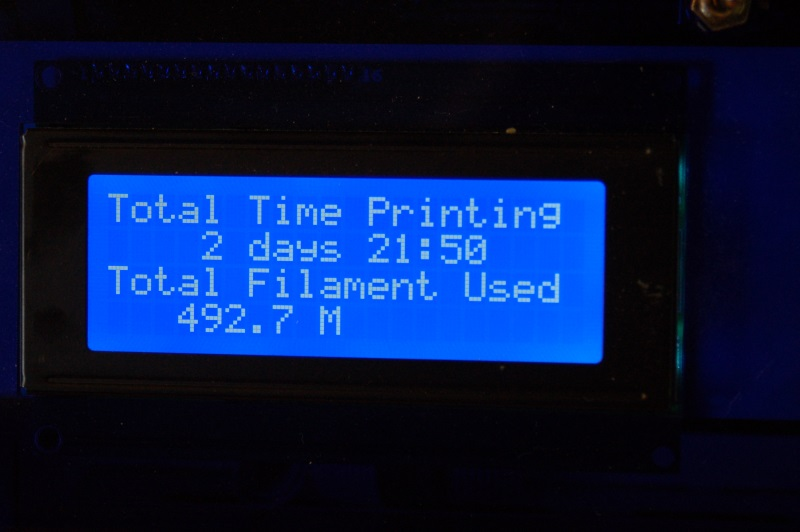
USER_MANUAL/images/print-stats.jpg
