seemecnc/Orion_Delta/USER_MANUAL/images/quick-menu.jpg

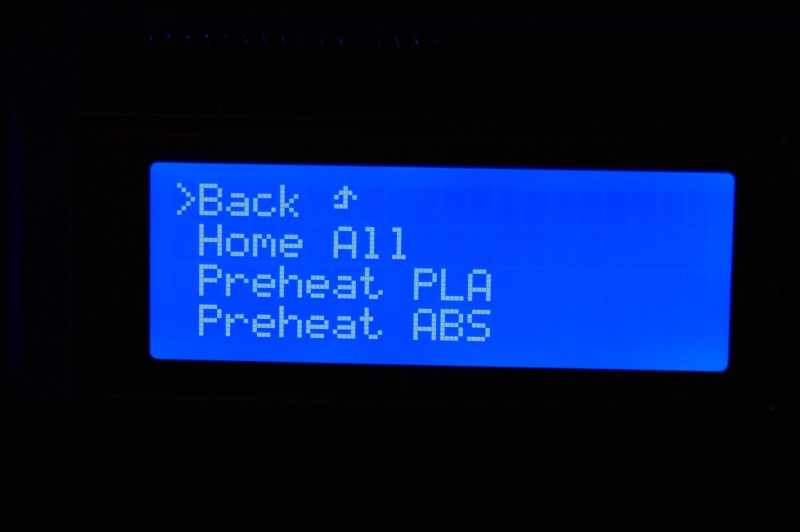
USER_MANUAL/images/quick-menu.jpg
