seemecnc/Orion_Delta/USER_MANUAL/images/quick-selected.jpg

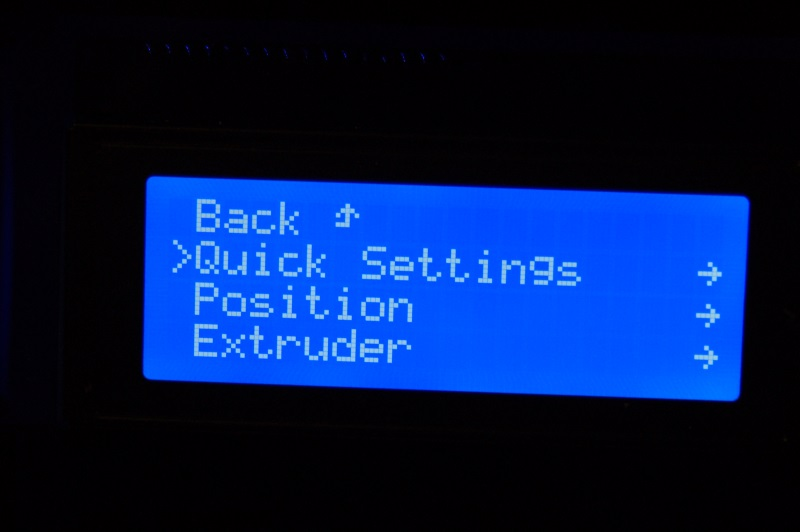
USER_MANUAL/images/quick-selected.jpg
