seemecnc/Orion_Delta/USER_MANUAL/images/rh-config-1.png

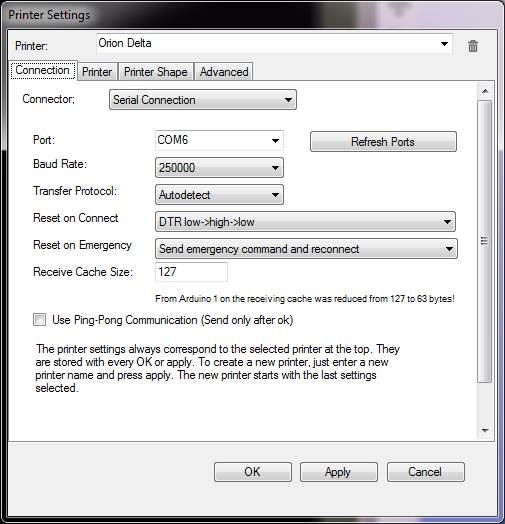
USER_MANUAL/images/rh-config-1.png
