seemecnc/Orion_Delta/USER_MANUAL/images/rh-config-2.png

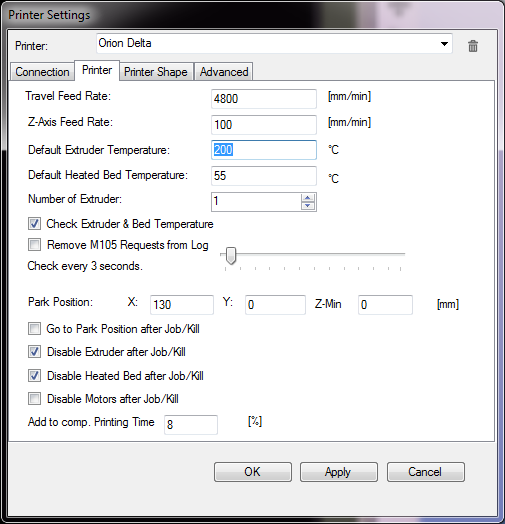
USER_MANUAL/images/rh-config-2.png
