seemecnc/Orion_Delta/USER_MANUAL/images/rh-config-3.png

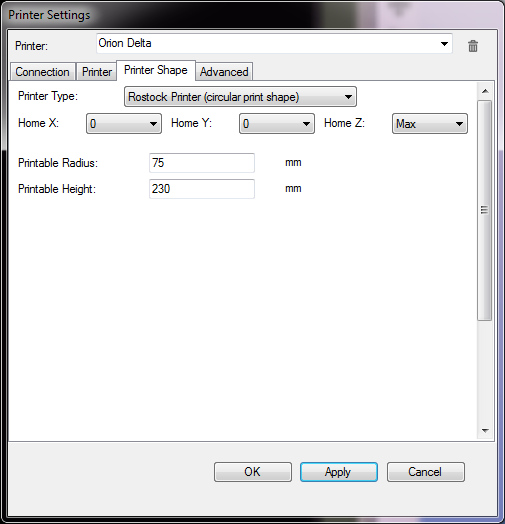
USER_MANUAL/images/rh-config-3.png
