seemecnc/Orion_Delta/USER_MANUAL/images/rh-ignite.png

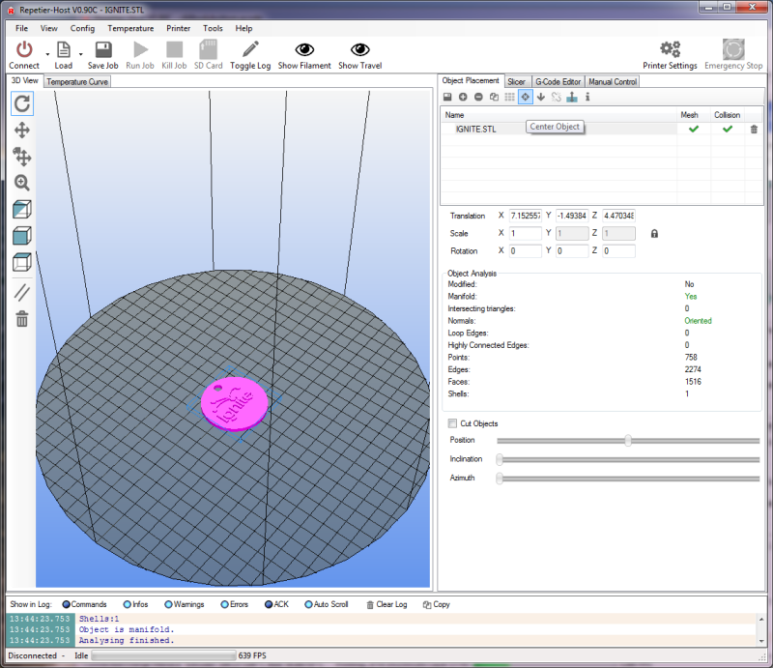
USER_MANUAL/images/rh-ignite.png
