seemecnc/Orion_Delta/USER_MANUAL/images/sd-card.jpg

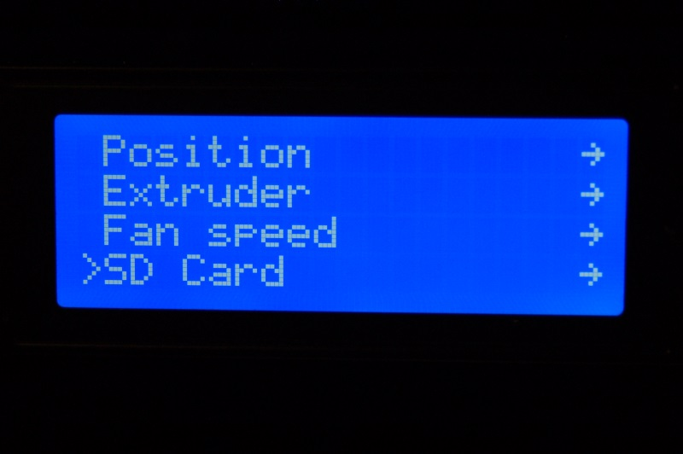
USER_MANUAL/images/sd-card.jpg
