seemecnc/Orion_Delta/USER_MANUAL/images/select-file.jpg

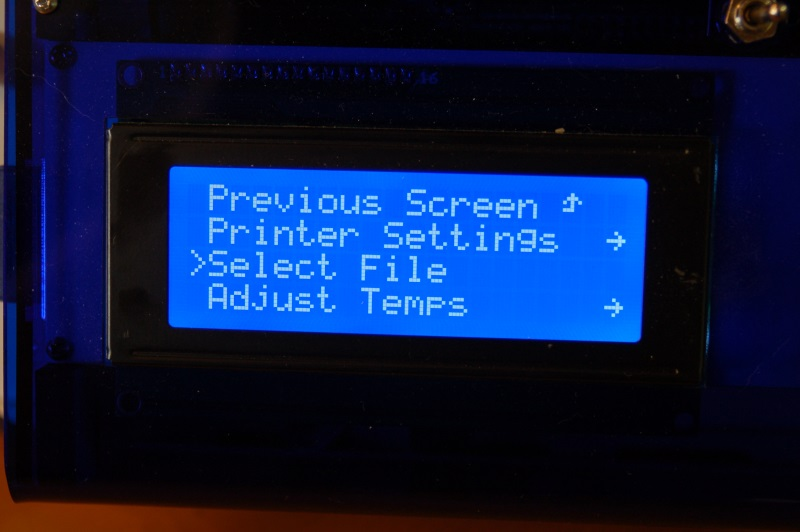
USER_MANUAL/images/select-file.jpg
