seemecnc/Orion_Delta/USER_MANUAL/images/set-z-pos.jpg

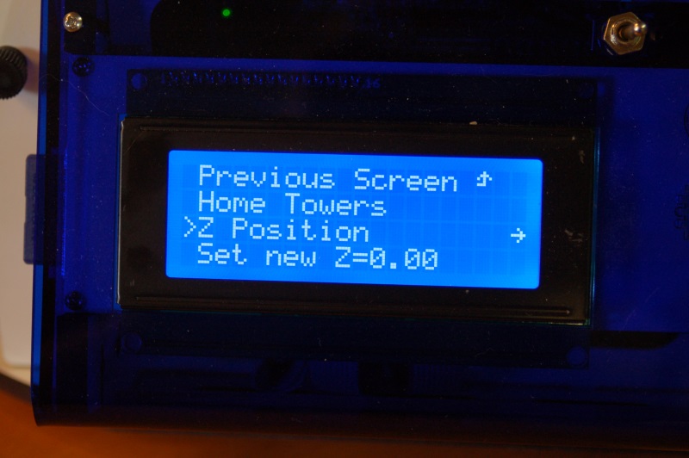
USER_MANUAL/images/set-z-pos.jpg
