seemecnc/Orion_Delta/USER_MANUAL/images/setting-temp.jpg

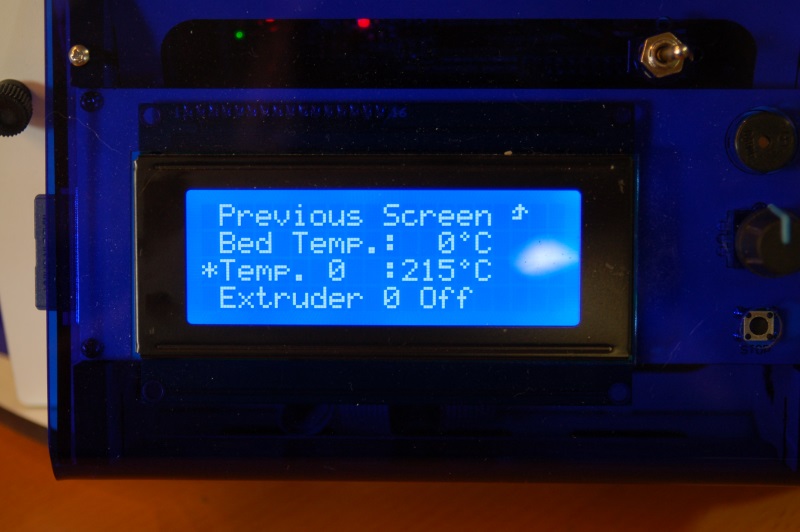
USER_MANUAL/images/setting-temp.jpg
