seemecnc/Orion_Delta/USER_MANUAL/images/slic3r-panel.png

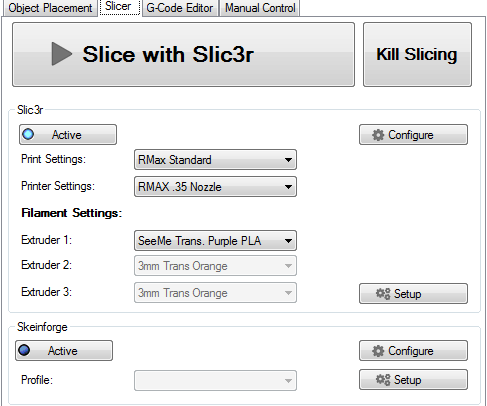
USER_MANUAL/images/slic3r-panel.png
