seemecnc/Orion_Delta/USER_MANUAL/images/slicer-config-1.png

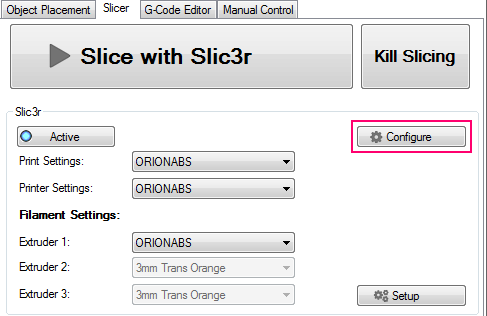
USER_MANUAL/images/slicer-config-1.png
