seemecnc/Orion_Delta/USER_MANUAL/images/slicer-configuration-screen-print-settings.png

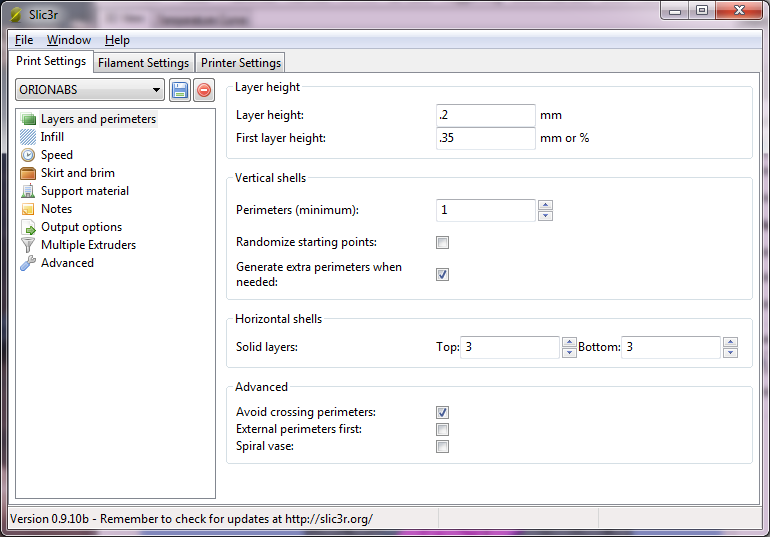
USER_MANUAL/images/slicer-configuration-screen-print-settings.png
