seemecnc/Orion_Delta/USER_MANUAL/images/slicer-filament-settings.png

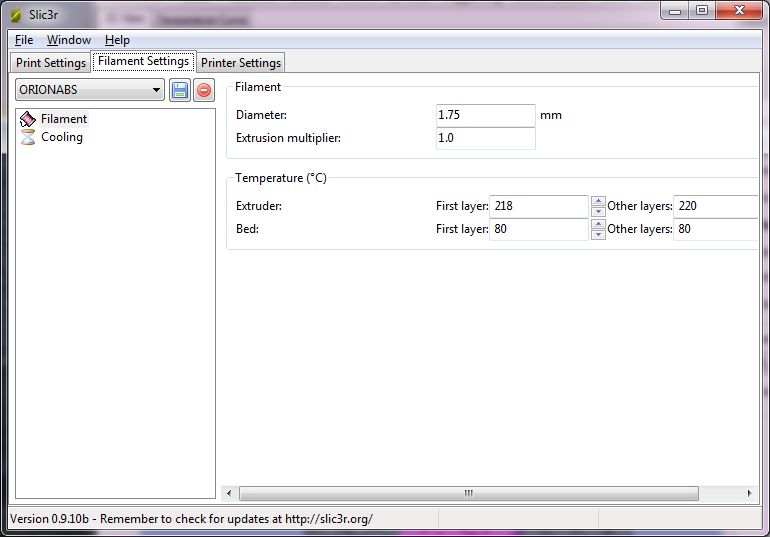
USER_MANUAL/images/slicer-filament-settings.png
