seemecnc/Orion_Delta/USER_MANUAL/images/temp-curve-annotated.png

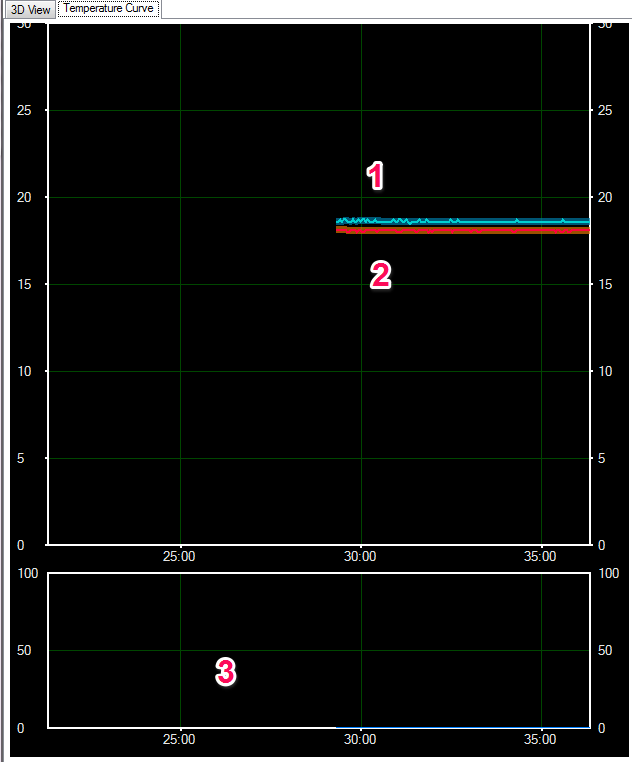
USER_MANUAL/images/temp-curve-annotated.png
