seemecnc/Orion_Delta/USER_MANUAL/images/temp-curve-at-temp.png

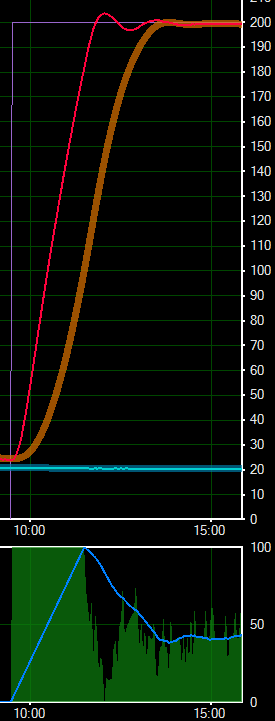
USER_MANUAL/images/temp-curve-at-temp.png
