seemecnc/Orion_Delta/USER_MANUAL/images/temp-curve-hot-end.png

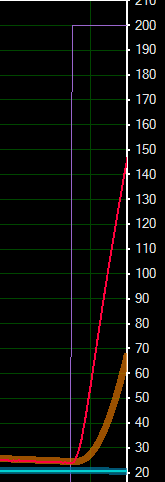
USER_MANUAL/images/temp-curve-hot-end.png
