seemecnc/Orion_Delta/USER_MANUAL/images/top-menu.jpg

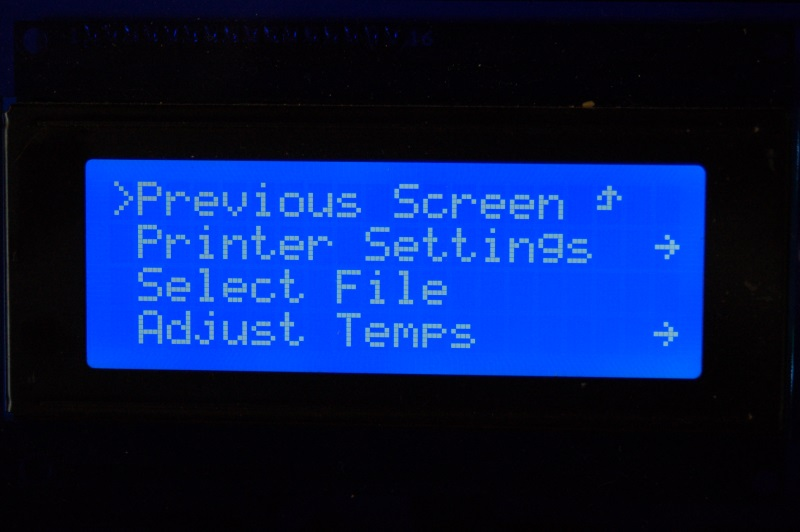
USER_MANUAL/images/top-menu.jpg
