seemecnc/Orion_Delta/USER_MANUAL/images/towers-gco.jpg

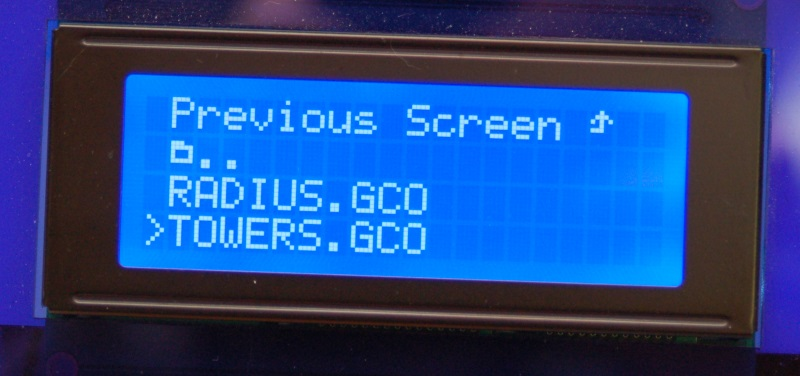
USER_MANUAL/images/towers-gco.jpg
