seemecnc/Orion_Delta/USER_MANUAL/images/z-height-display.jpg

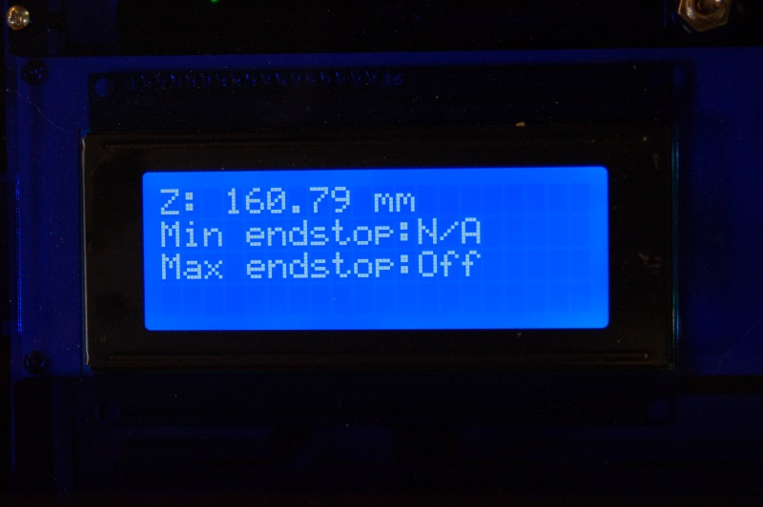
USER_MANUAL/images/z-height-display.jpg
