seemecnc/Orion_Delta/USER_MANUAL/images/z-pos-bottom.jpg

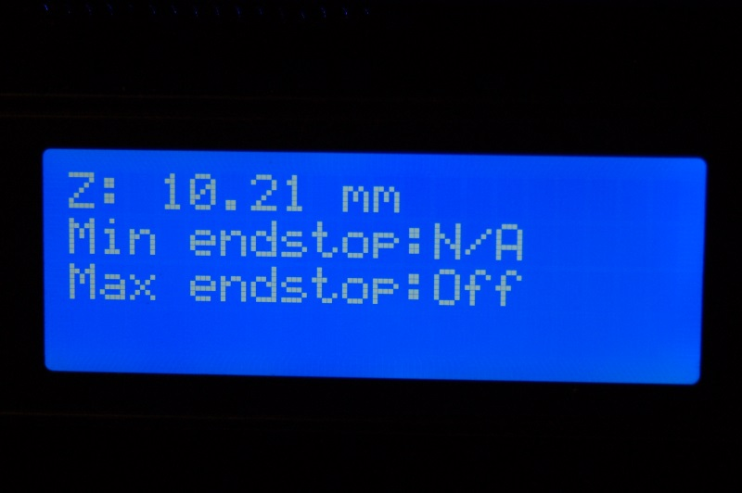
USER_MANUAL/images/z-pos-bottom.jpg
