seemecnc/Orion_Delta/USER_MANUAL/images/z-pos-fast.jpg

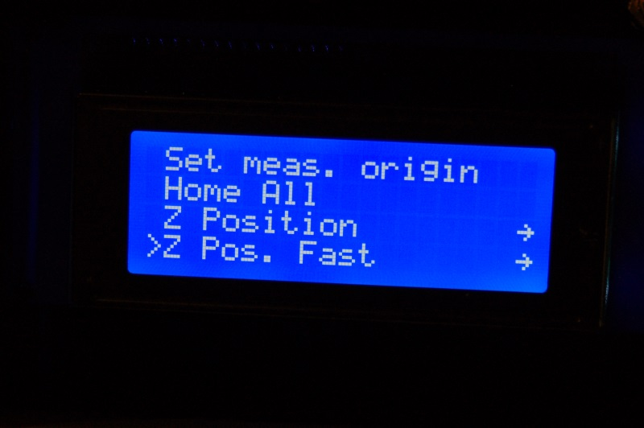
USER_MANUAL/images/z-pos-fast.jpg
