seemecnc/Orion_Delta/USER_MANUAL/images/z-pos-top.jpg

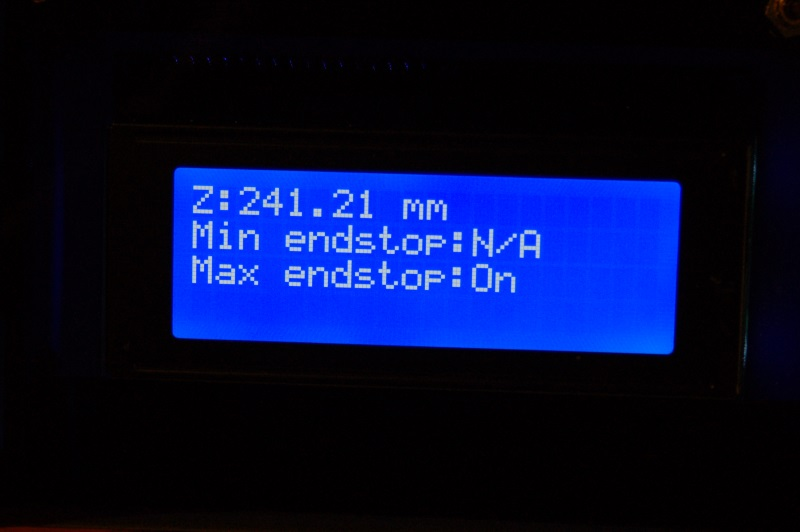
USER_MANUAL/images/z-pos-top.jpg
