seemecnc/Orion_Delta/USER_MANUAL/images/paper-test.jpg

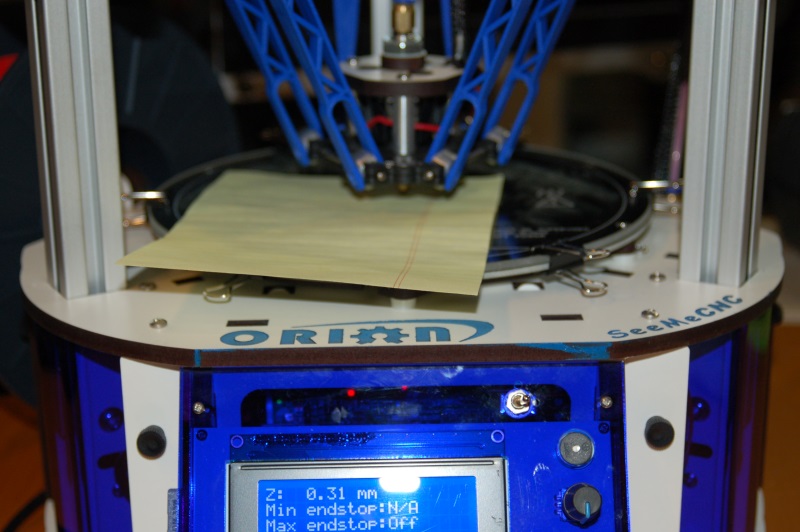
USER_MANUAL/images/paper-test.jpg
