seemecnc/Orion_Delta/USER_MANUAL/images/set-measure.jpg

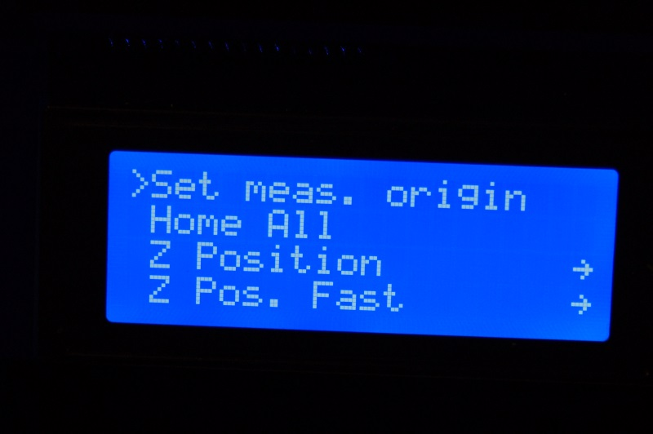
USER_MANUAL/images/set-measure.jpg
